luka1995/LPProjects-LED-Cube-8x8x8/Images/1.jpg

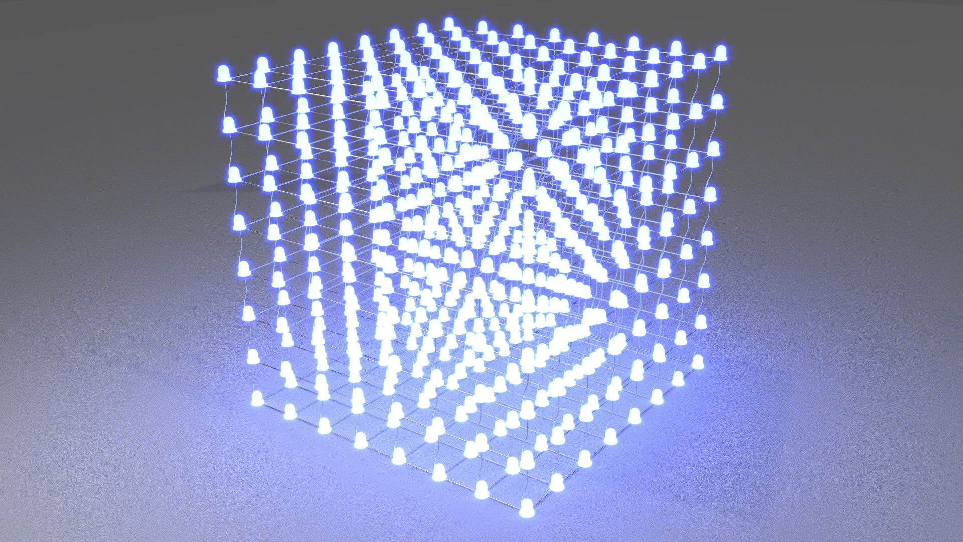
Images/1.jpg
