luka1995/LPProjects-LED-Cube-8x8x8/Images/2.jpg

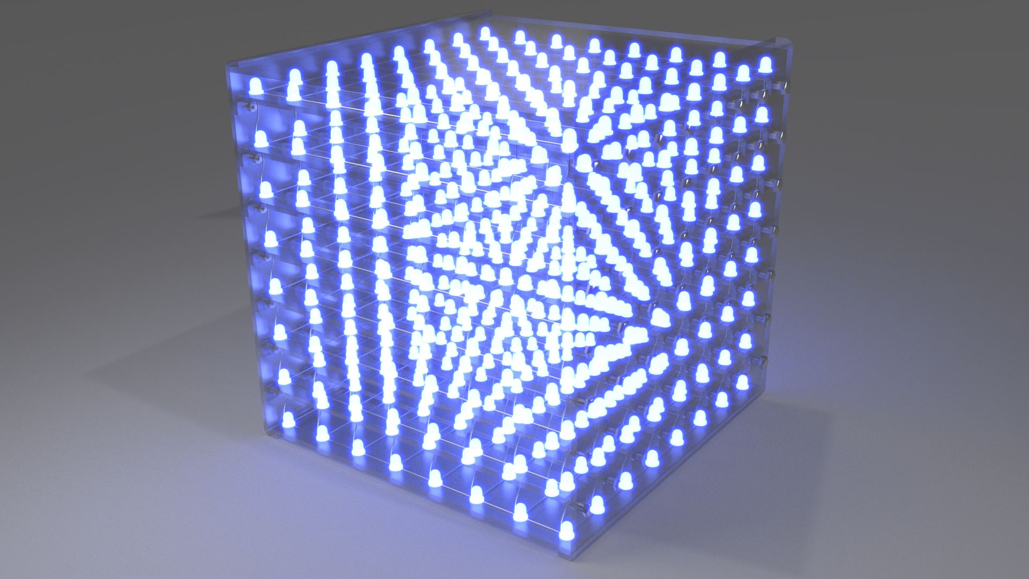
Images/2.jpg
