luka1995/LPProjects-LED-Cube-8x8x8/Images/3.jpg

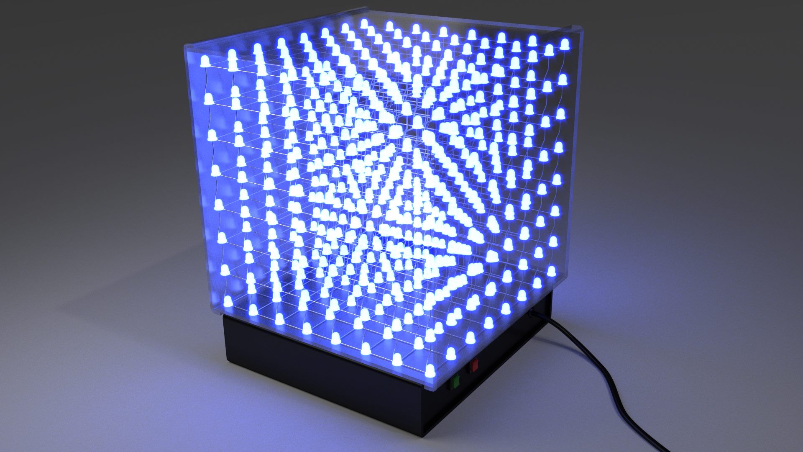
Images/3.jpg
