luka1995/LPProjects-LED-Cube-8x8x8/Images/IMG_14112014_155813.png

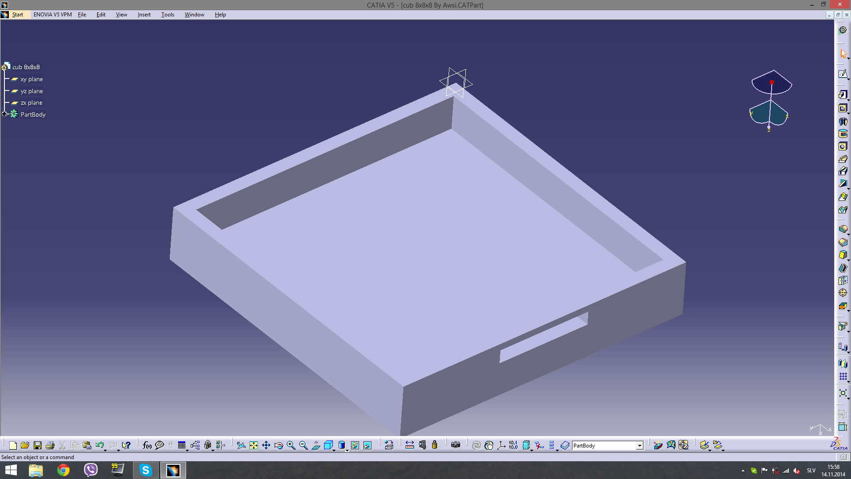
Images/IMG_14112014_155813.png
