luka1995/LPProjects-LED-Cube-8x8x8/LP_LED_CUBE_8x8x8_PCB/ver_1.0.0/Project Outputs for LP_LED_CUBE_8x8x8/PDF/Bill of Materials.PDF

Bill of Materials | Bill of Materials For Project [LP_LED_CUBE_8x8x8.PrjPcb] (No PCB Document Selected)
Source Data From: | LP_LED_CUBE_8x8x8.PrjPcb
Project: | | LP_LED_CUBE_8x8x8.PrjPcb
Variant: | | None
Creation Date: 19.8.2014 | 12:01:52
Print Date: | 19-Aug-14 | 12:01:56 PM
#Column Name Comment | #Column Name ErrDesignato r | Description | Quantity

Battery | BT1 | Multicell Battery | 1
100n | C1, C2, C3, C4, C9, C10, C12, C15, C18,
| C20 | Capacitor | 10
22p | C5, C6, C7, C8 | Capacitor | 4
220uF | C11, C14 | Capacitor | 2
0.47uF | C13, C16 | Capacitor | 2
22n | C17, C21 | Capacitor | 2
1n | C19 | Capacitor | 1
NO | C22, R2 | Capacitor, Resistor | 2
100n | C23 | Capacitor | 1
USB LED | D1 | Typical INFRARED GaAs LED | 1
LED1 | D2 | Typical INFRARED GaAs LED | 1
LED2 | D3 | Typical INFRARED GaAs LED | 1
D Schottky | D4 | Schottky Diode | 1
Schottky | D5 | Schottky Diode | 1
POWER LED | D6 | Typical INFRARED GaAs LED | 1
RS232 | J1 | Receptacle Assembly, 9 Position, Right
| | Angle | 1
Inductor | L1, L2, L3, L5, L6 | Inductor | 5
1.5uH | L4 | Magnetic-Core Inductor | 1
JTAG Connector ULINK | P1 | JTAG Connector | 1
Header 4X2A | P2 | Header, 4-Pin, Dual row | 1
USB B | P3 | USB Connector | 1
Header 8X2 | P4, P6, P7, P8 | Header, 8-Pin, Dual row | 4
Header 8 | P5 | Header, 8-Pin | 1
DC Connector | P9 | DC Power Connector | 1
NPN | Q1, Q2, Q3, Q4, Q5, Q6, Q7, Q8 | NPN Bipolar Transistor | 8
10k | R1, R5, R6, R7, R8, R9, R10, R87, R96 | Resistor | 9
2k2 | R3, R4, R97, R98, R99, R100, R101 | Resistor | 7
470R | R11, R12, R13, R91, R94, R95 | Resistor | 6
50R | R14 | Resistor | 1
4k7 | R15 | Resistor | 1
100R | R16, R17, R18, R19, R20, R21, R22, R24,
| R25, R26, R27, R28, R29, R30, R31, R32,
| R38, R39, R40, R42, R43, R44, R45, R46,
| R47, R48, R49, R50, R51, R52, R53, R54,
| R55, R56, R57, R58, R59, R60, R61, R62,
| R63, R64, R65, R66, R67, R68, R69, R70,
| R71, R72, R73, R74, R75, R76, R77, R78,
| R79, R80, R81, R82, R83, R84, R85, R86
Resistor | 64
1k | R23, R33, R34, R35, R36, R37, R41 | Resistor | 7
226k | R88 | Resistor | 1
49.9k | R89 | Resistor | 1
100k | R90 | Resistor | 1
75R | R92, R93 | Resistor | 2
4k7 | R102 | Resistor | 1
LPC1768FBD10
0 | U1 | 32-bit ARM Cortex-M3 microcontroller; up to
| | 512 kB flash and 64 kB SRAM with
| | Ethernet, USB 2.0 Host/Device/OTG, CAN | 1
MAX2232 | U2 | Dual 232 +3V3 | 1
AT45DB321D | U3 | SPI Flash 32MB | 1
PCA9555 | U4, U5, U6, U7 | I2C I/O Ports | 4
TPS56528 | U8 | Step-Down Converter 5A 4.5V-18V | 1
RJ45 Ethernet | U9 | Ethernet Connector | 1
DP83848C | U10 | Ethernet PHY | 1
Jumper | W1, W2 | Jumper Wire | 2
32.768KHz | Y1 | Crystal Oscillator | 1
12MHz | Y2 | Crystal Oscillator | 1
XTAL 50MHz | Y3 | | 1
Approved Notes | 171
