luka1995/LPProjects-LED-Cube-8x8x8/PCB/Ver 4.1.0/PCB_Controller/PDF/Schematic.PDF

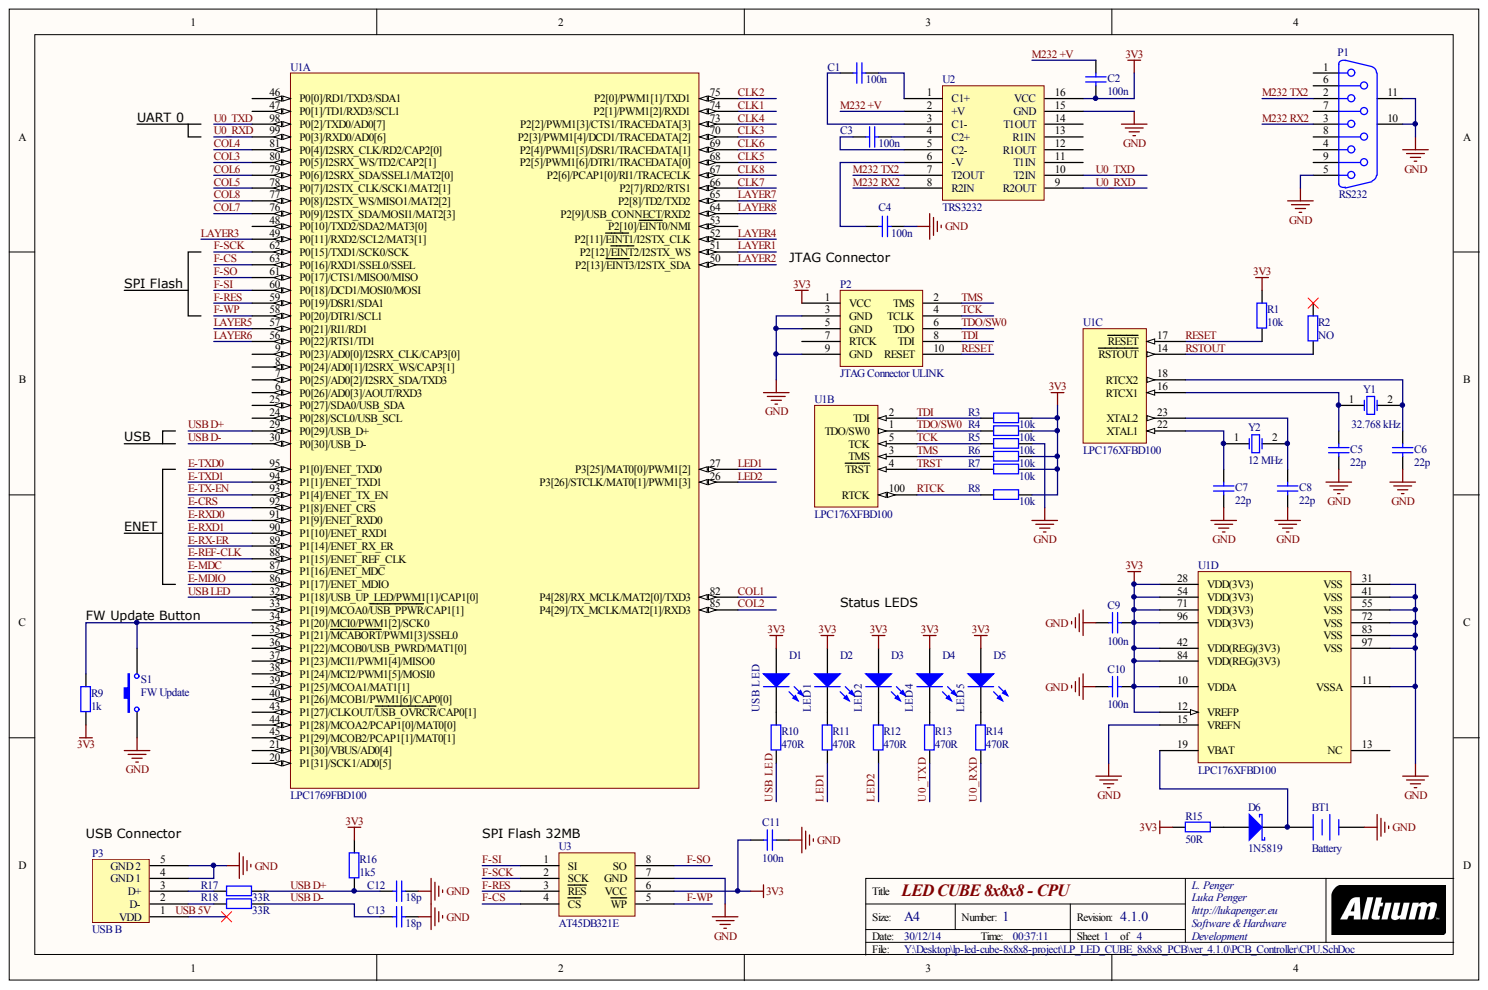
[picture p26: page 1]

LED CUBE 8x8x8 - CPU
Title
Date:
Y:\Desktop\lp-led-cube-8x8x8-project\LP_LED_CUBE_8x8x8_PCB\ver_4.1.0\PCB_Controller\CPU.SchDoc
File:

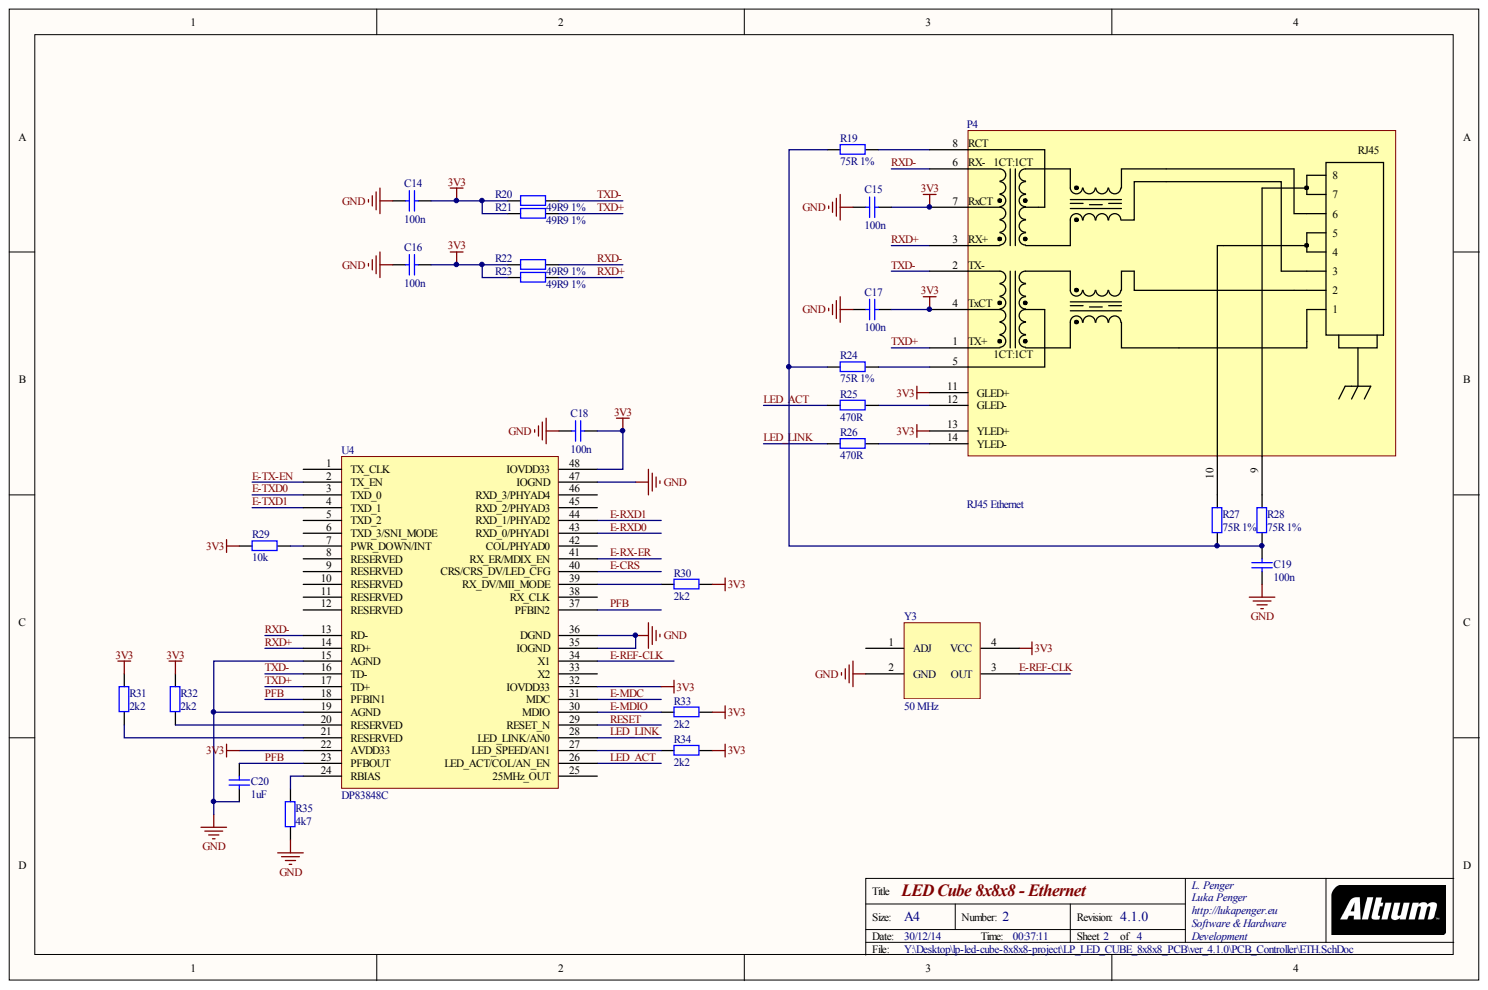
[picture p27: page 2]

GND | 75R1% RXD-6 100n 100n R24 | 1CT:1CT RxCT | 8 7 6 5 4 3 2 1

RESERVED 20 | E-MDIO RESET

RESERVED 21 AVDD33 22 PFBOUT 23 | LED_LINK LED_ACT

Title LED Cube 8x8x8 - Ethernet | L. Penger Luka Penger http://lukapenger.eu Software & Hardware Development

Size: A4 | Number: 2 | Revision: 4.1.0

1 2 | Date: 30/12/14 Time: 00:37:11 Sheet 2 of 4 File: Y:\Desktop\lp-led-cube-8x8x8-project\LP_LED_CUBE_8x8x8_PCB\ver_4.1.0\PCB_Controller\ETH.SchDoc 3 4

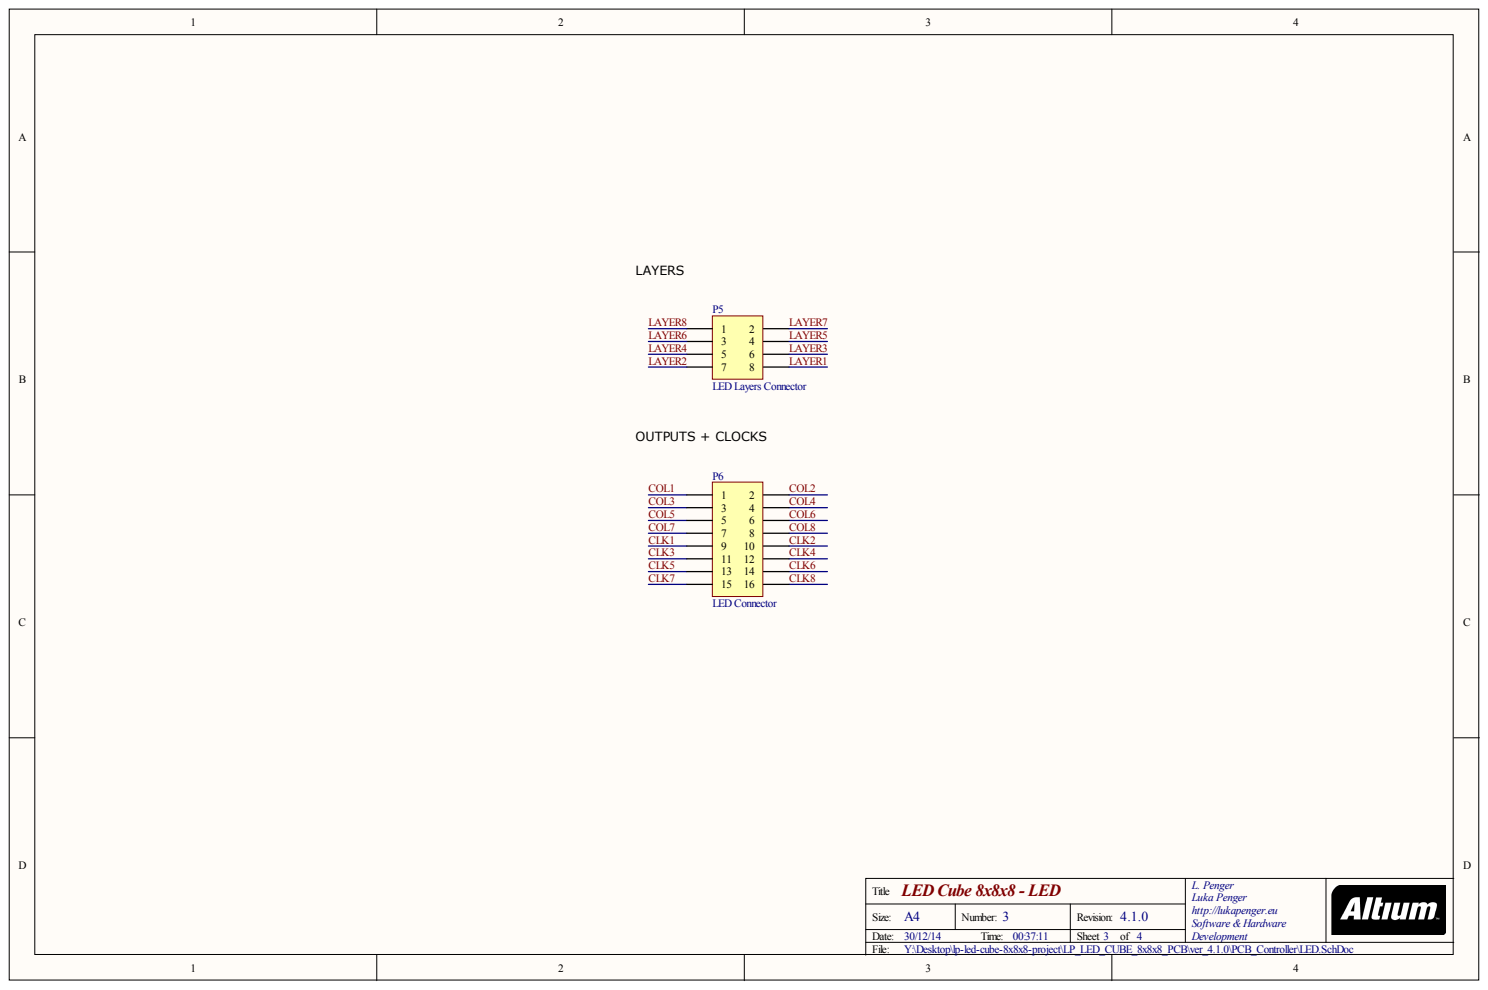
[picture p28: page 3]

Title LED Cube 8x8x8 - LED | L. Penger Luka Penger http://lukapenger.eu Software & Hardware Development

Size: A4 | Number: 3 | Revision: 4.1.0

1 2 | Date: 30/12/14 Time: 00:37:11 Sheet 3 of 4 File: Y:\Desktop\lp-led-cube-8x8x8-project\LP_LED_CUBE_8x8x8_PCB\ver_4.1.0\PCB_Controller\LED.SchDoc 3 4

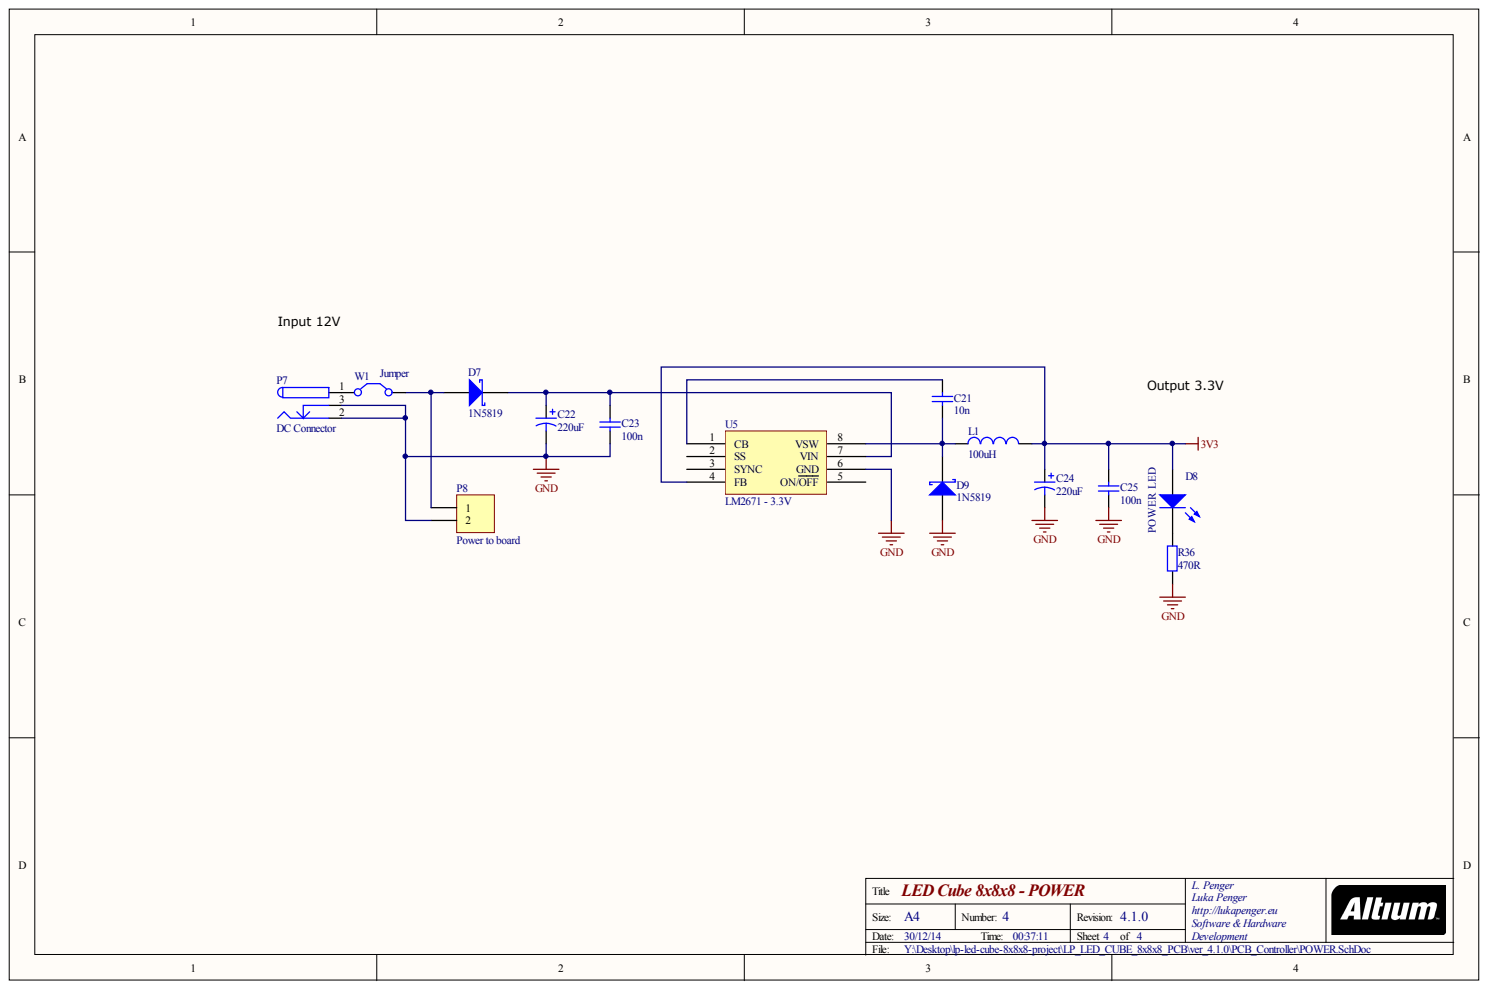
[picture p29: page 4]

: A4 | Numb er : 4 | Re vis io n: 4.1.0
Date : 3 0 / 1 2 / 1 4 Time : 0 0 : 3 7 : 1 1 F ile : Y :\D e s ktop \lp -le d -cub e -8 x8 x8 -p roj e c t\LP | S he e t 4 o f 4 _LED_C UBE_ 8 x8 x8 _P C | B\ver_4 . 1 . 0 \P C B_C o ntro ller\P O | WER. S c hDo c

LED Cub e 8x8x8 -PO WER | L L . u Penge k a P enge r r h t tp : //lu k ap enge r. e u Soft w a re & Ha rdw a re De v e lop m e n t

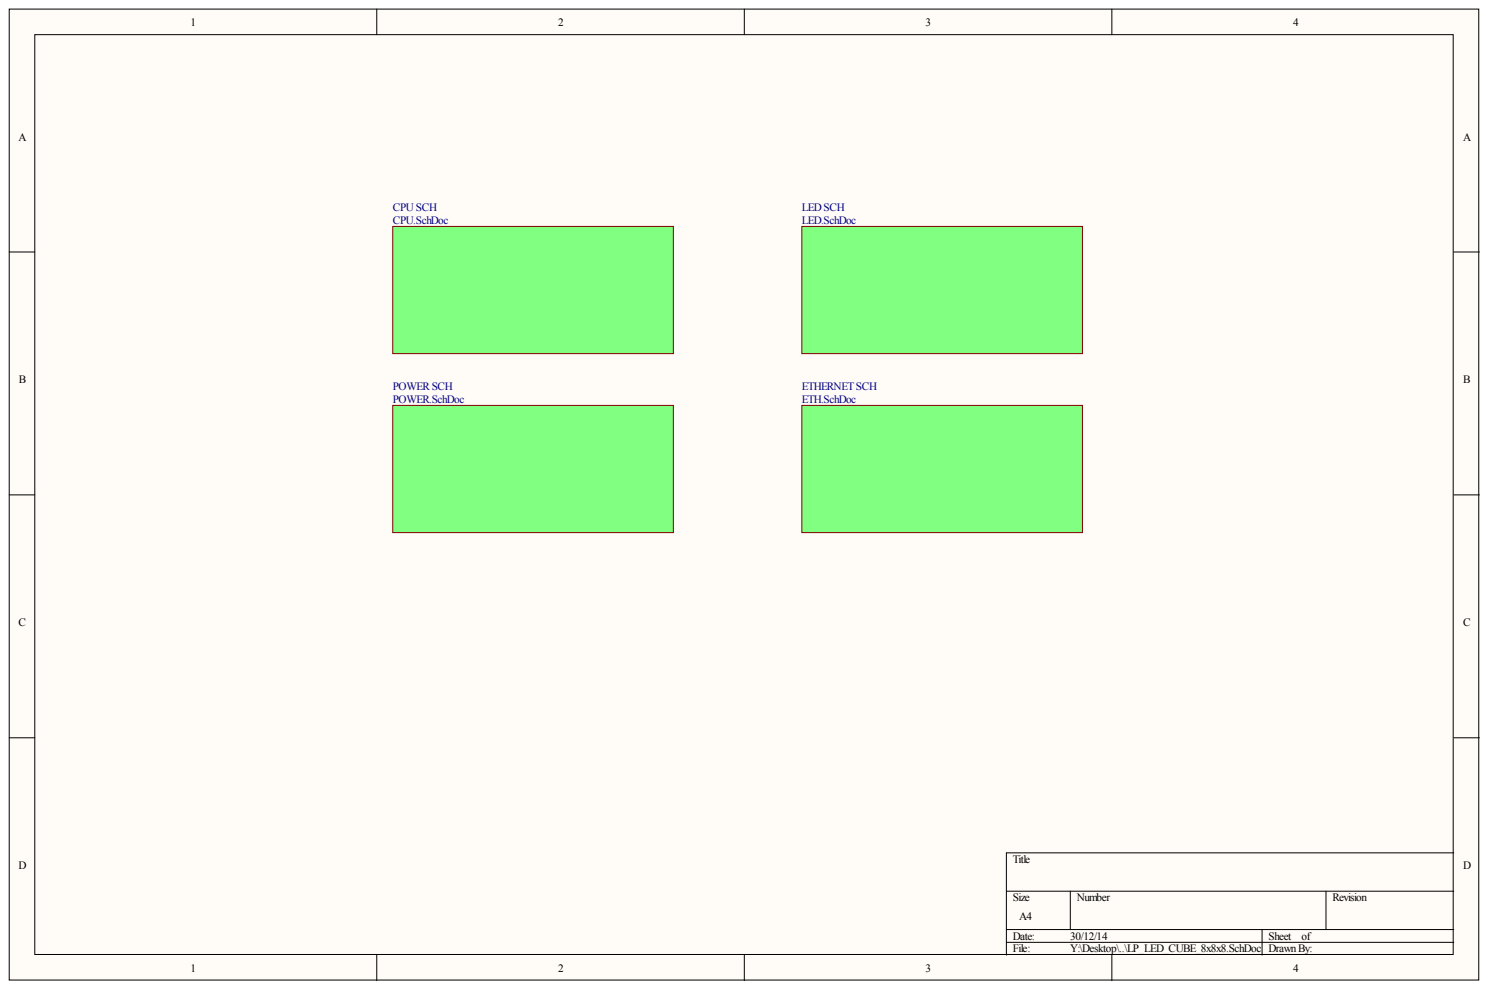
[picture p30: page 5]

Size A4 | Number | Revision

1 2 3 | Date: 30/12/14 File: Y:\Desktop\..\LP_LED_CUBE_8x8x8.SchDoc | Sheet of DrawnBy: 4
