luka1995/LPProjects-LED-Cube-8x8x8/PCB/Ver 4.1.0/PCB_Board/PDF/BOTTOM Layer.PDF

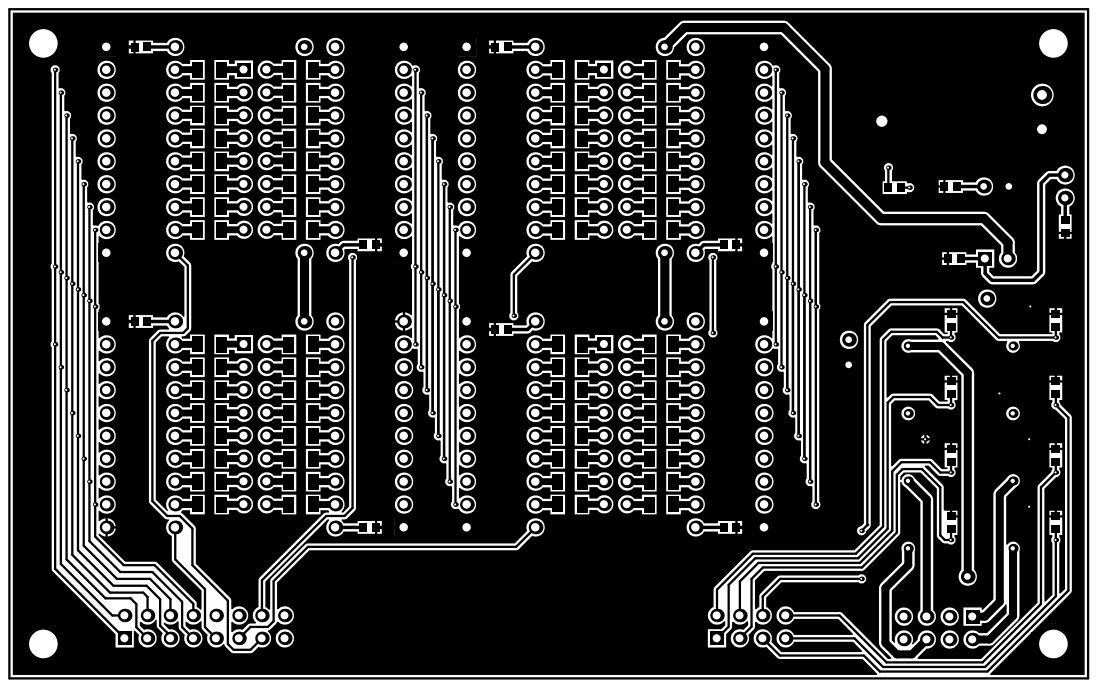
[picture p31: page 1]
