luka1995/LPProjects-LED-Cube-8x8x8/PCB/Ver 4.1.0/PCB_Board/PDF/TOP Overlay.PDF

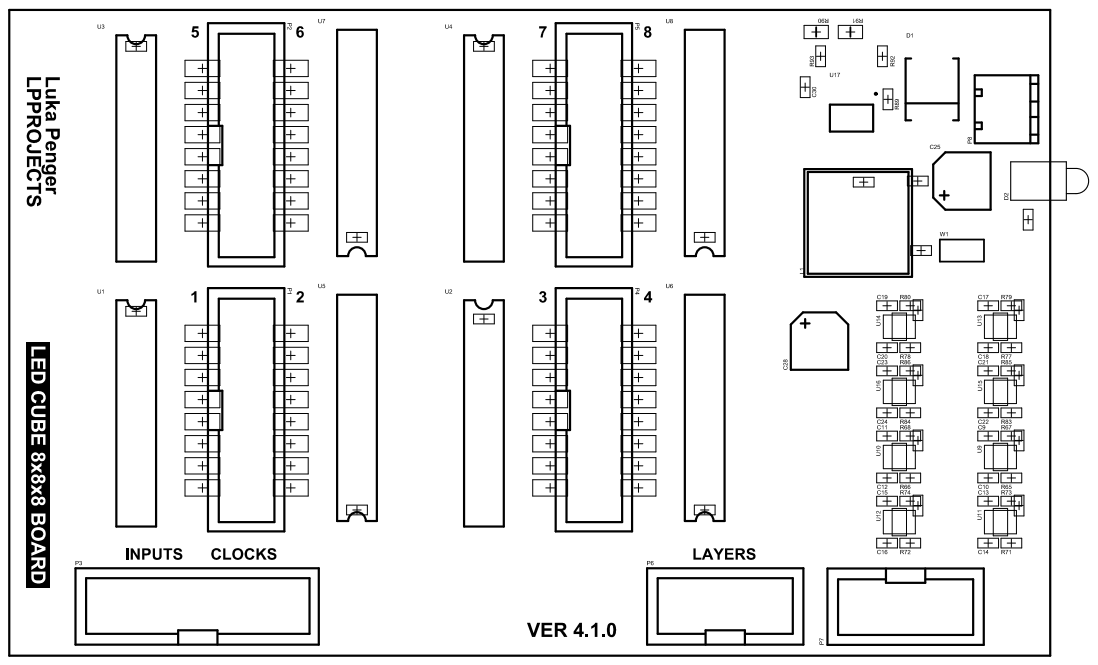
[picture p34: page 1]
