luka1995/LPProjects-LED-Cube-8x8x8/PCB/Ver 4.1.0/PCB_Controller/PDF/TOP Layer.PDF

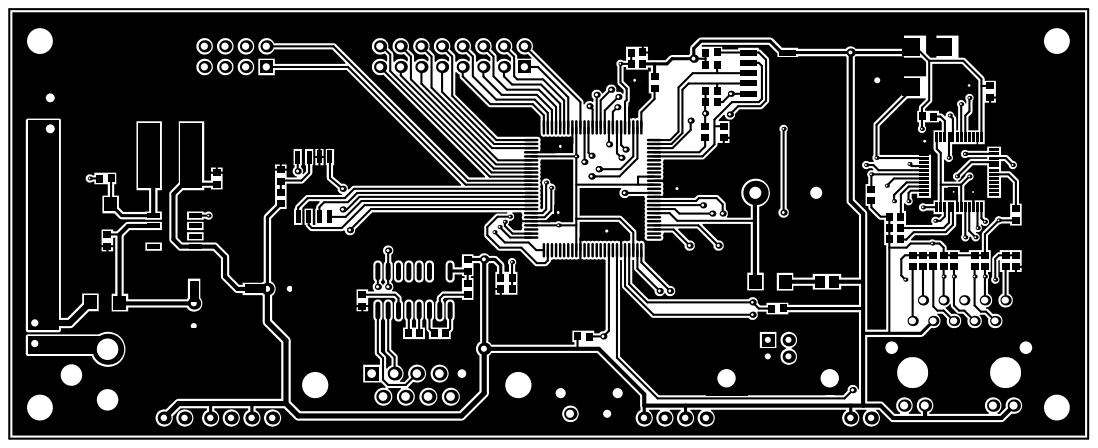
[picture p37: page 1]
