luka1995/LPProjects-LED-Cube-8x8x8/LP_LED_CUBE_8x8x8_PCB/ver_1.0.0/Project Outputs for LP_LED_CUBE_8x8x8/PDF/Schematic.PDF

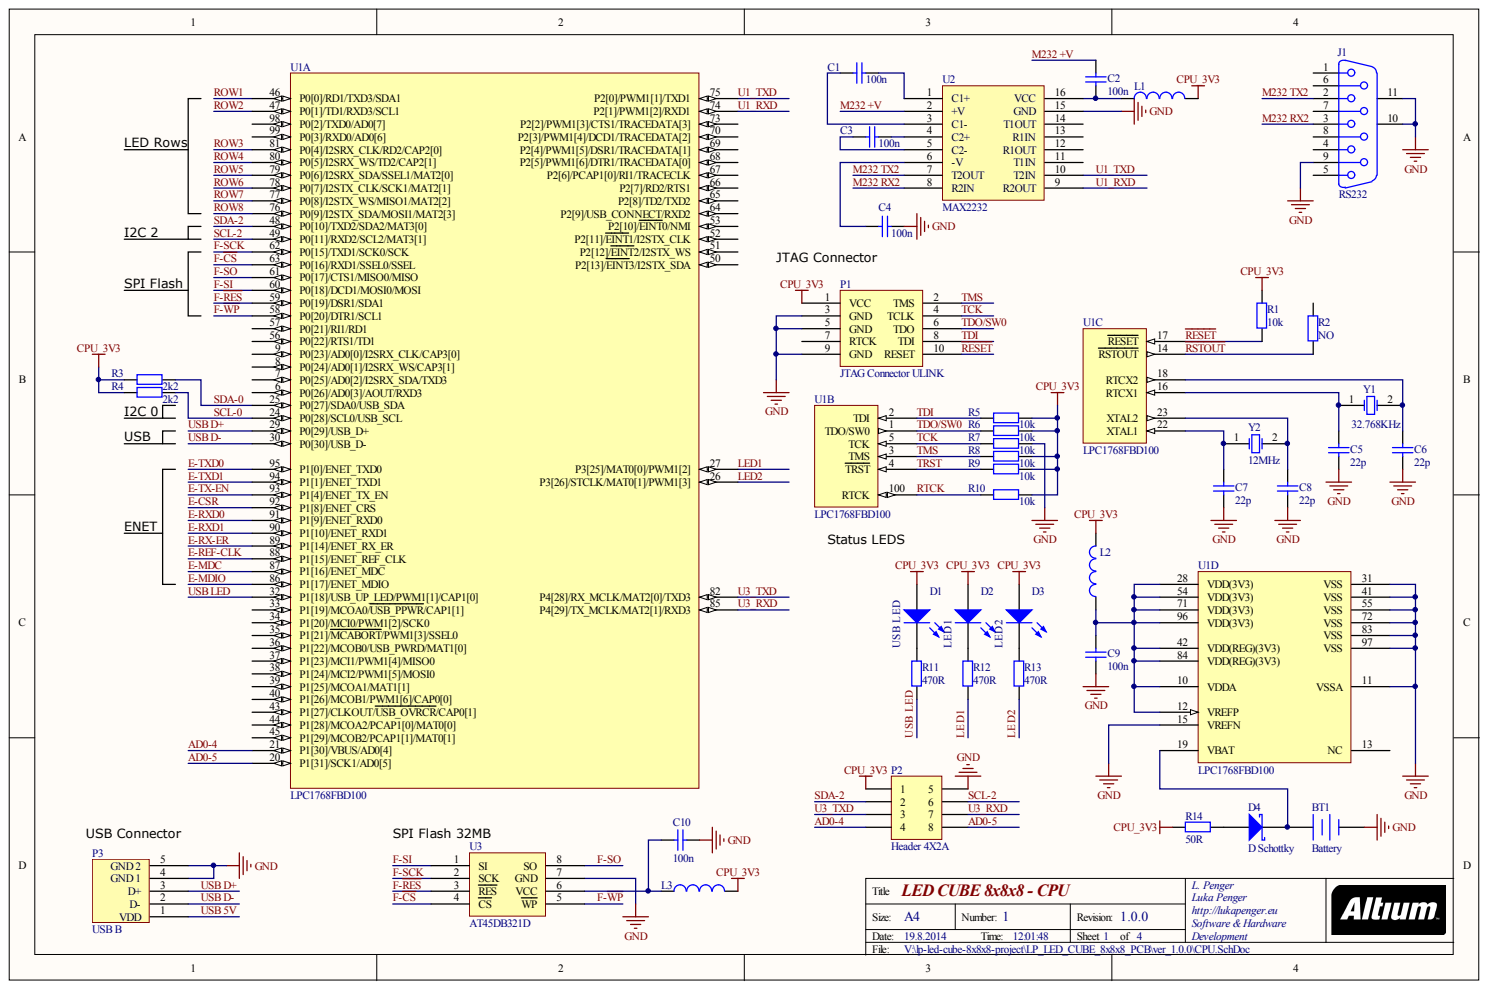
[picture p44: page 1]

LED CUBE 8x8x8 - CPU
Title
V:\lp-led-cube-8x8x8-project\LP_LED_CUBE_8x8x8_PCB\ver_1.0.0\CPU.SchDoc
File:

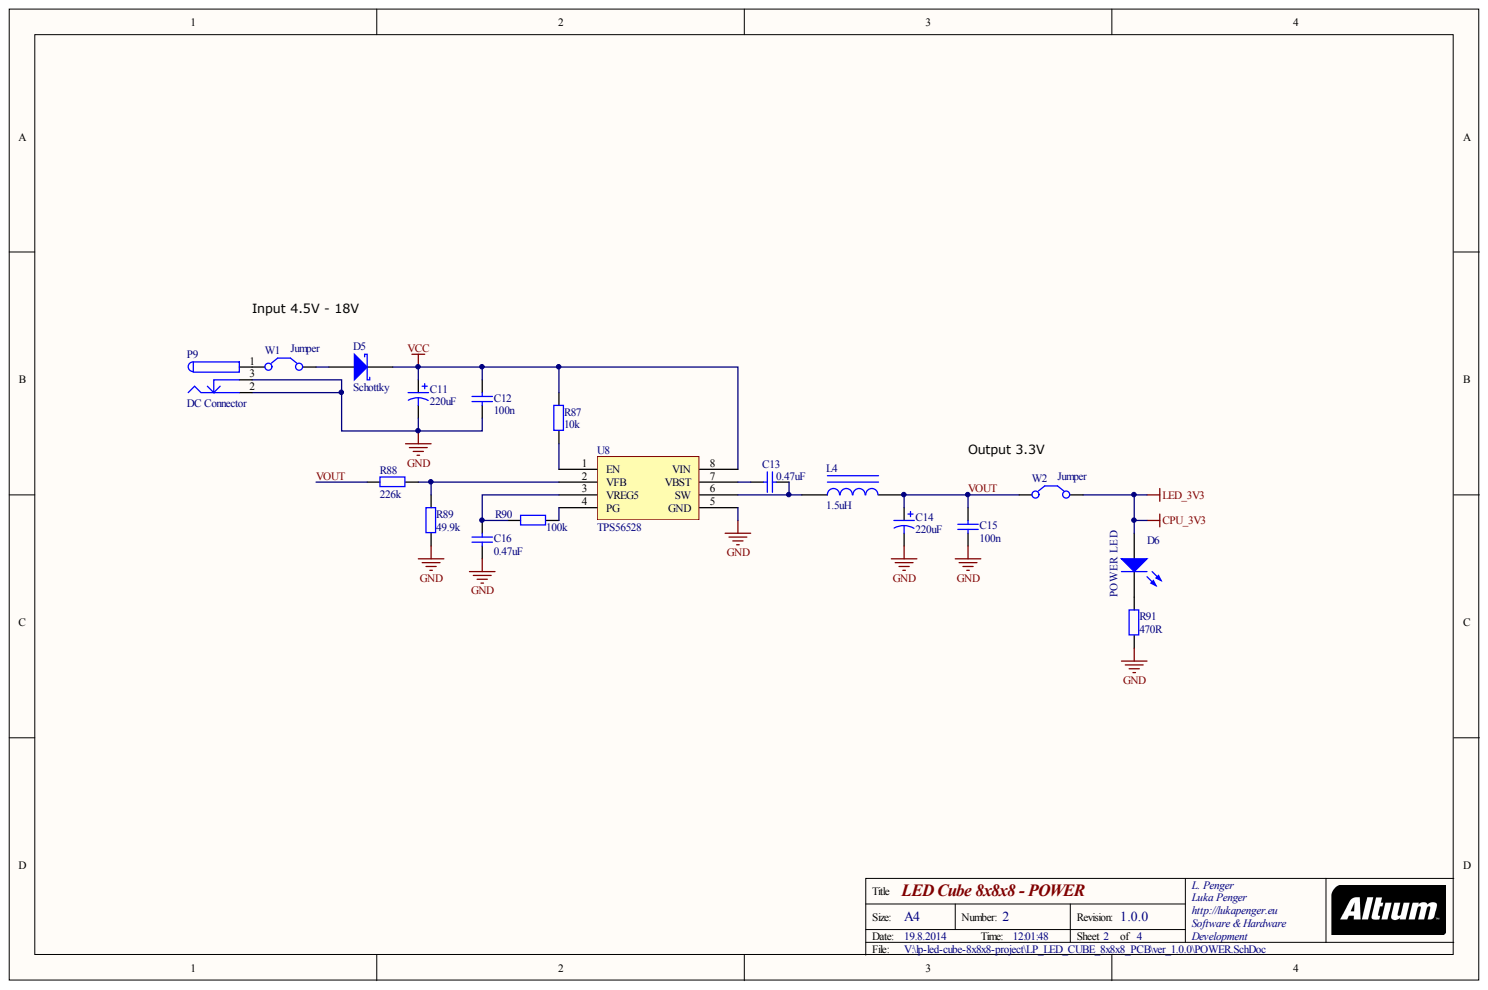
[picture p45: page 2]

: A4 | Numb er : 2 | Re vis io n: 1.0.0
Date : 1 9 . 8 . 2 0 1 4 Time : 1 2 : 0 1 :4 8 F ile : V :\lp -le d -cub e -8 x8 x8 -p roj e c t\LP _LED_C | S he e t 2 o f 4 UBE_ 8 x8 x8 _P C B\ver_ 1 | . 0 . 0 \P O WER. S c hDo c

LED Cub e 8x8x8 -PO WER | L L . u Penge k a P enge r r h t tp : //lu k ap enge r. e u Soft w a re & Ha rdw a re De v e lop m e n t

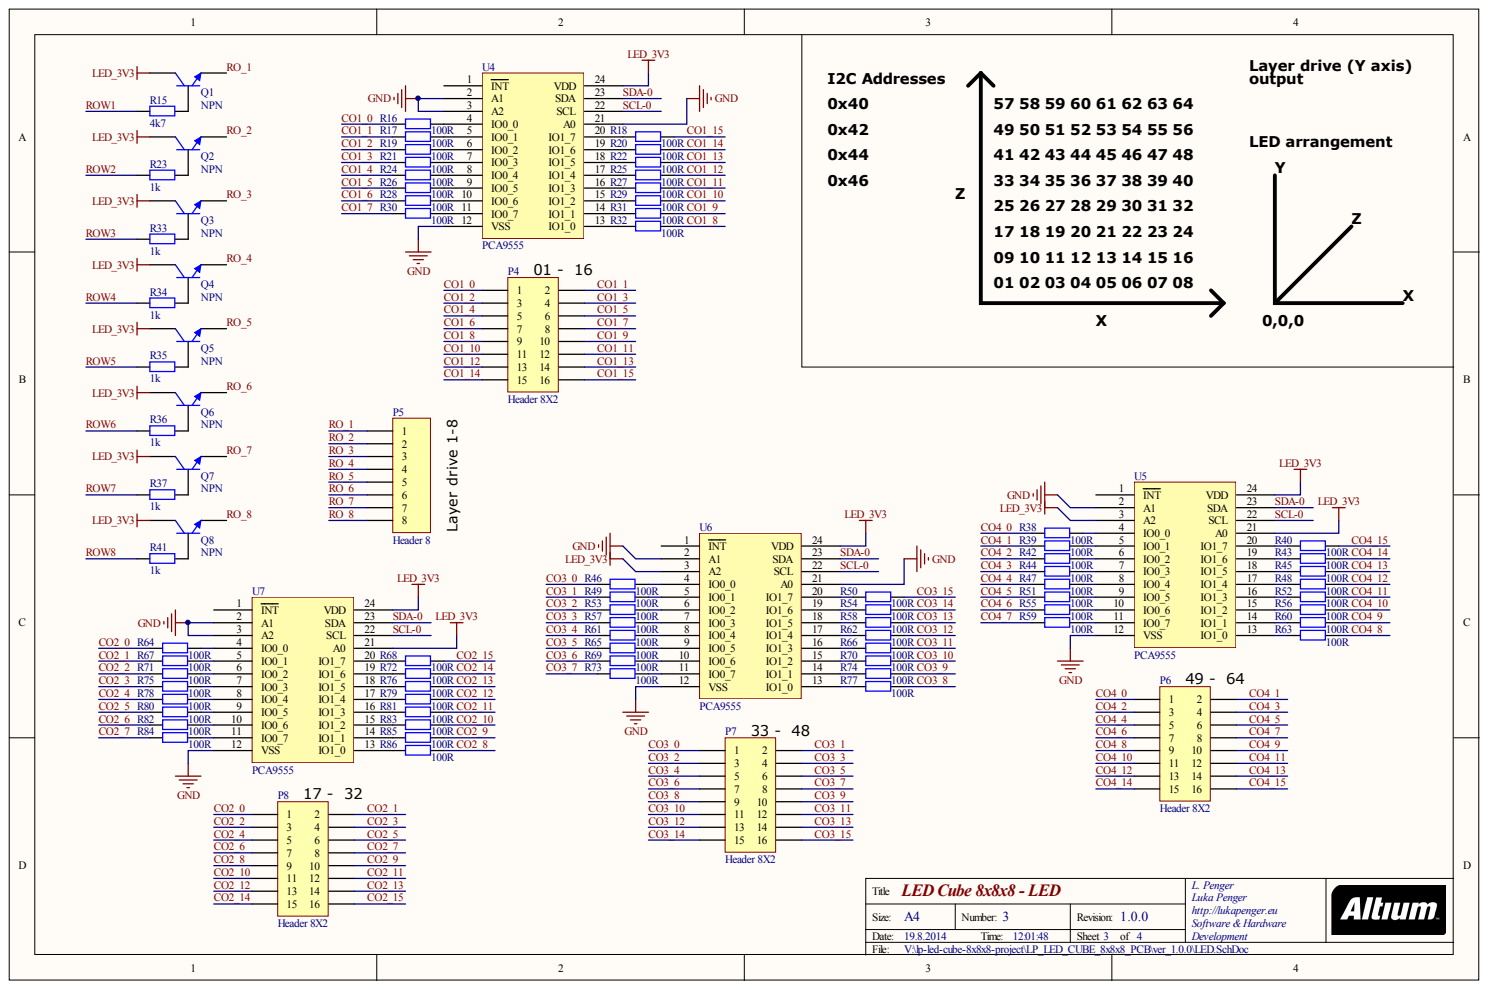
[picture p46: page 3]

LED_3V3

Layer drive (Y axis) output

R79 100R CO2_12 R81 100R CO2_11 PCA9555 R83 100R CO2_10 33 - 48 | 1 2 3 4 5 6 7 8 9 11 12 10 13 14 15 16

LED Cube 8x8x8 - LED
Title
V:\lp-led-cube-8x8x8-project\LP_LED_CUBE_8x8x8_PCB\ver_1.0.0\LED.SchDoc
File:

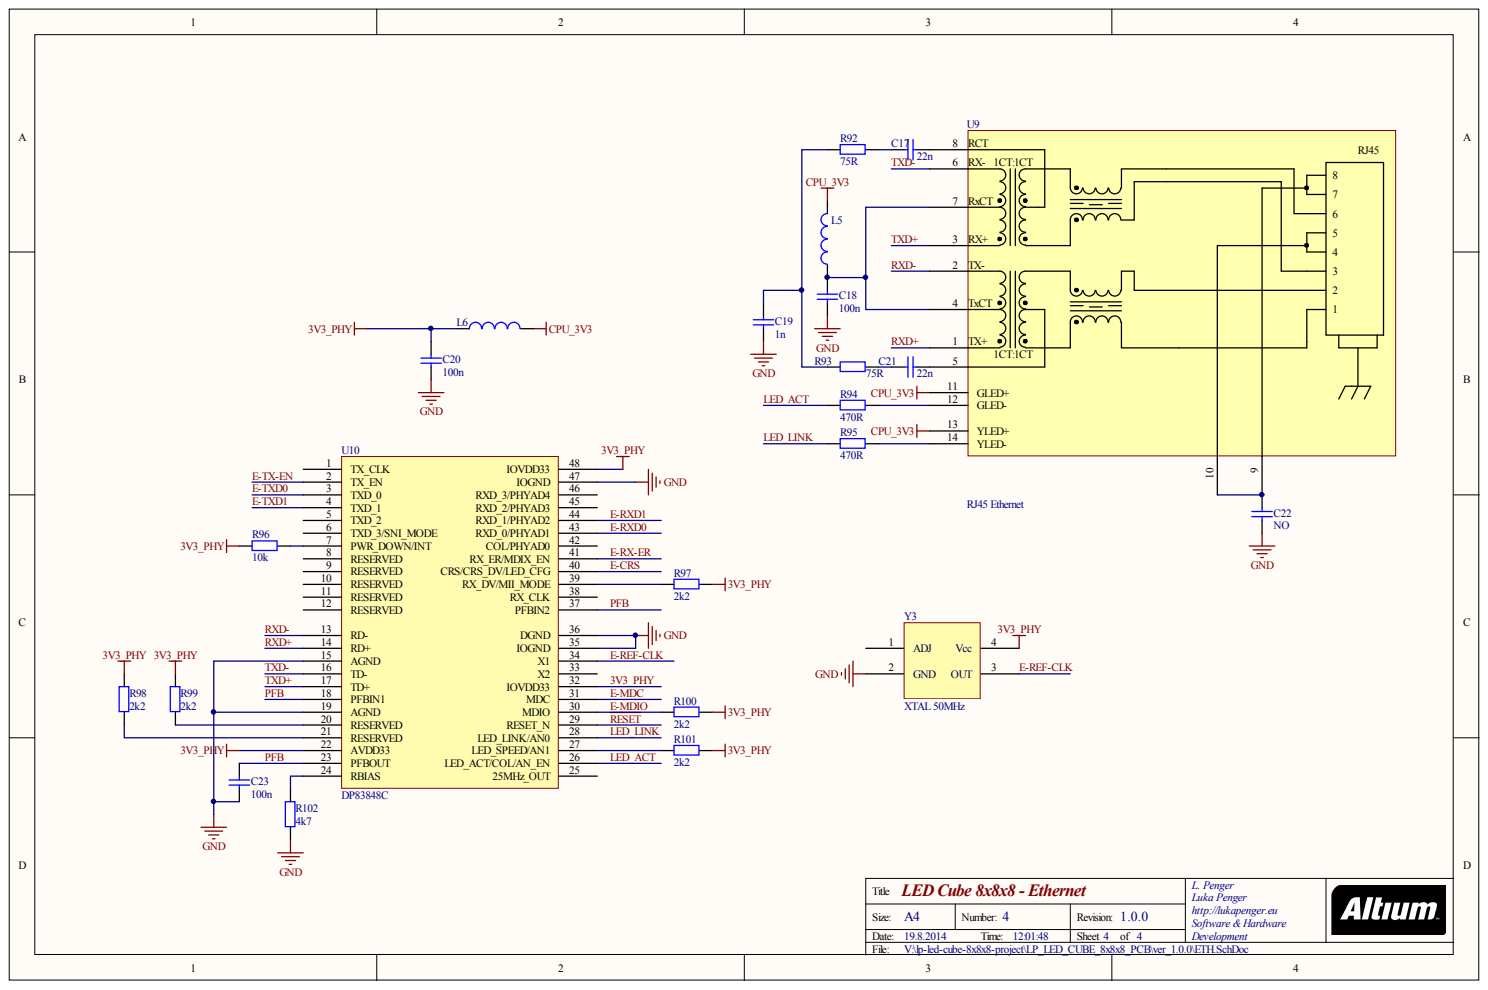
[picture p47: page 4]

TX+ TxCT TX- RX+ RxCT RX- RCT U9RJ45 Etherne
TXD+ TXD-

2 0 | 3 1 E-MDC 3 0 E-MDI O 2 9 RES ET

: A4 | Numb er : 4 | Re vis io n: 1.0.0
Date : 1 9 . 8 . 2 0 1 4 Time : 1 2 : 0 1 :4 8 F ile : V :\lp -le d -cub e -8 x8 x8 -p roj e c t\LP _LED_C | S he e t 4 o f 4 UBE_ 8 x8 x8 _P C B\ver_ 1 | . 0 . 0 \ETH . S c hDo c

LED Cub e 8x8x8 -Eth e rn e t | L L . u Penge k a P enge r r h t tp : //lu k ap enge r. e u Soft w a re & Ha rdw a re De v e lop m e n t

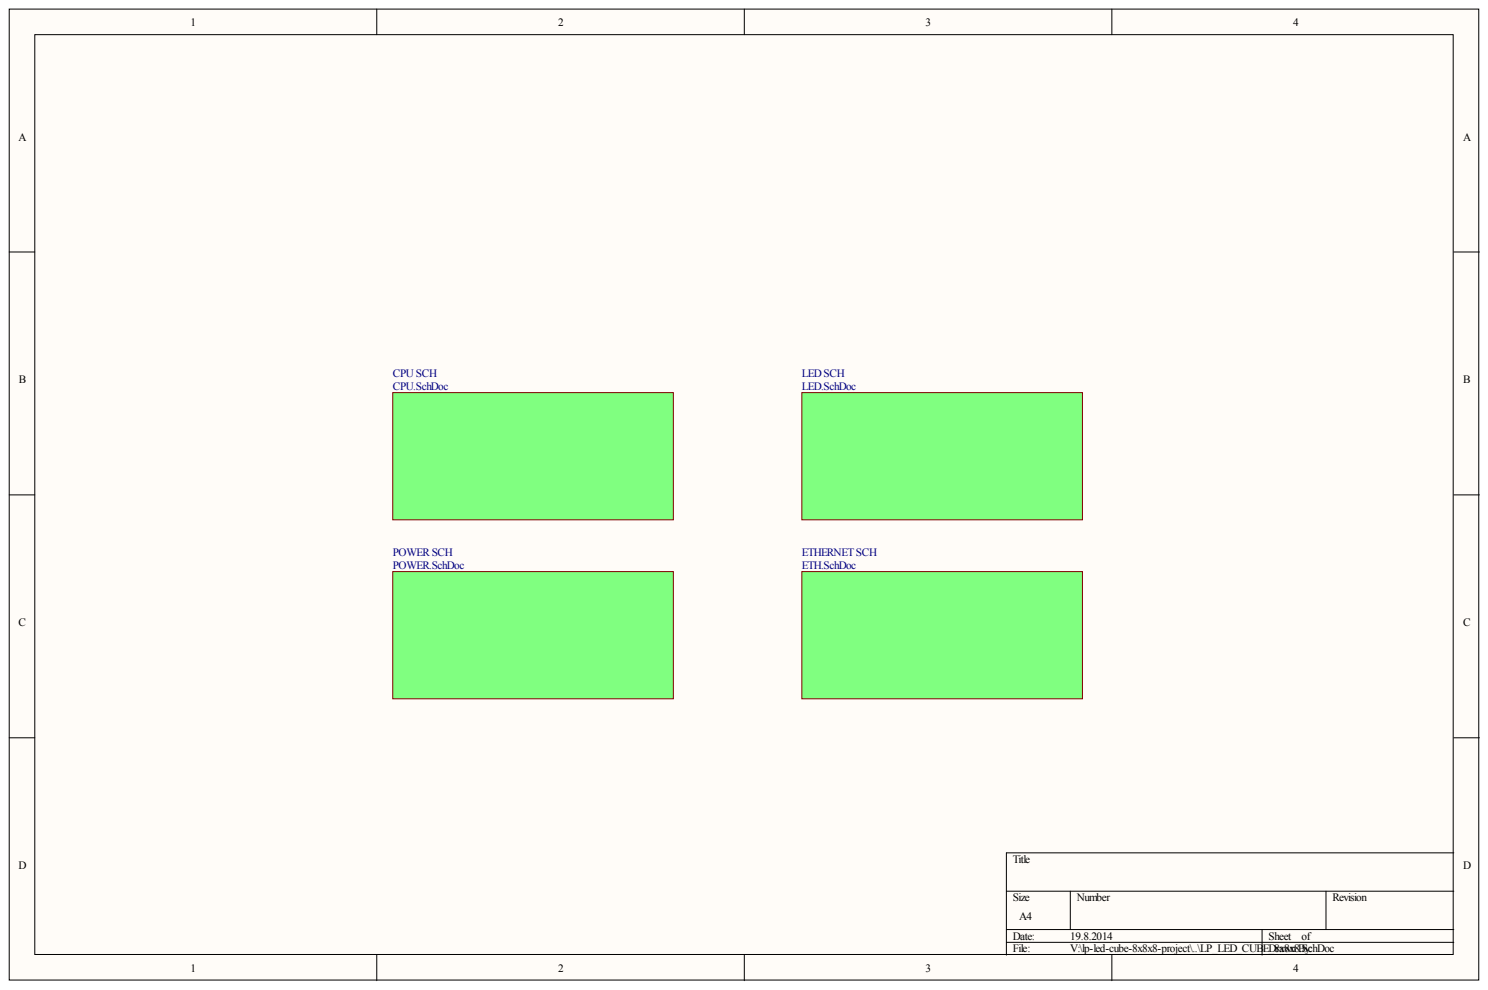
[picture p48: page 5]

Size A4 | Number | Revision

1 2 3 | Date: 19.8.2014 File: V:\lp-led-cube-8x8x8-project\..\LP_LED_CUBED_8raxw8xn8B.Syc:hDoc | Sheet of 4
