luka1995/LPProjects-LED-Cube-8x8x8/LP_LED_CUBE_8x8x8_PCB/ver_2.0.0/Project Outputs for LP_LED_CUBE_8x8x8/PDF/Schematic.PDF

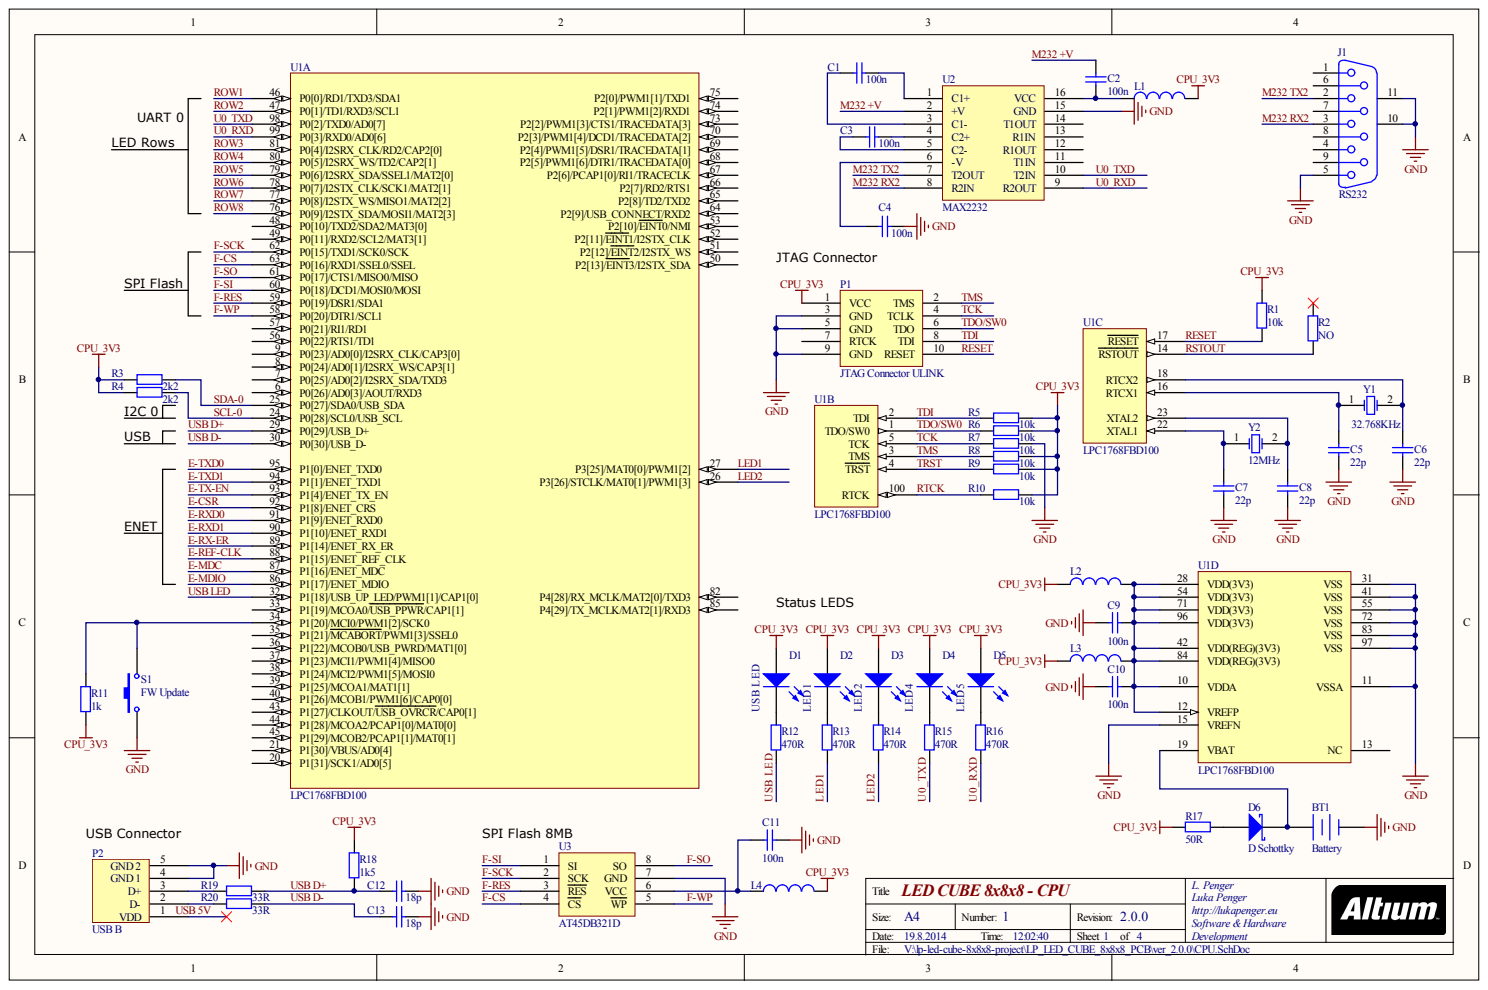
[picture p53: page 1]

LED CUBE 8x8x8 - CPU
Title
V:\lp-led-cube-8x8x8-project\LP_LED_CUBE_8x8x8_PCB\ver_2.0.0\CPU.SchDoc
File:

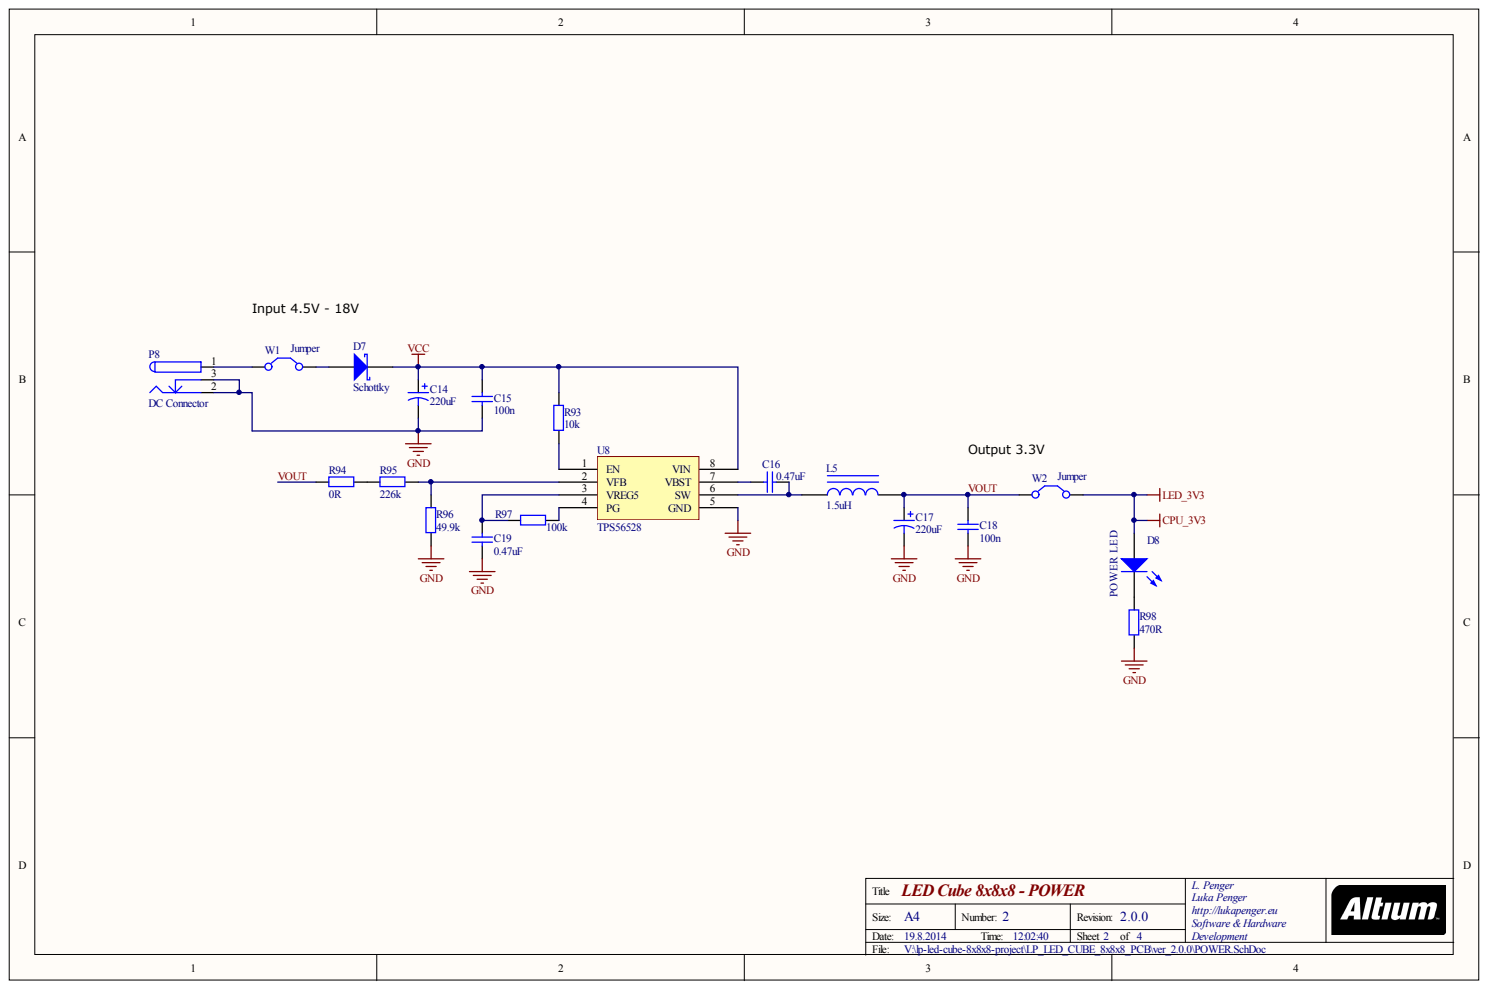
[picture p54: page 2]

: A4 | Numb er : 2 | Re vis io n: 2.0.0
Date : 1 9 . 8 . 2 0 1 4 Time : 1 2 : 0 2 :4 0 F ile : V :\lp -le d -cub e -8 x8 x8 -p roj e c t\LP _LED_C | S he e t 2 o f 4 UBE_ 8 x8 x8 _P C B\ver_2 | . 0 . 0 \P O WER. S c hDo c

LED Cub e 8x8x8 -PO WER | L L . u Penge k a P enge r r h t tp : //lu k ap enge r. e u Soft w a re & Ha rdw a re De v e lop m e n t

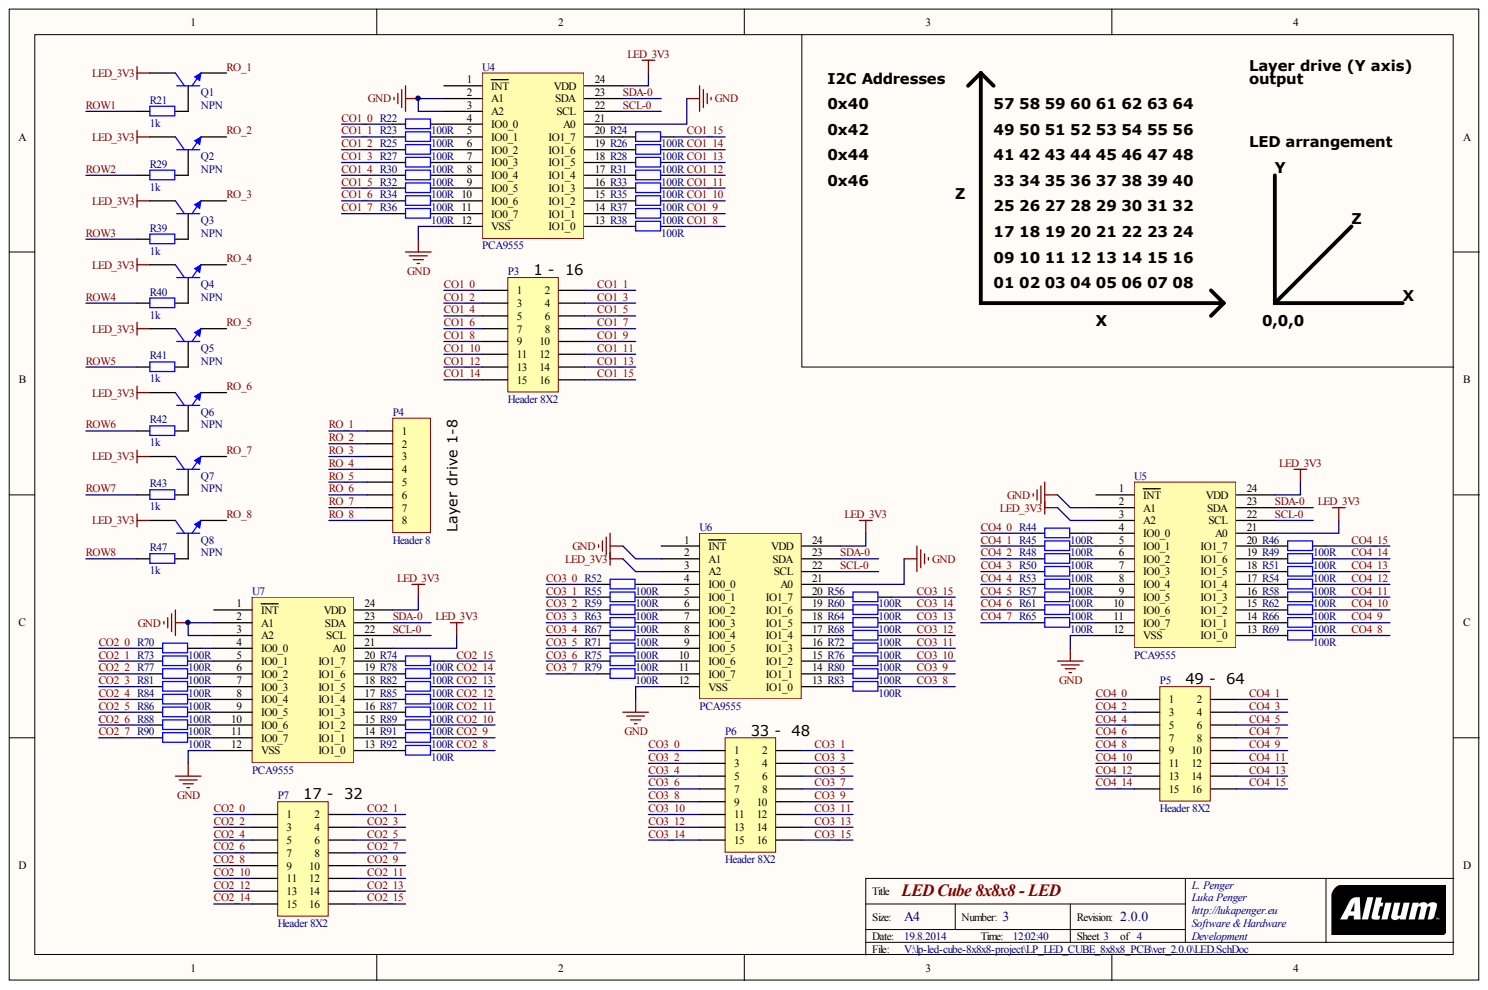
[picture p55: page 3]

Date : 1 9 . 8 . 2 0 1 4 Time : 1 2 : 0 2 :4 0 F ile : V :\lp -le d -cub e -8 x8 x8 -p roj e c t\LP _LED_C | S he e t 3 o f 4 UBE_ 8 x8 x8 _P C B\ver_2 | . 0 . 0 \LED . S c hDo c

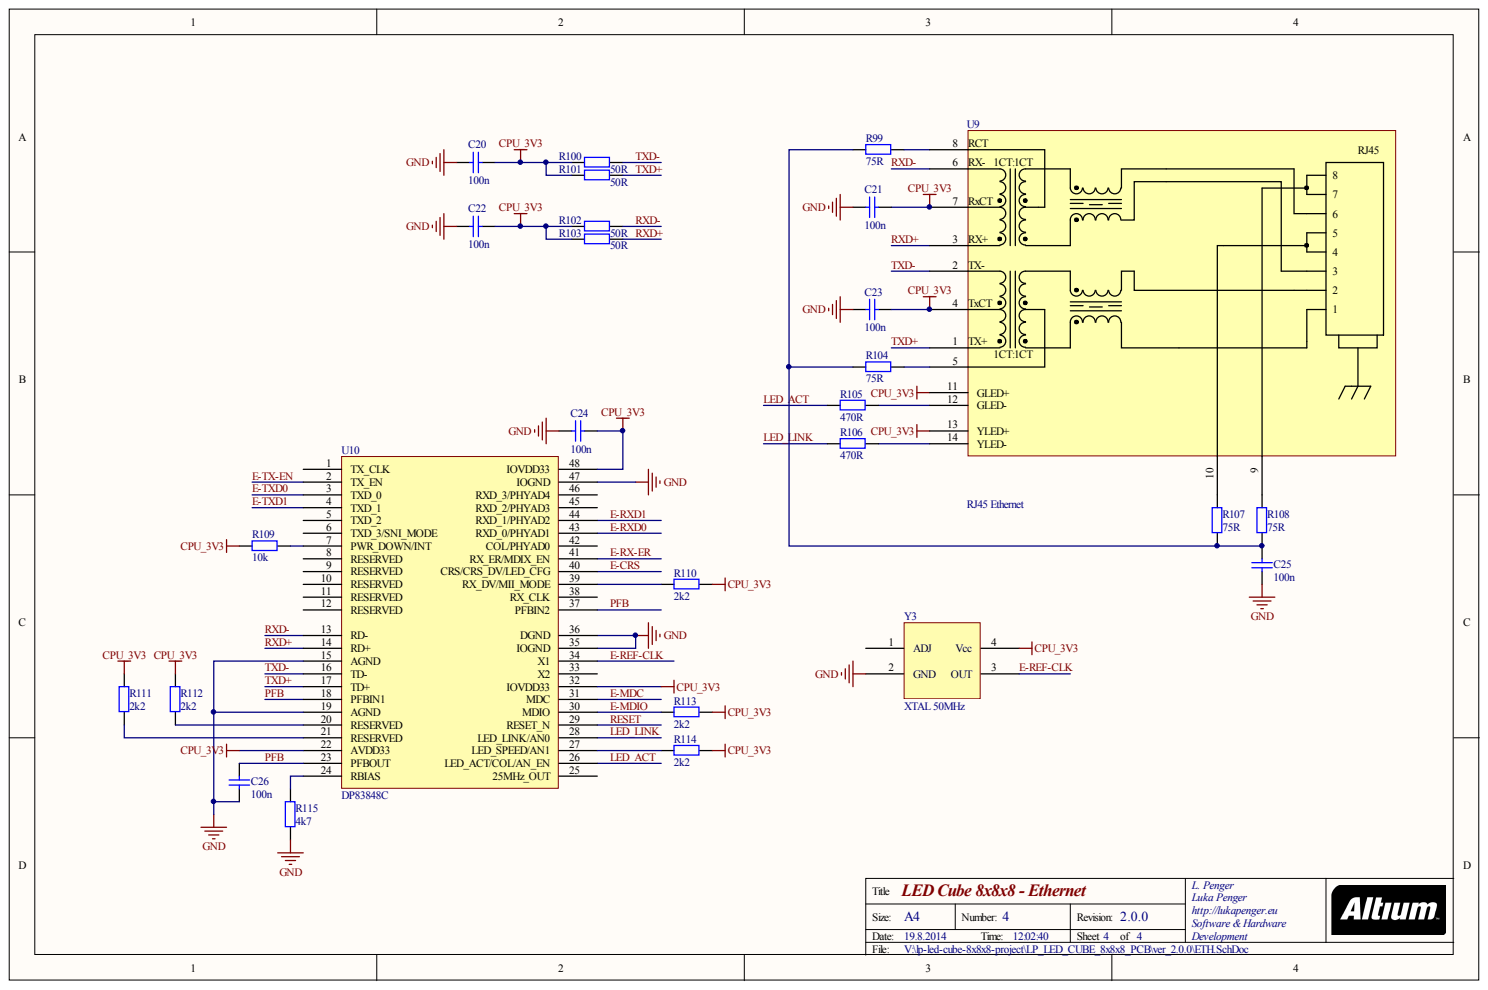
[picture p56: page 4]

RESERVED 20 | E-MDIO RESET

RESERVED 21 AVDD33 22 PFBOUT 23 | LED_LINK LED_ACT

Title LED Cube 8x8x8 - Ethernet | L. Penger Luka Penger http://lukapenger.eu Software & Hardware Development

Size: A4 | Number: 4 | Revision: 2.0.0

1 2 | Date: 19.8.2014 Time: 12:02:40 Sheet 4 of 4 File: V:\lp-led-cube-8x8x8-project\LP_LED_CUBE_8x8x8_PCB\ver_2.0.0\ETH.SchDoc 3 4


Size A4 | Number | Revision

1 2 3 | Date: 19.8.2014 File: V:\lp-led-cube-8x8x8-project\..\LP_LED_CUBED_8raxw8xn8B.Syc:hDoc | Sheet of 4
