luka1995/LPProjects-LED-Cube-8x8x8/LP_LED_CUBE_8x8x8_PCB/ver_3.0.0/Project Outputs for LP_LED_CUBE_8x8x8/PDF/Schematic.PDF

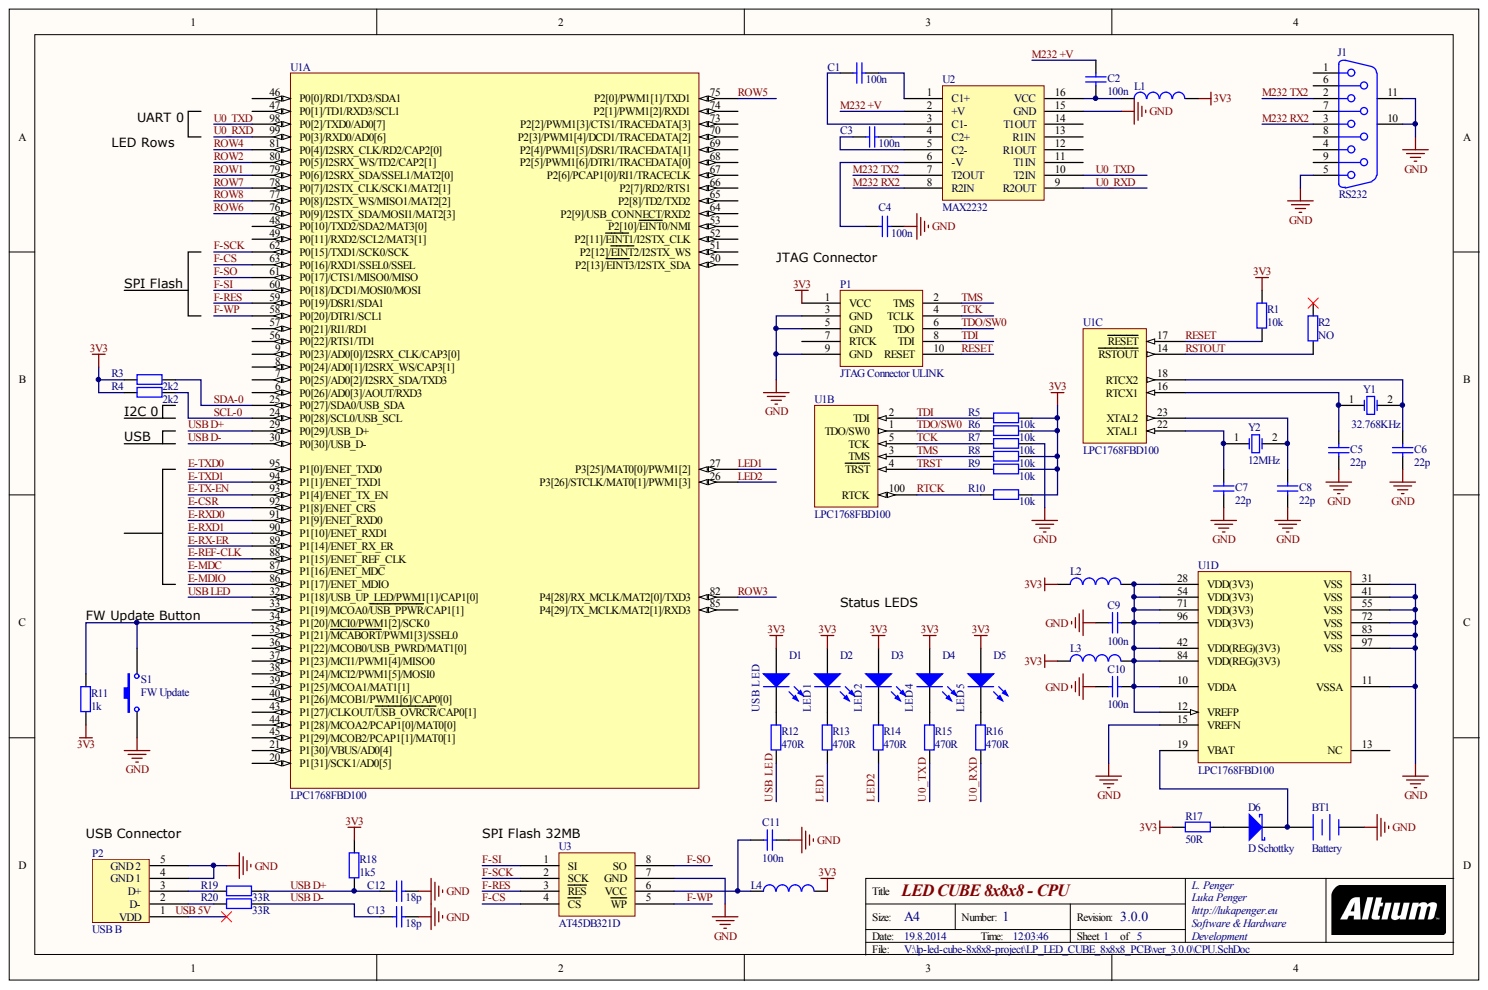
[picture p63: page 1]

LED CUBE 8x8x8 - CPU
Title
V:\lp-led-cube-8x8x8-project\LP_LED_CUBE_8x8x8_PCB\ver_3.0.0\CPU.SchDoc
File:

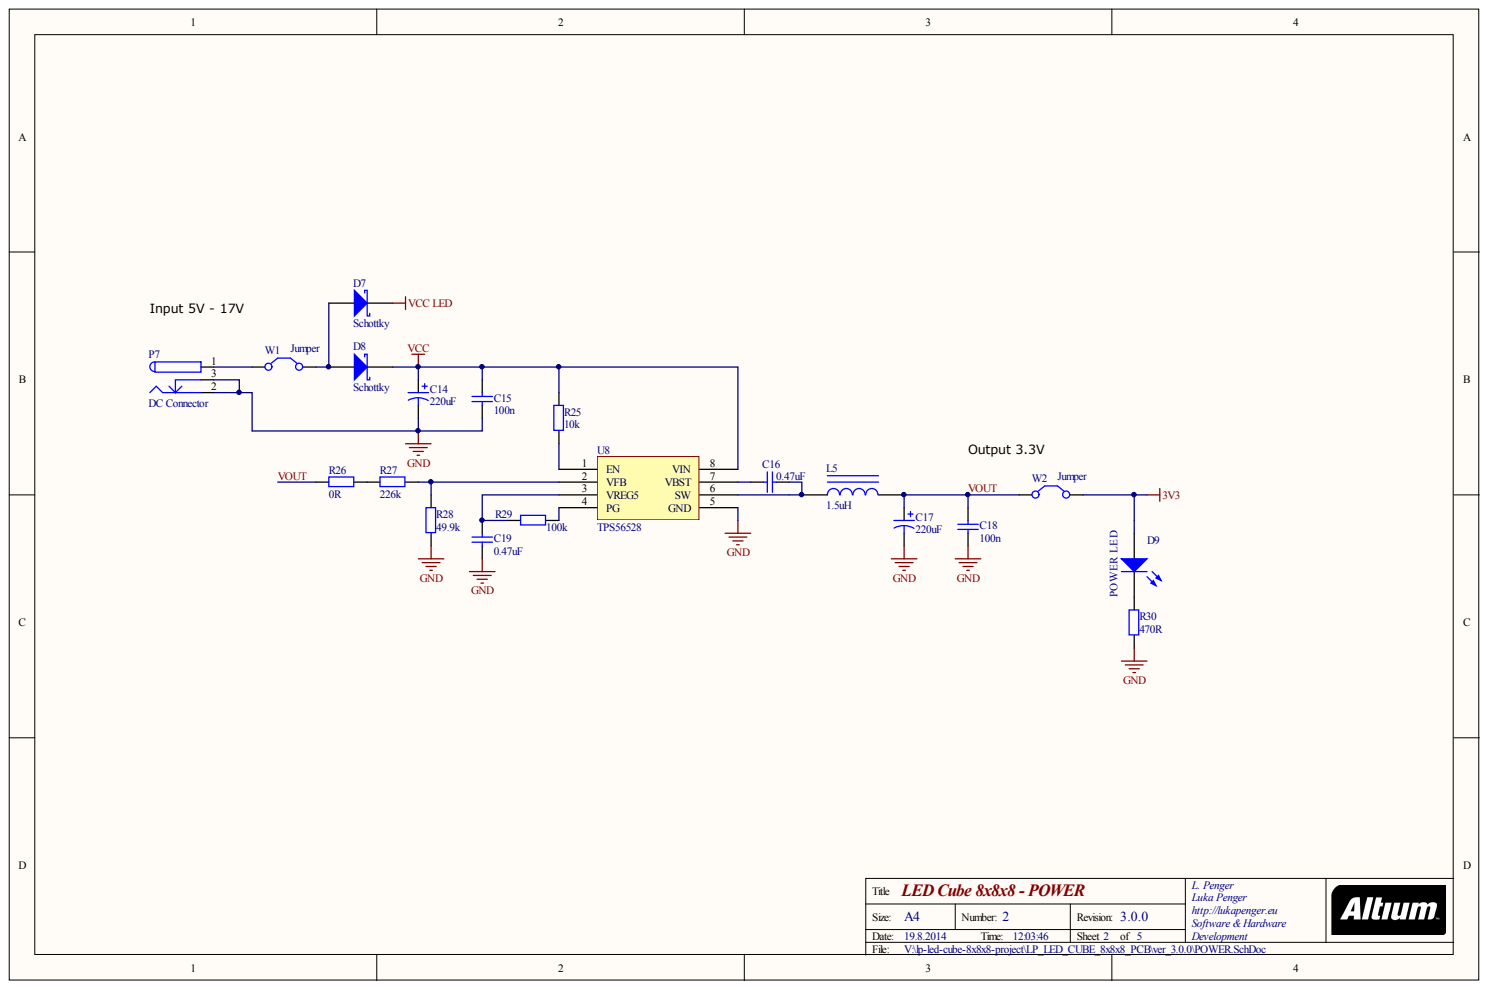
[picture p64: page 2]

: A4 | Numb er : 2 | Re vis io n: 3.0.0
Date : 1 9 . 8 . 2 0 1 4 Time : 1 2 : 0 3 :4 6 F ile : V :\lp -le d -cub e -8 x8 x8 -p roj e c t\LP _LED_C | S he e t 2 o f 5 UBE_ 8 x8 x8 _P C B\ver_3 | . 0 . 0 \P O WER. S c hDo c

LED Cub e 8x8x8 -PO WER | L L . u Penge k a P enge r r h t tp : //lu k ap enge r. e u Soft w a re & Ha rdw a re De v e lop m e n t

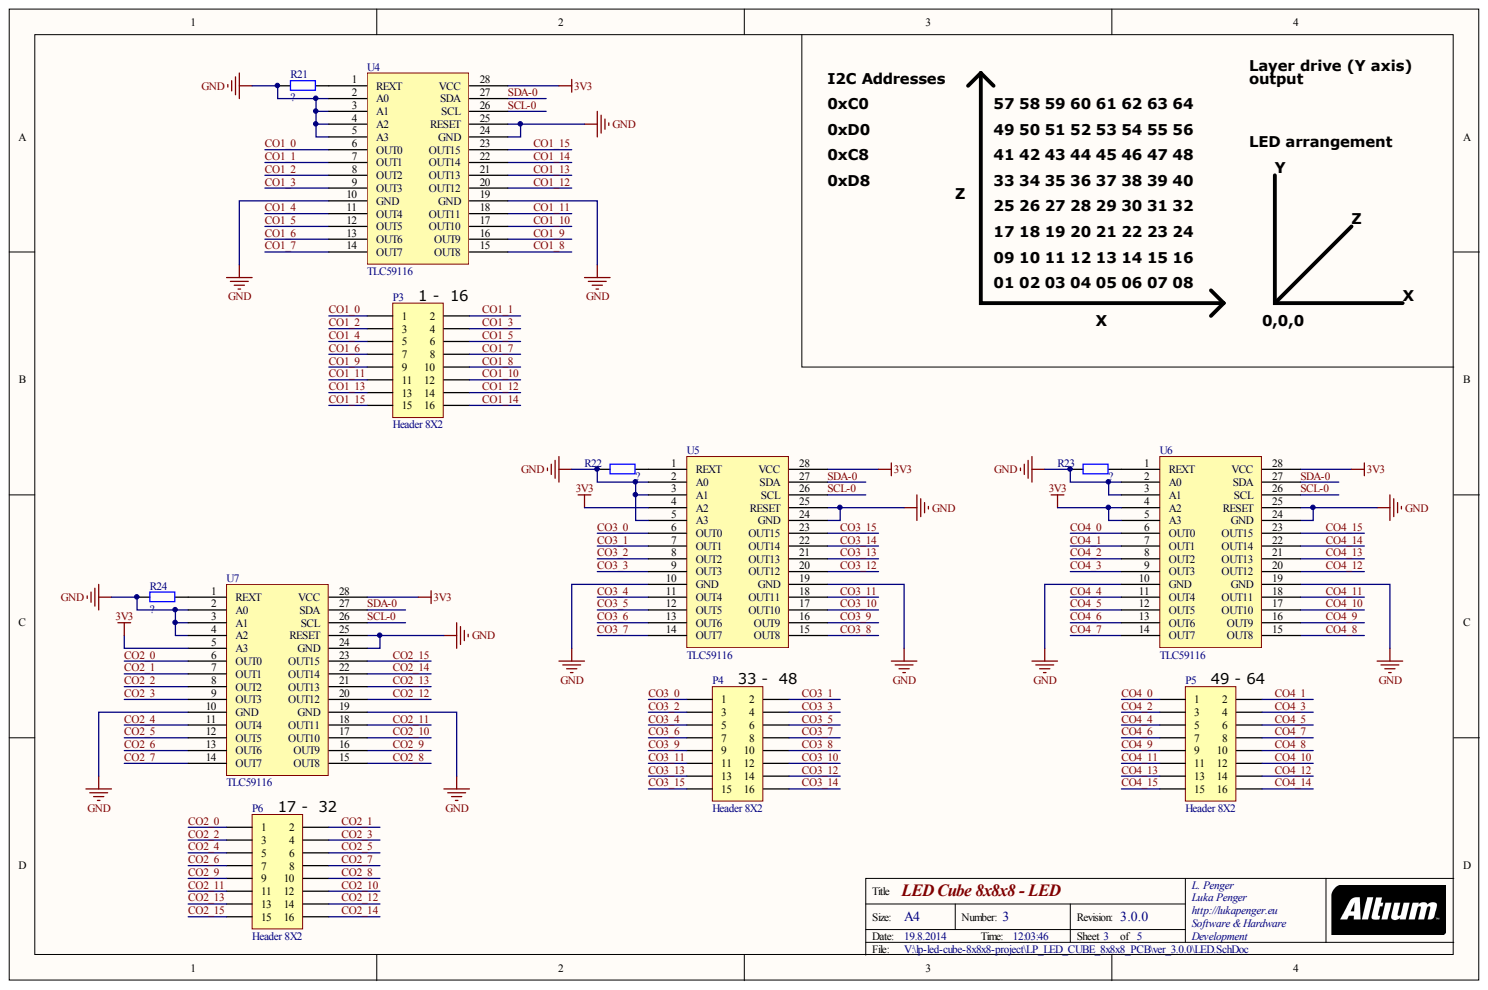
[picture p65: page 3]

Layer drive (Y axis) output

LED Cube 8x8x8 - LED
Title
V:\lp-led-cube-8x8x8-project\LP_LED_CUBE_8x8x8_PCB\ver_3.0.0\LED.SchDoc
File:

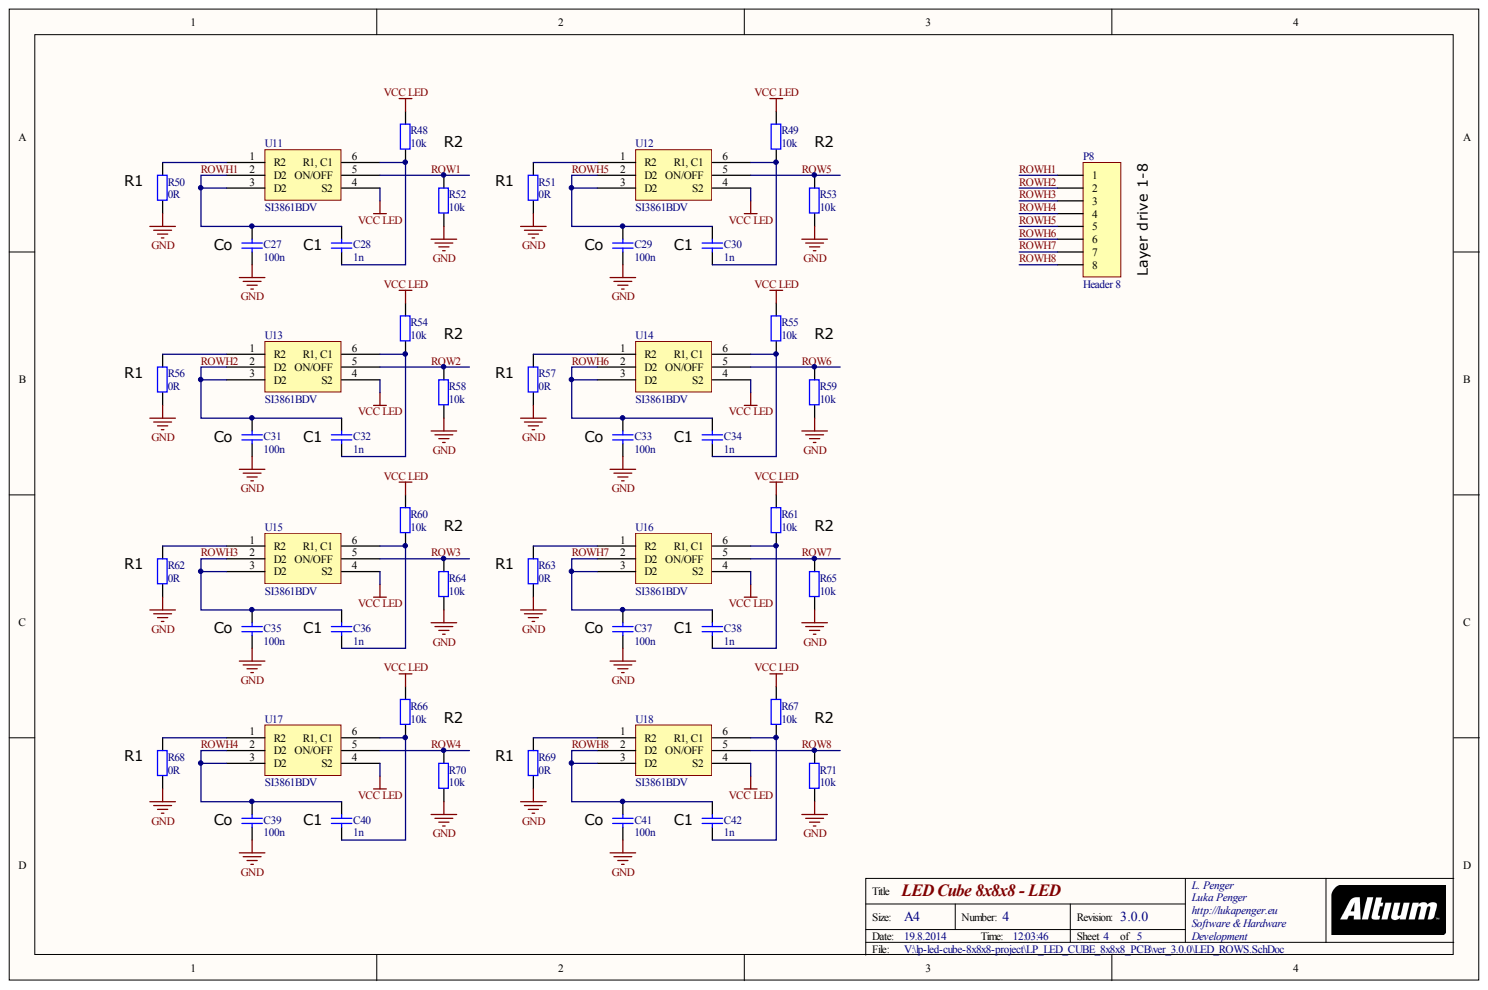
[picture p66: page 4]

: A4 | Numb er : 4 | Re vis io n: 3.0.0
Date : 1 9 . 8 . 2 0 1 4 Time : 1 2 : 0 3 :4 6 F ile : V :\lp -le d -cub e -8 x8 x8 -p roj e c t\LP _LED_C | S he e t 4 o f 5 UBE_ 8 x8 x8 _P C B\ver_3 | . 0 . 0 \LED_RO W S . S c hDo c

LED Cub e 8x8x8 -LED | L L . u Penge k a P enge r r h t tp : //lu k ap enge r. e u Soft w a re & Ha rdw a re De v e lop m e n t

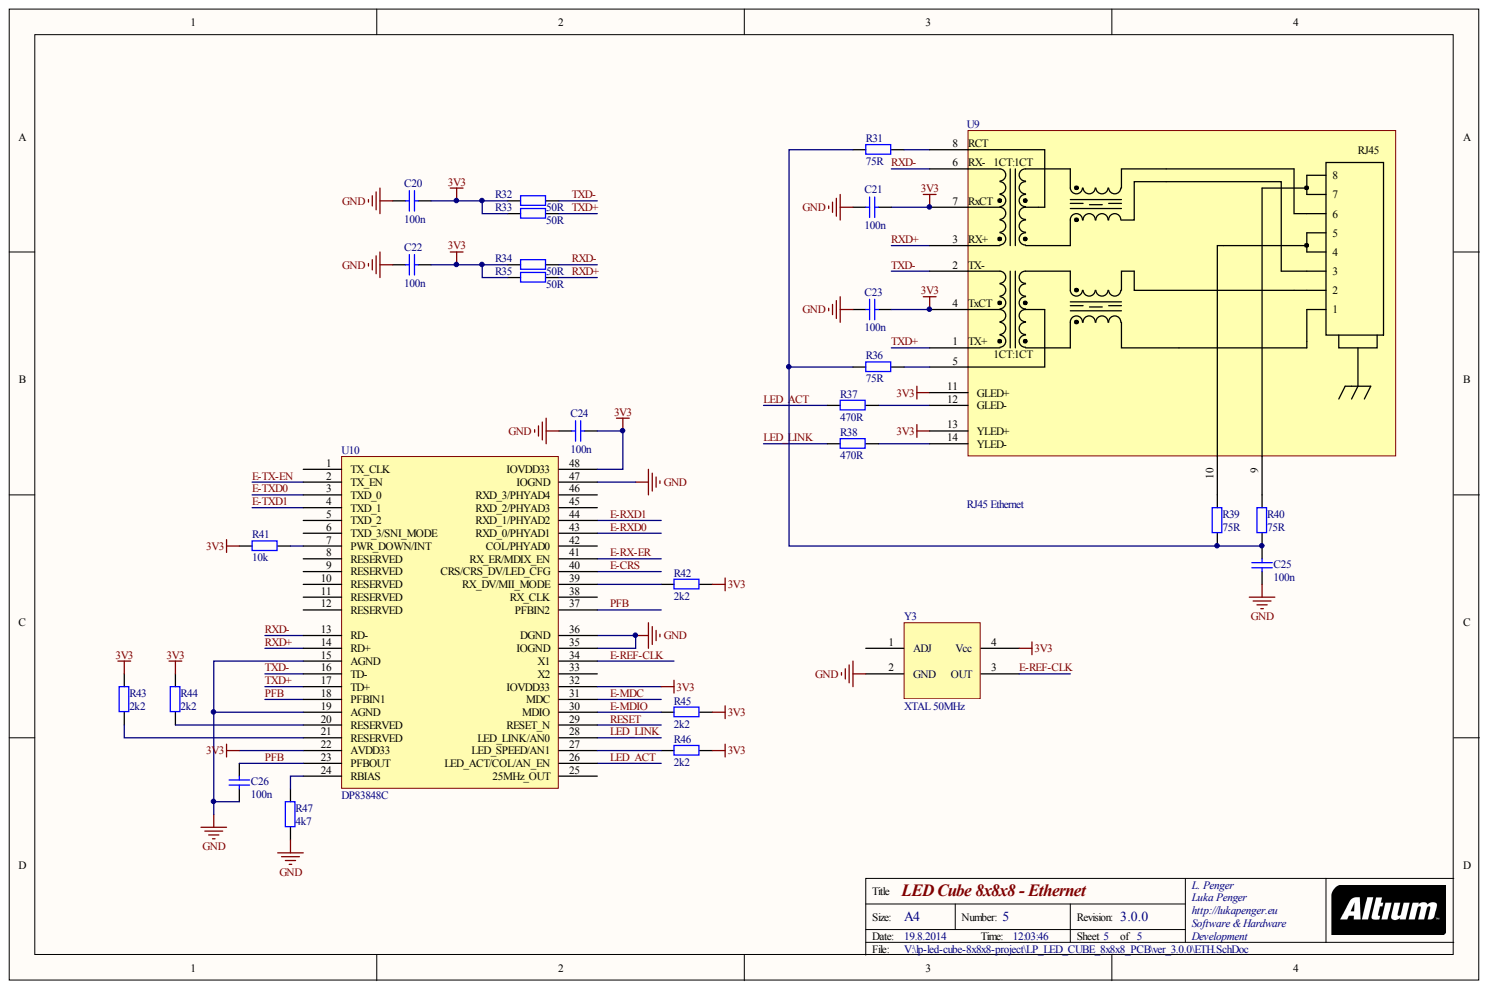
[picture p67: page 5]

75R RXD-6 3V3 C21 7 100n C23 100n R36 | 1CT:1CT RxCT | 8 7 6 5 4 3 2 1

RESERVED 20 | E-MDIO RESET

RESERVED 21 AVDD33 22 PFBOUT 23 | LED_LINK LED_ACT

Title LED Cube 8x8x8 - Ethernet | L. Penger Luka Penger http://lukapenger.eu Software & Hardware Development

Size: A4 | Number: 5 | Revision: 3.0.0

1 2 | Date: 19.8.2014 Time: 12:03:46 Sheet 5 of 5 File: V:\lp-led-cube-8x8x8-project\LP_LED_CUBE_8x8x8_PCB\ver_3.0.0\ETH.SchDoc 3 4

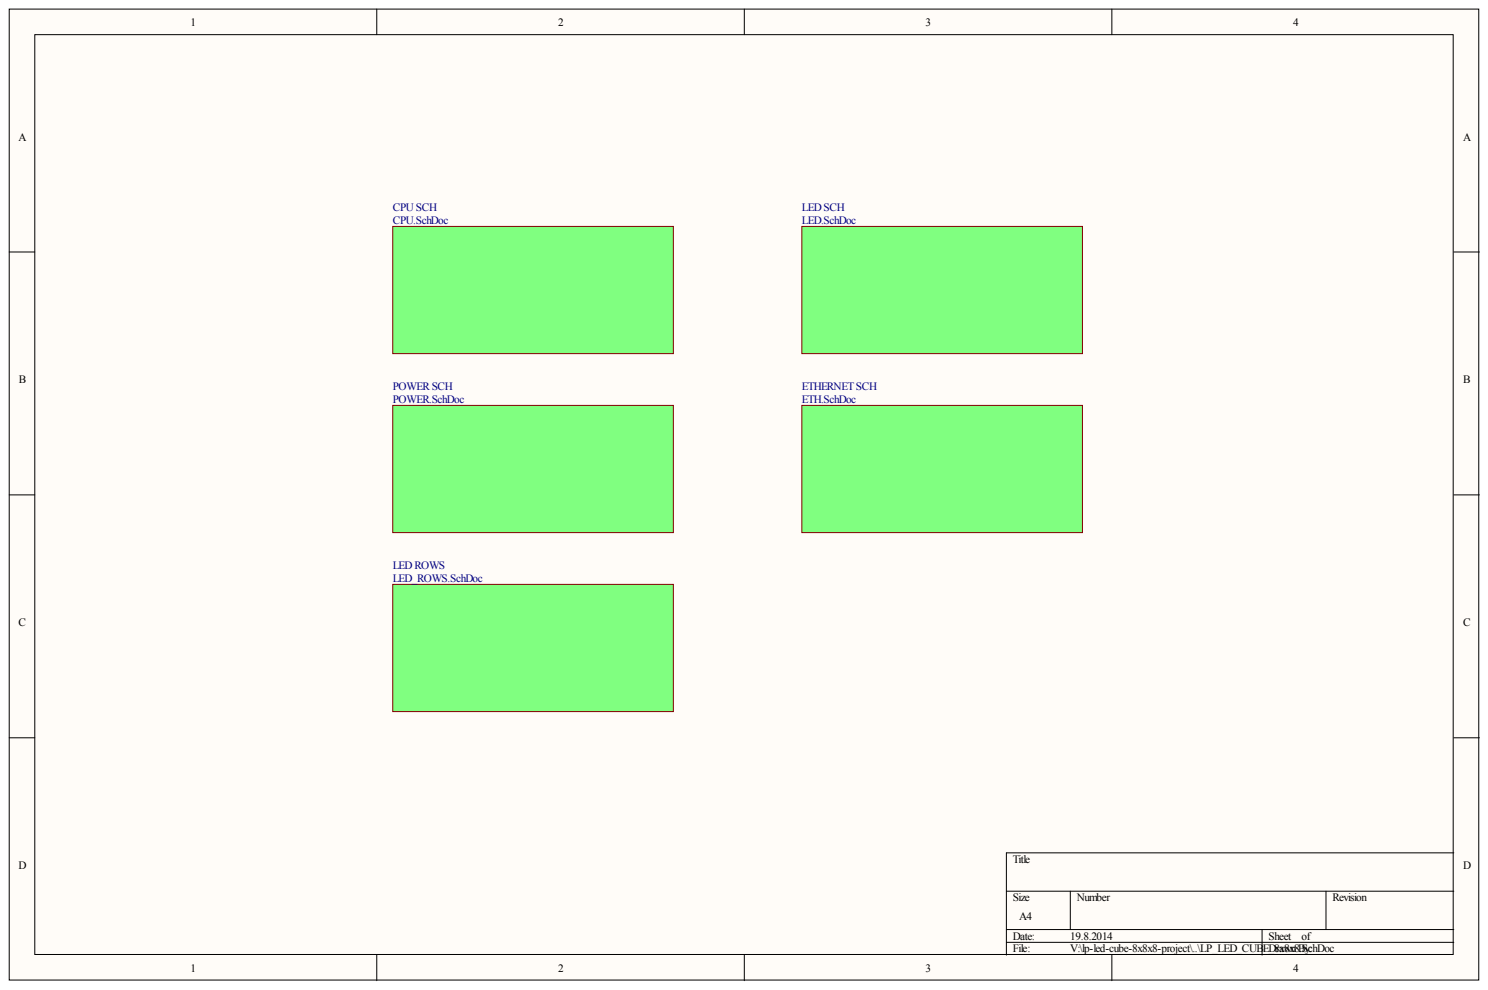
[picture p68: page 6]

Size A4 | Number | Revision

1 2 3 | Date: 19.8.2014 File: V:\lp-led-cube-8x8x8-project\..\LP_LED_CUBED_8raxw8xn8B.Syc:hDoc | Sheet of 4
