luka1995/LPProjects-LED-Cube-8x8x8/LP_LED_CUBE_8x8x8_PCB/ver_3.0.1/Project Outputs for LP_LED_CUBE_8x8x8/PDF/Schematic Mono.PDF

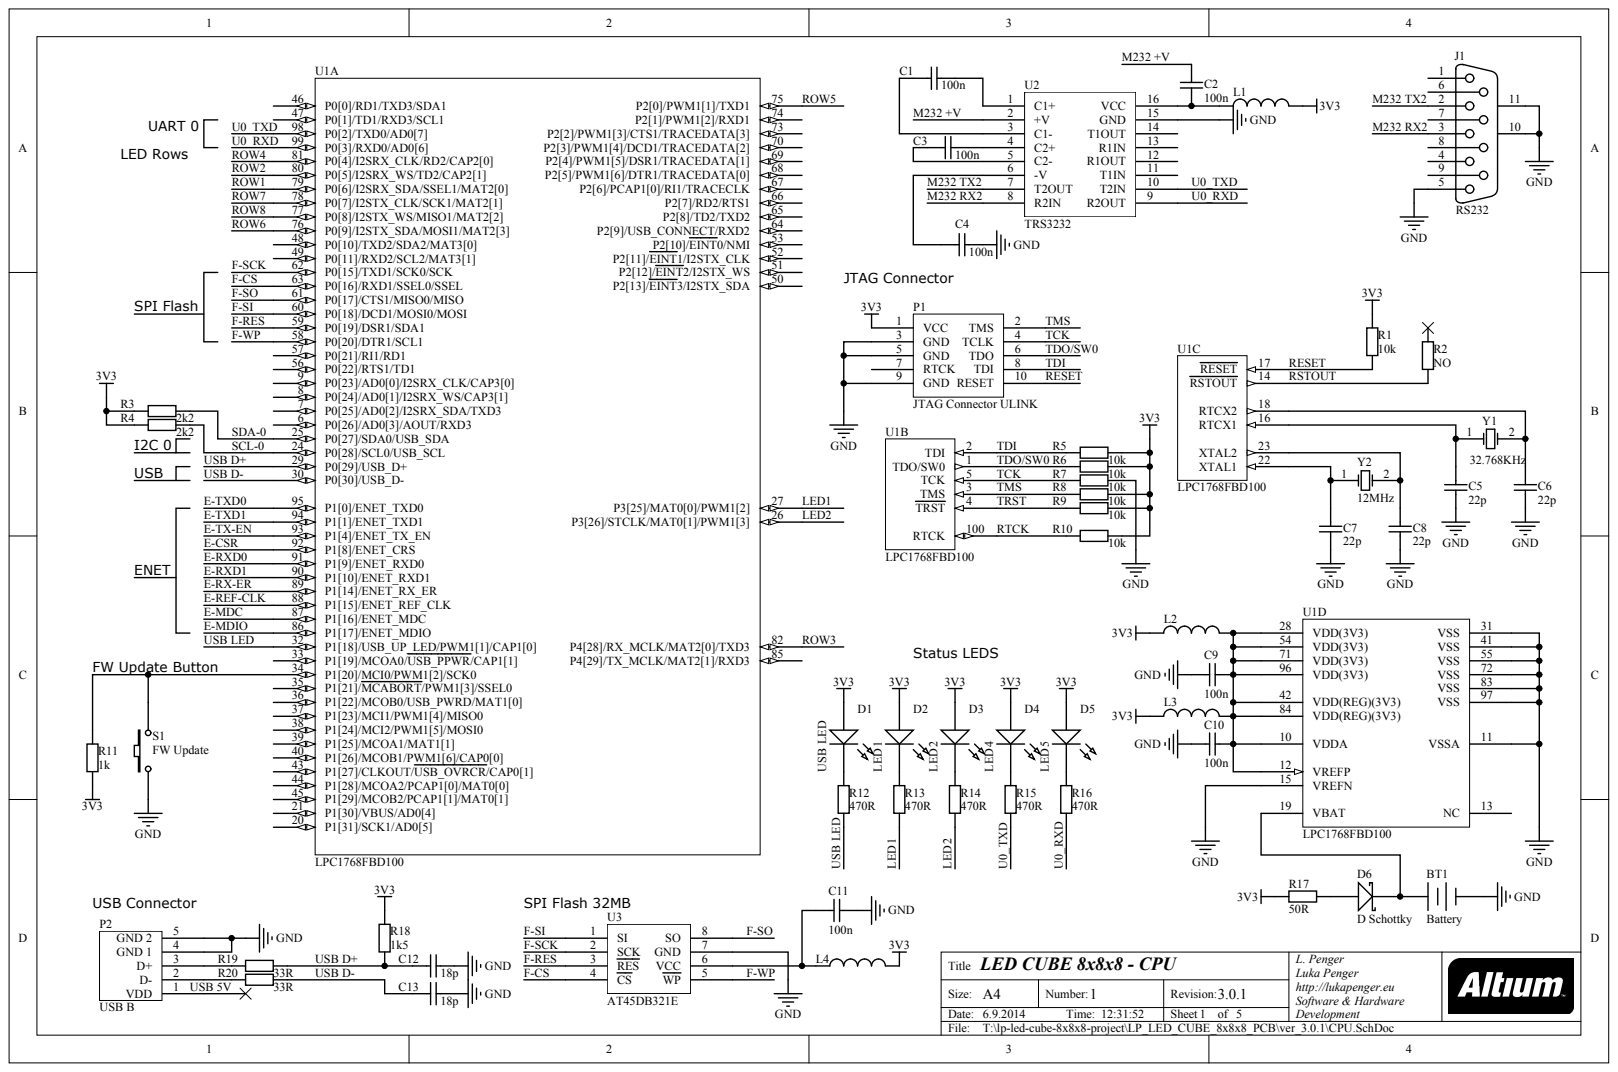
[picture p69: page 1]

T:\lp-led-cube-8x8x8-project\LP_LED_CUBE_8x8x8_PCB\ver_3.0.1\CPU.SchDoc

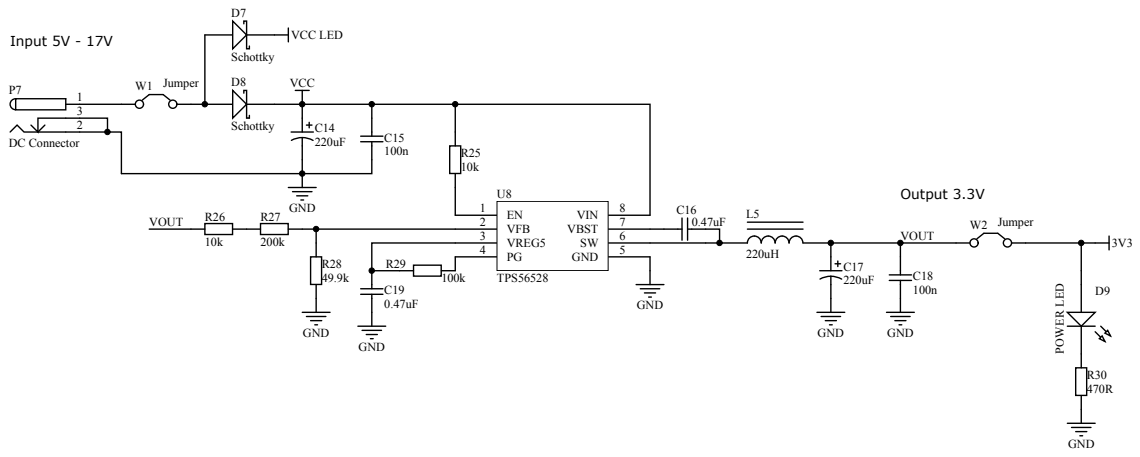
[picture p70: page 2]

Title | L. Penger Luka Penger http://lukapenger.eu Software & Hardware

A 4 Size: | Number: | Revision:

Date : Tim e : | | Sheet of

T:\lp-led-cube-8x8x8-project\LP_LED_CUBE_8x8x8_PCB\ver_3.0.1\POWER.SchDo

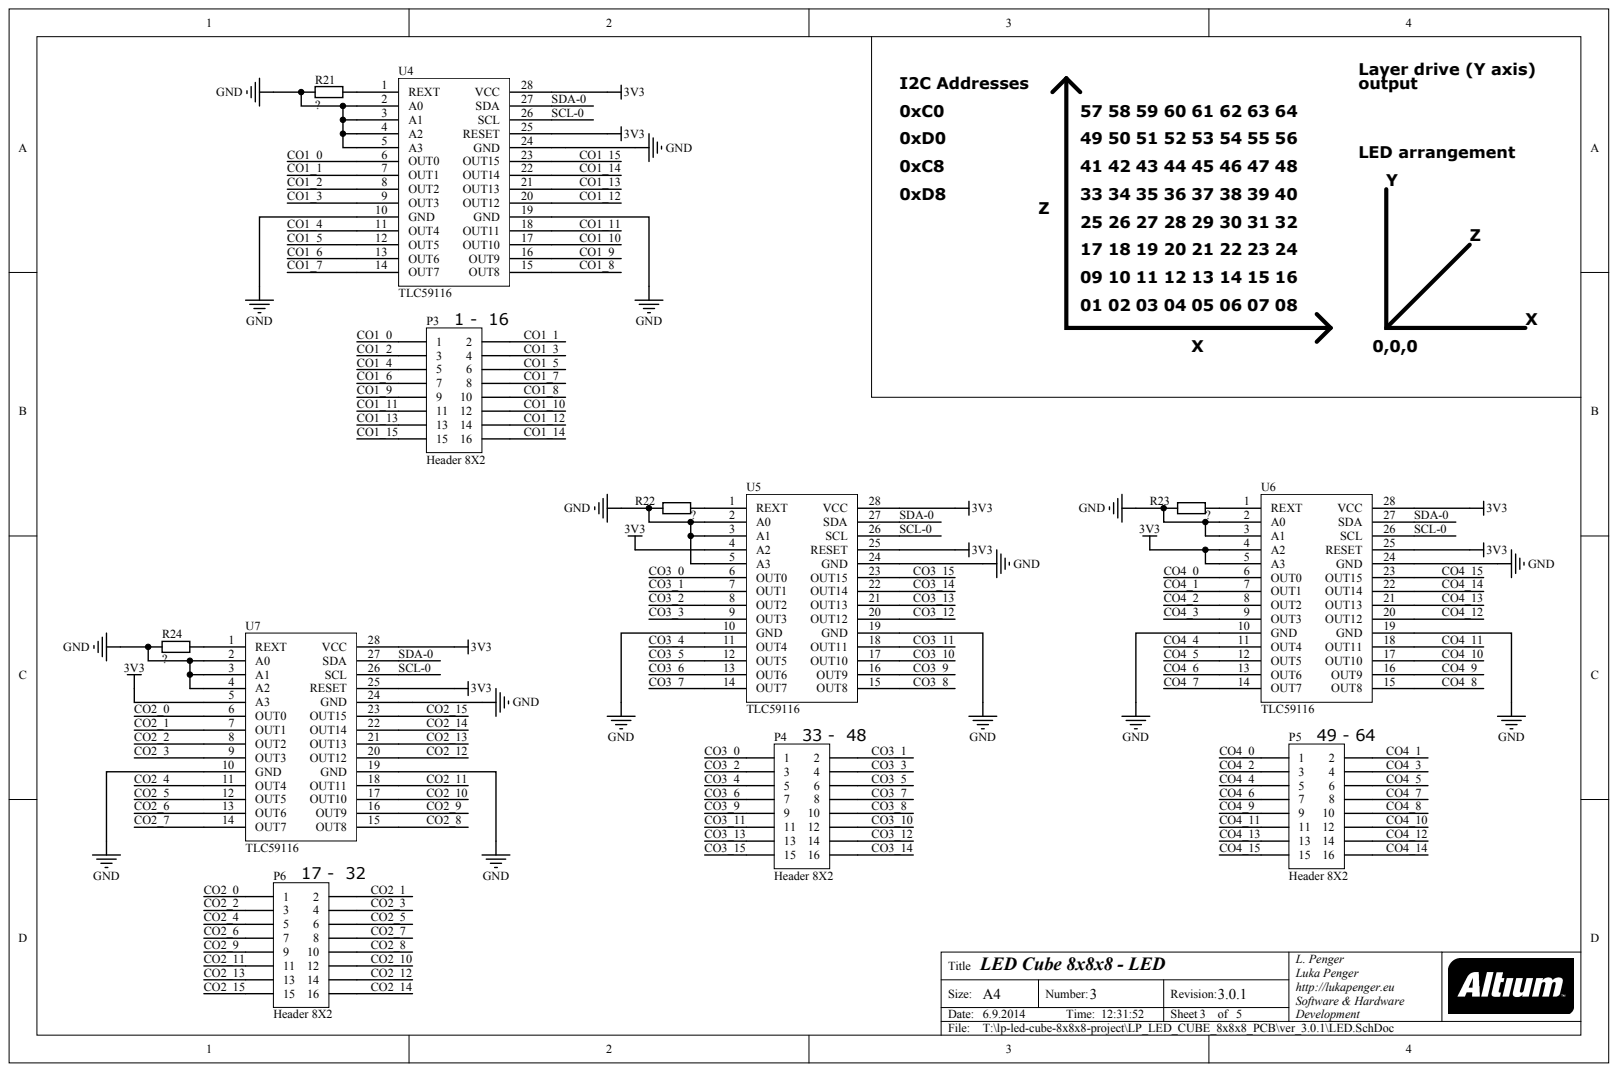
[picture p71: page 3]

A0 2
A1 3 | SCL-0
A2 4

OUT0 6 OUT1 7 OUT2 8 OUT3 9 GND 10 | CO1_15

A3 5
OUT0 6 | CO2_15

T:\lp-led-cube-8x8x8-project\LP_LED_CUBE_8x8x8_PCB\ver_3.0.1\LED.SchDoc

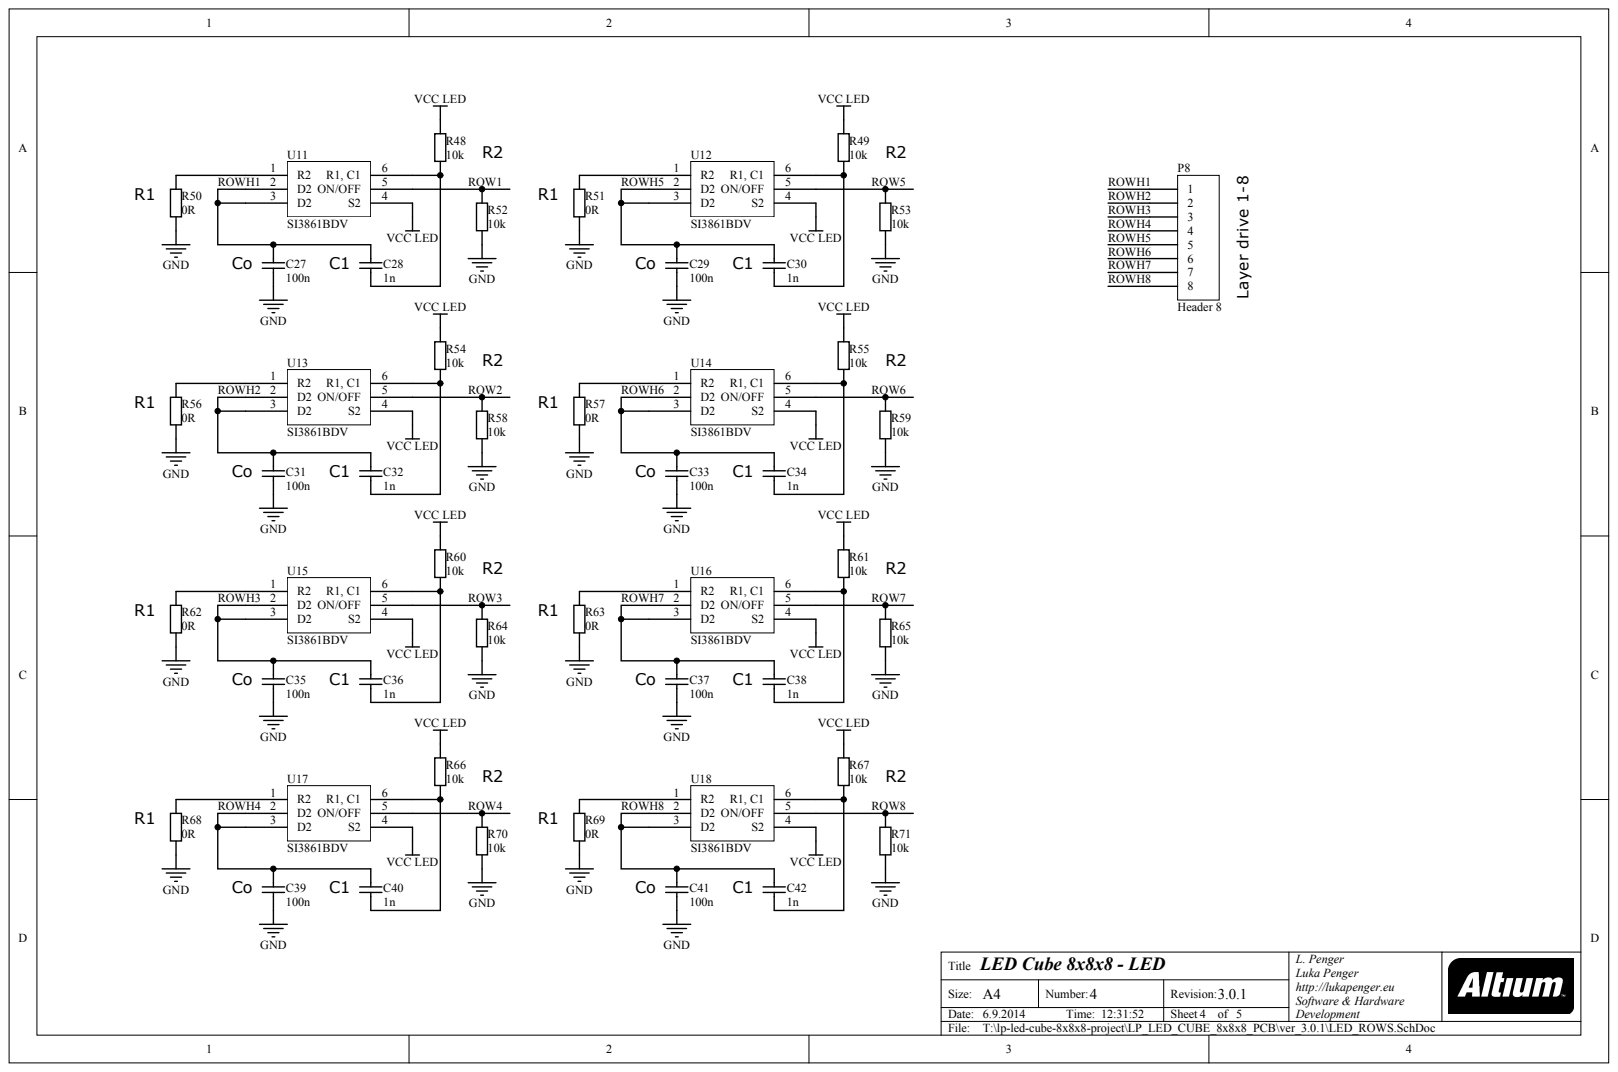
[picture p72: page 4]

Title | L. Penger Luka Penger http://lukapenger.eu Software & Hardware

A 4 Size: | Number: | Revision:

T:\lp-led-cube-8x8x8-project\LP_LED_CUBE_8x8x8_PCB\ver_3.0.1\LED_ROWS.SchDo

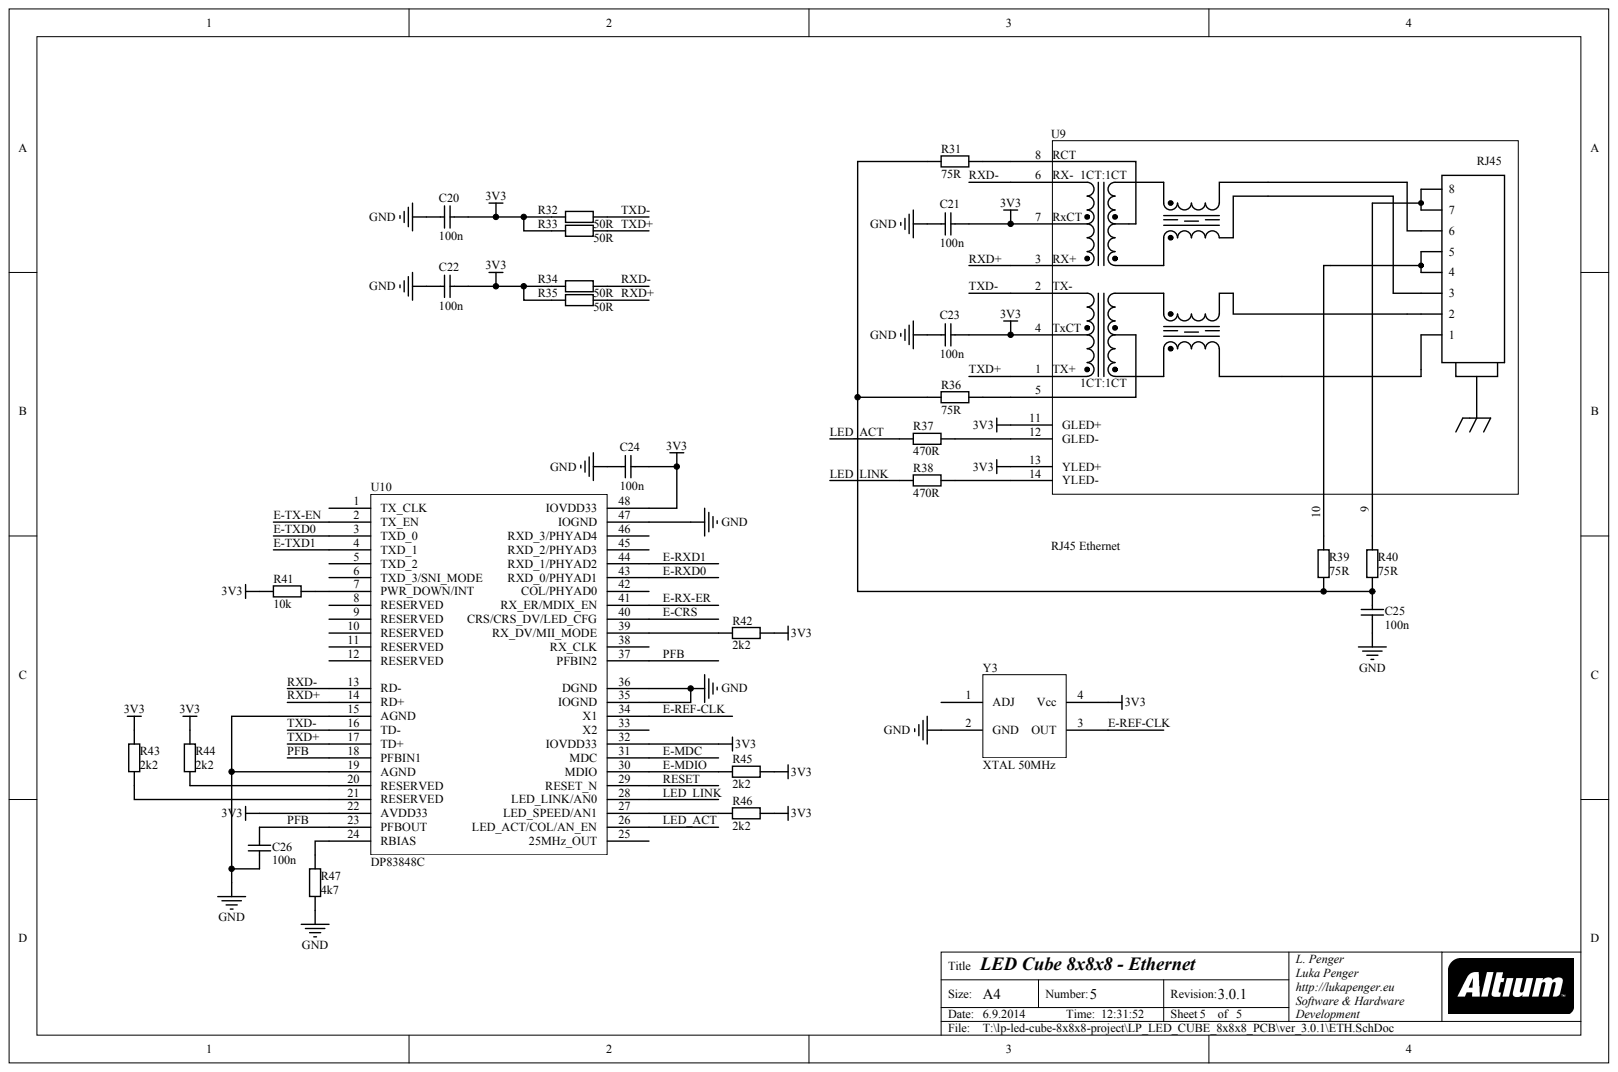
[picture p73: page 5]

E-REF-CLK

TXD-TXD+ PFB | TD- 16 TD+ 17 PFBIN1 18 AGND 19

RESERVED 20

AVDD33 22

Title | L. Penger Luka Penger http://lukapenger.eu Software & Hardware

A 4 Size: | Number: | Revision:

T:\lp-led-cube-8x8x8-project\LP_LED_CUBE_8x8x8_PCB\ver_3.0.1\ETH.SchDoc

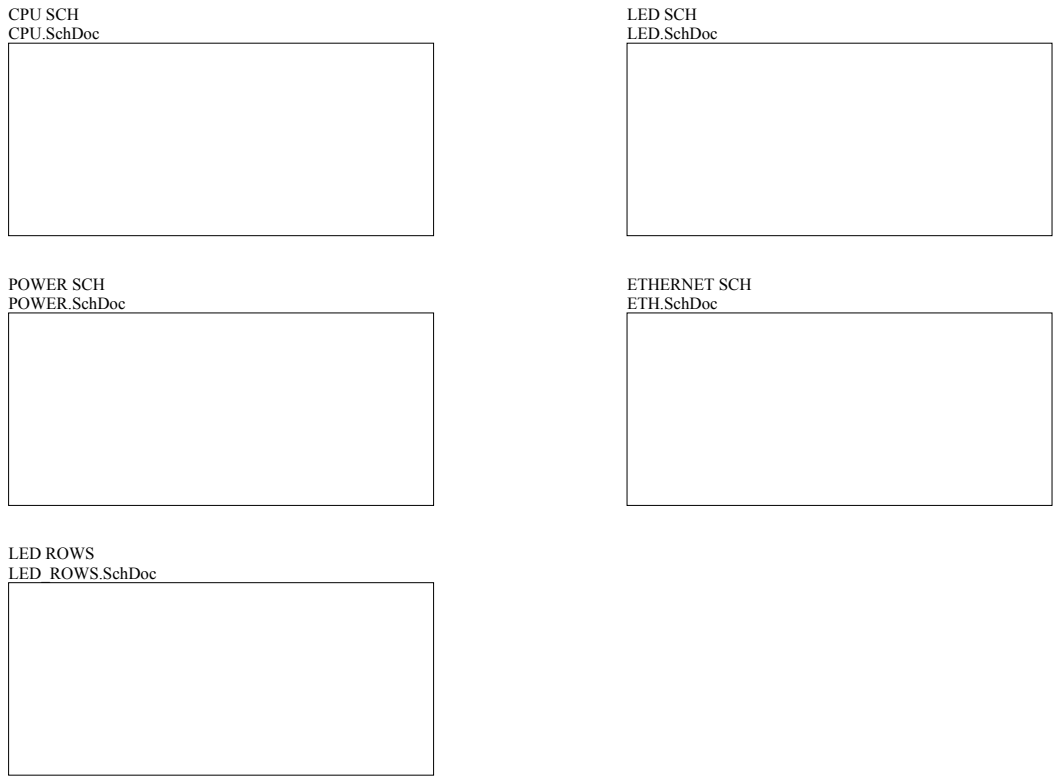
[picture p74: page 6]
