luka1995/LPProjects-LED-Cube-8x8x8/LP_LED_CUBE_8x8x8_PCB/ver_4.0.0/PCB_Board/Project Outputs for LP_LED_CUBE_8x8x8/PDF/Schematic.PDF

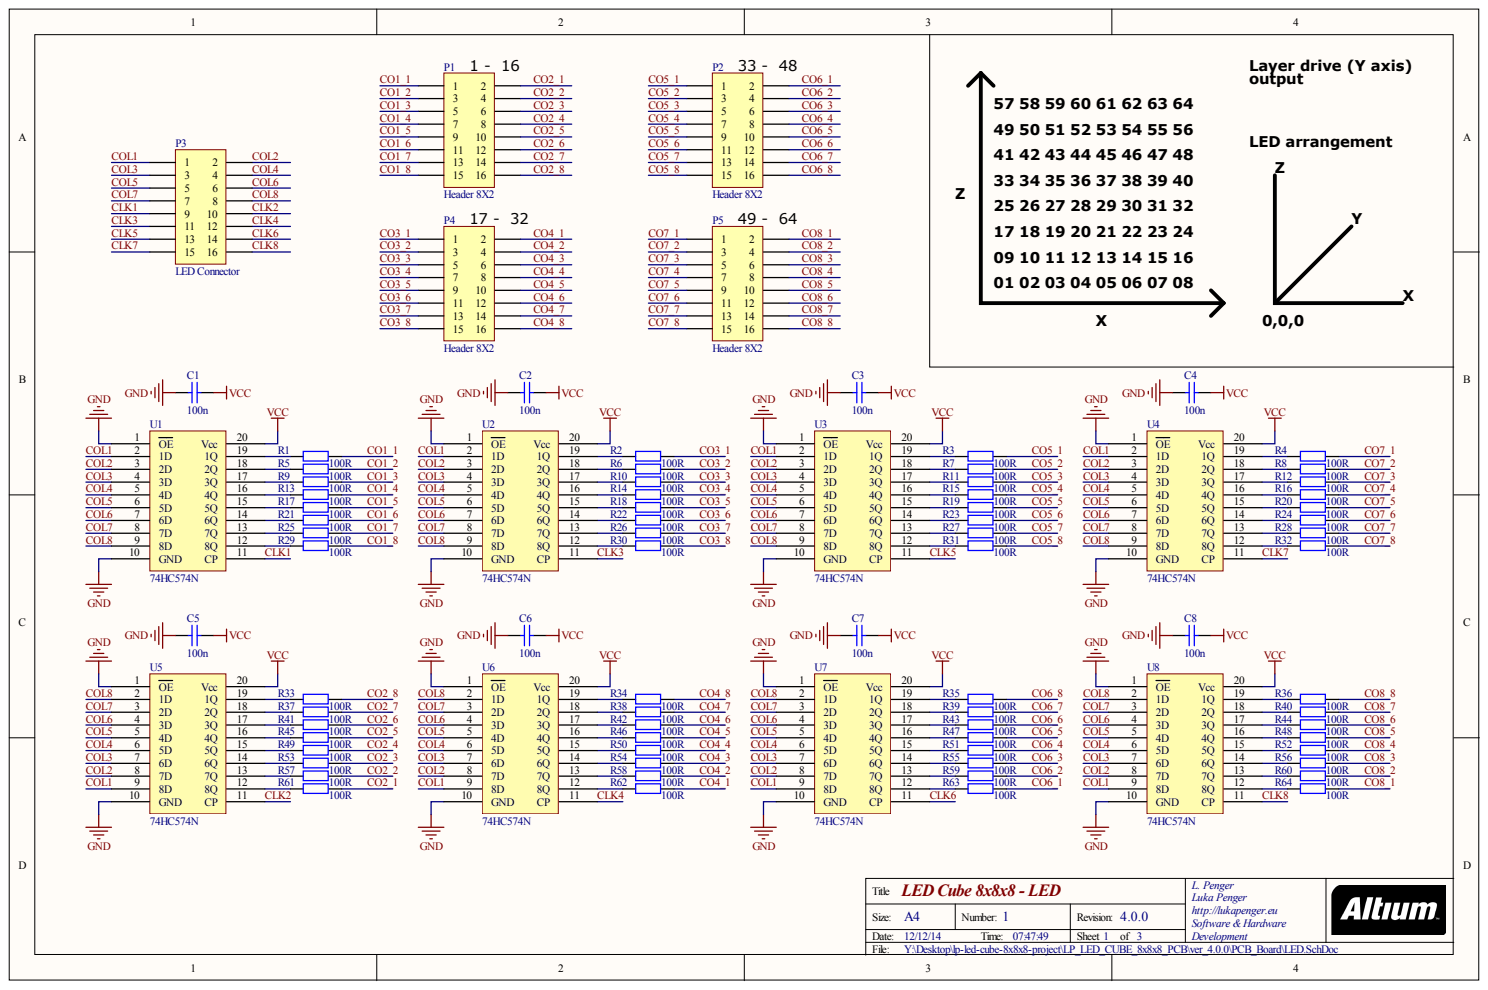
[picture p85: page 1]

Title LED Cube 8x8x8 - LED | L. Penger Luka Penger http://lukapenger.eu Software & Hardware Development

Size: A4 | Number: 1 | Revision: 4.0.0

1 2 | Date: 12/12/14 Time: 07:47:49 Sheet 1 of 3 File: Y:\Desktop\lp-led-cube-8x8x8-project\LP_LED_CUBE_8x8x8_PCB\ver_4.0.0\PCB_Board\LED.SchDoc 3 4

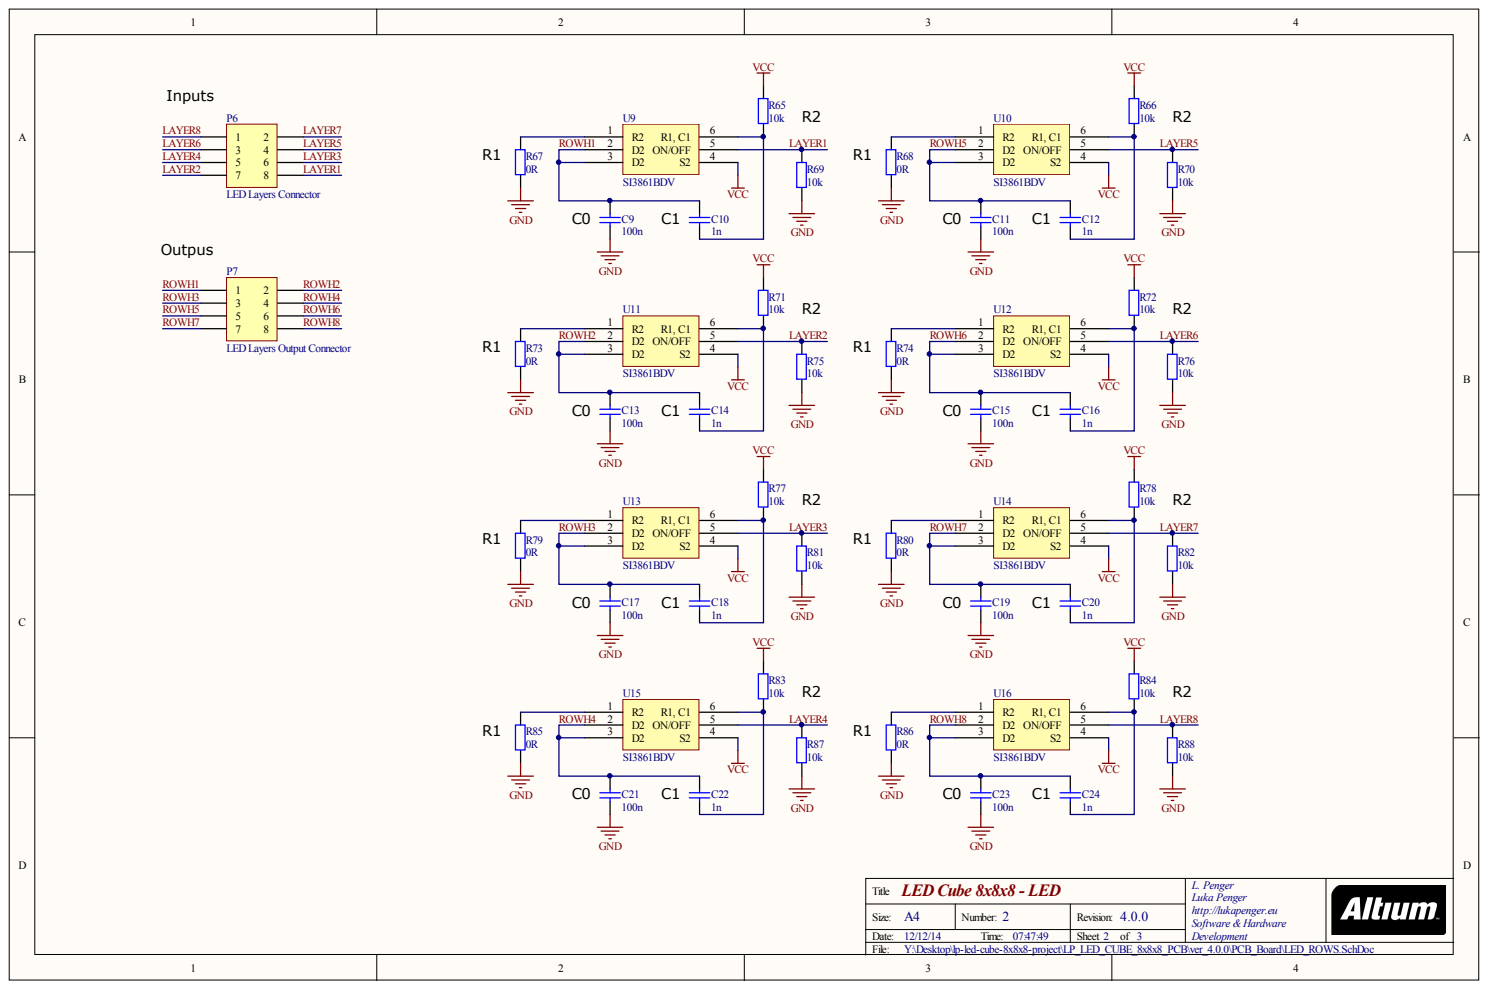
[picture p86: page 2]

: A4 | Numb er : 2 | Re vis io n: 4.0.0
Date : 1 2 / 1 2 / 1 4 Time : 0 7 :4 7 :4 9 F ile : Y :\D e s ktop \lp -le d -cub e -8 x8 x8 -p roj e c t\LP | S he e t 2 o f 3 _LED_C UBE_ 8 x8 x8 _P C | B\ver_4 . 0 . 0 \P C B_B o ard\LED_RO | W S . S c hDo c

LED Cub e 8x8x8 -LED | L L . u Penge k a P enge r r h t tp : //lu k ap enge r. e u Soft w a re & Ha rdw a re De v e lop m e n t

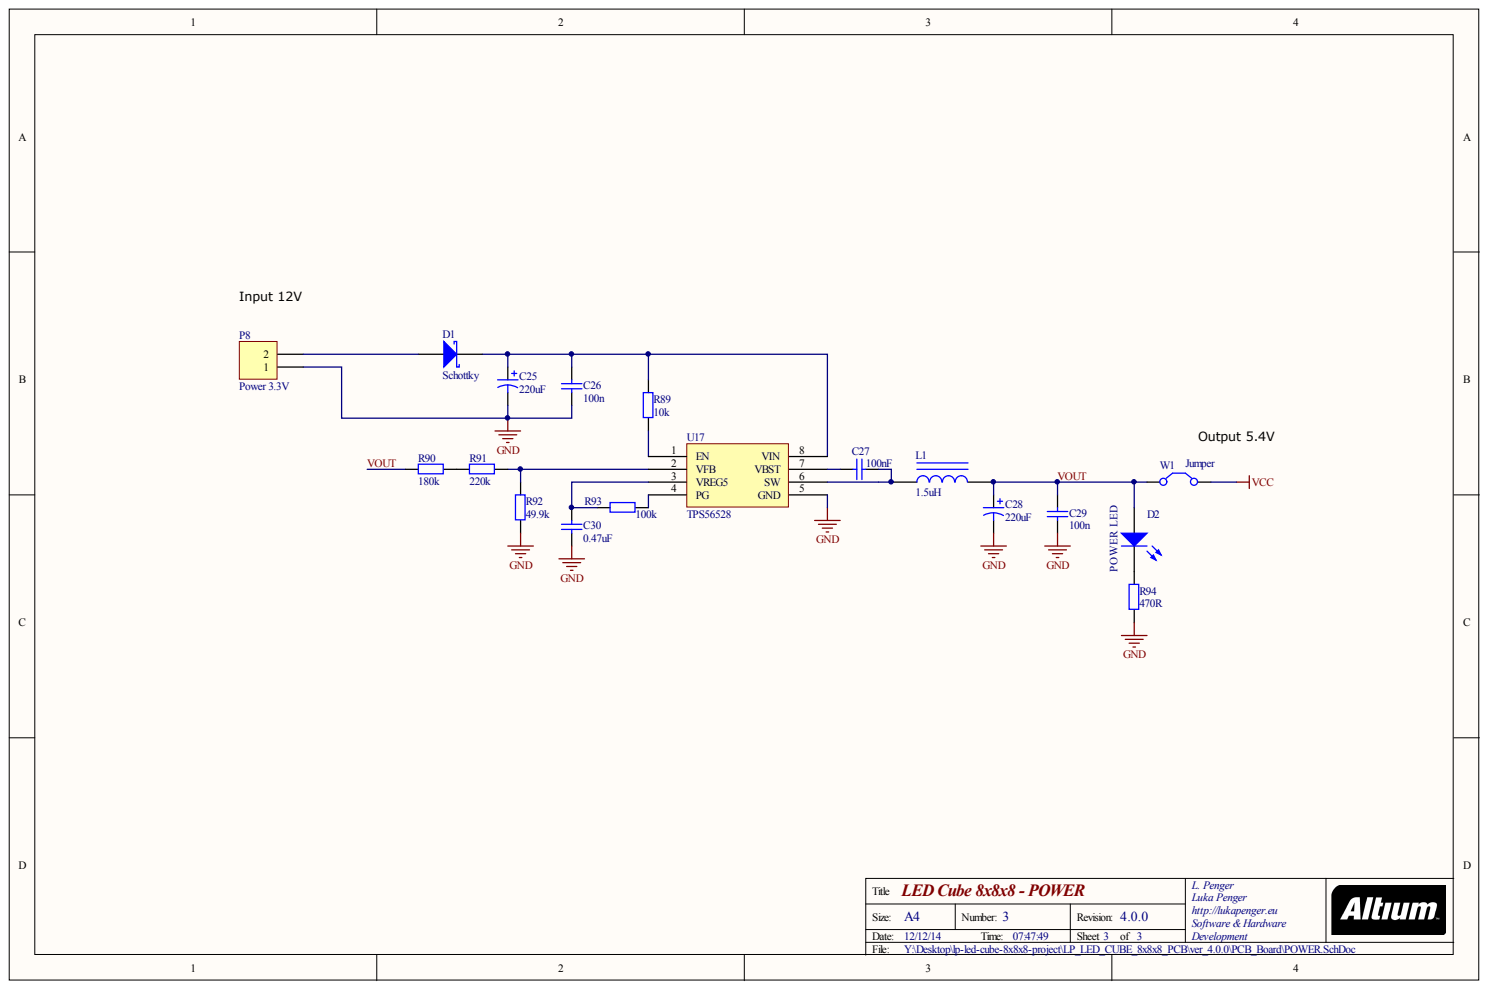
[picture p87: page 3]

: A4 | Numb er : 3 | Re vis io n: 4.0.0
Date : 1 2 / 1 2 / 1 4 Time : 0 7 :4 7 :4 9 F ile : Y :\D e s ktop \lp -le d -cub e -8 x8 x8 -p roj e c t\LP | S he e t 3 o f 3 _LED_C UBE_ 8 x8 x8 _P C | B\ver_4 . 0 . 0 \P C B_B o ard\P O WER. | S c hDo c

LED Cub e 8x8x8 -PO WER | L L . u Penge k a P enge r r h t tp : //lu k ap enge r. e u Soft w a re & Ha rdw a re De v e lop m e n t

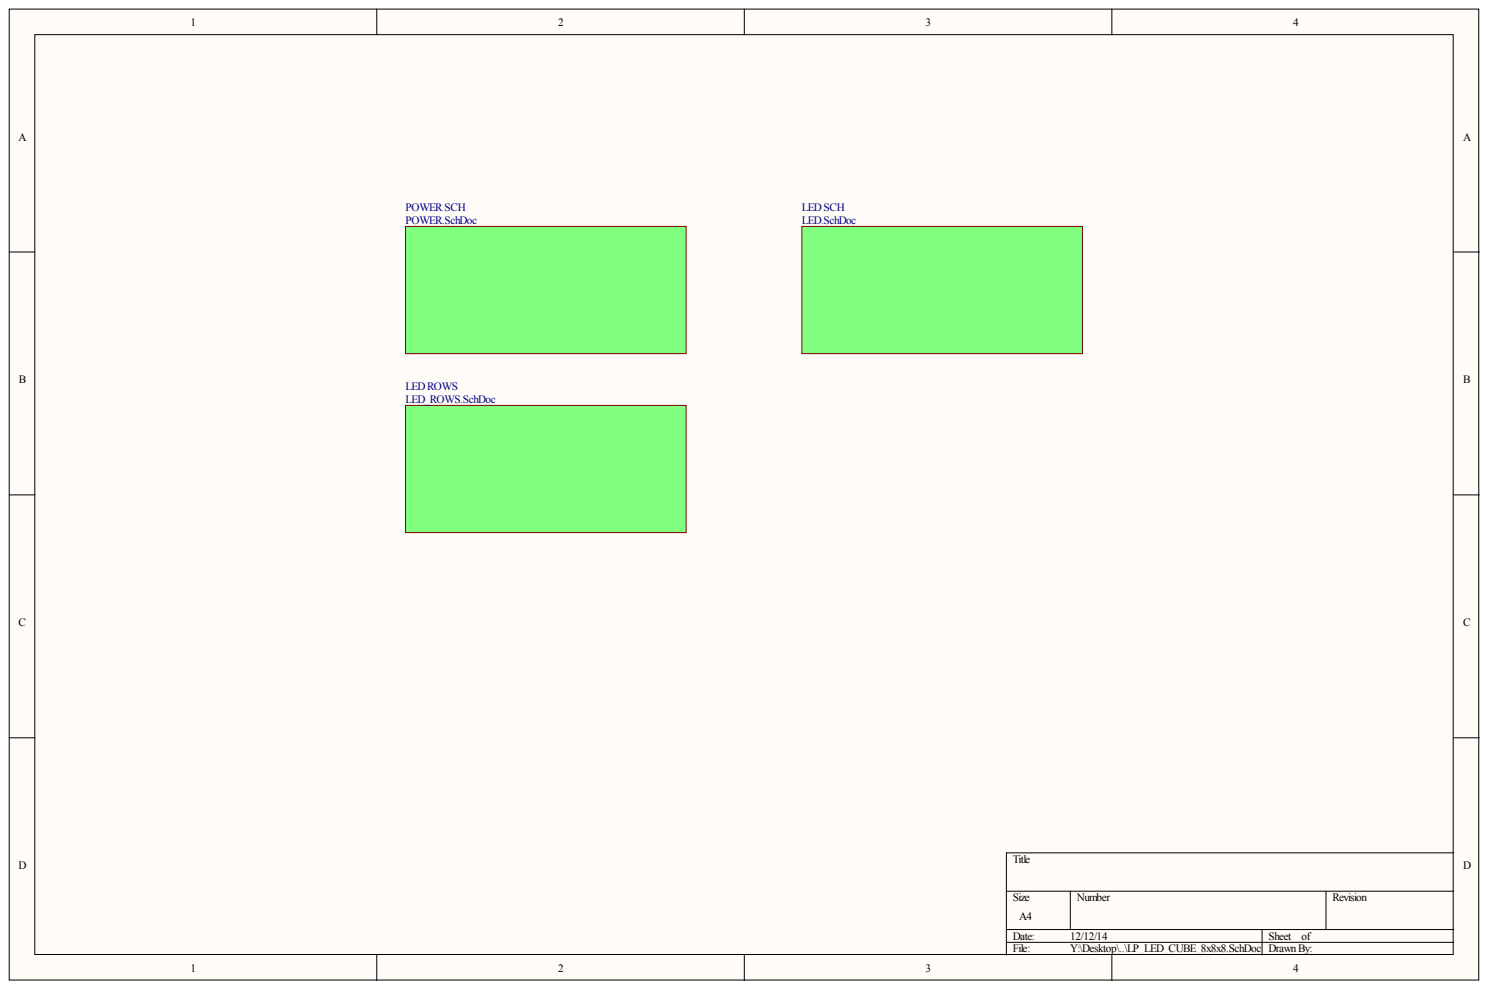
[picture p88: page 4]

Size A4 | Number | Revision

1 2 3 | Date: 12/12/14 File: Y:\Desktop\..\LP_LED_CUBE_8x8x8.SchDoc | Sheet of DrawnBy: 4
