luka1995/LPProjects-LED-Cube-8x8x8/LP_LED_CUBE_8x8x8_PCB/ver_4.0.0/PCB_Controller/Project Outputs for LP_LED_CUBE_8x8x8/PDF/Schematic Mono.PDF

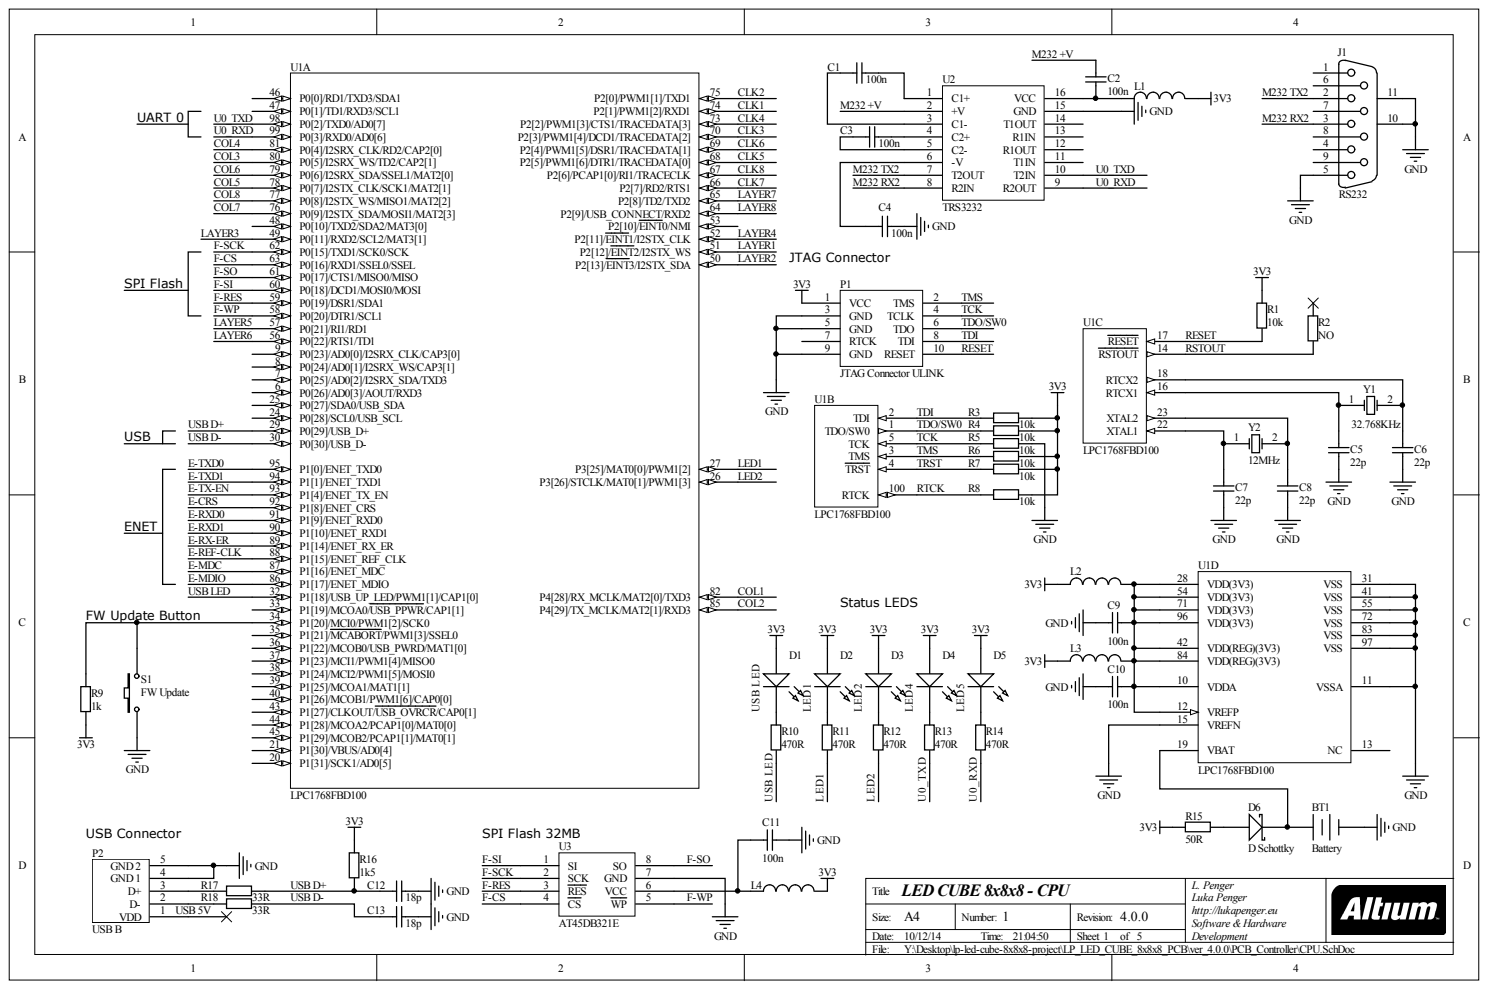
[picture p89: page 1]

LED CUBE 8x8x8 - CPU
Title
Date:
Y:\Desktop\lp-led-cube-8x8x8-project\LP_LED_CUBE_8x8x8_PCB\ver_4.0.0\PCB_Controller\CPU.SchDoc
File:

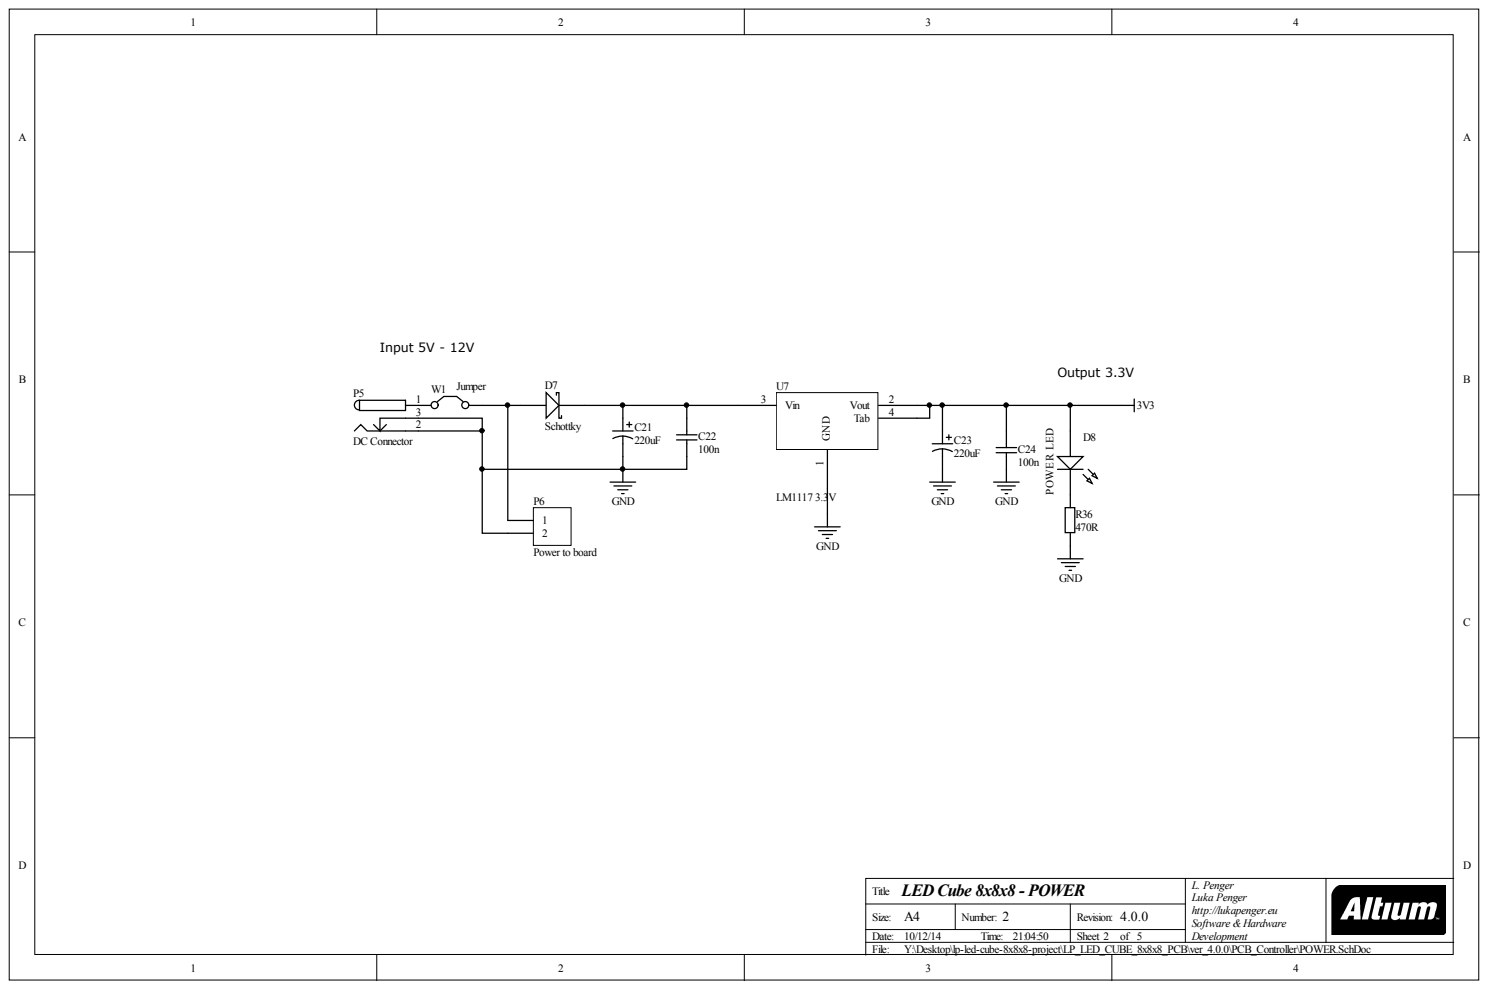
[picture p90: page 2]

: A4 | Numb er : 2 | Re vis io n: 4.0.0
Date : 1 0 / 1 2 / 1 4 Time : 2 1 : 0 4 : 5 0 F ile : Y :\D e s ktop \lp -le d -cub e -8 x8 x8 -p roj e c t\LP | S he e t 2 o f 5 _LED_C UBE_ 8 x8 x8 _P C | B\ver_4 . 0 . 0 \P C B_C o ntro ller\P O | WER. S c hDo c

LED Cub e 8x8x8 -PO WER | L L . u Penge k a P enge r r h t tp : //lu k ap enge r. e u Soft w a re & Ha rdw a re De v e lop m e n t

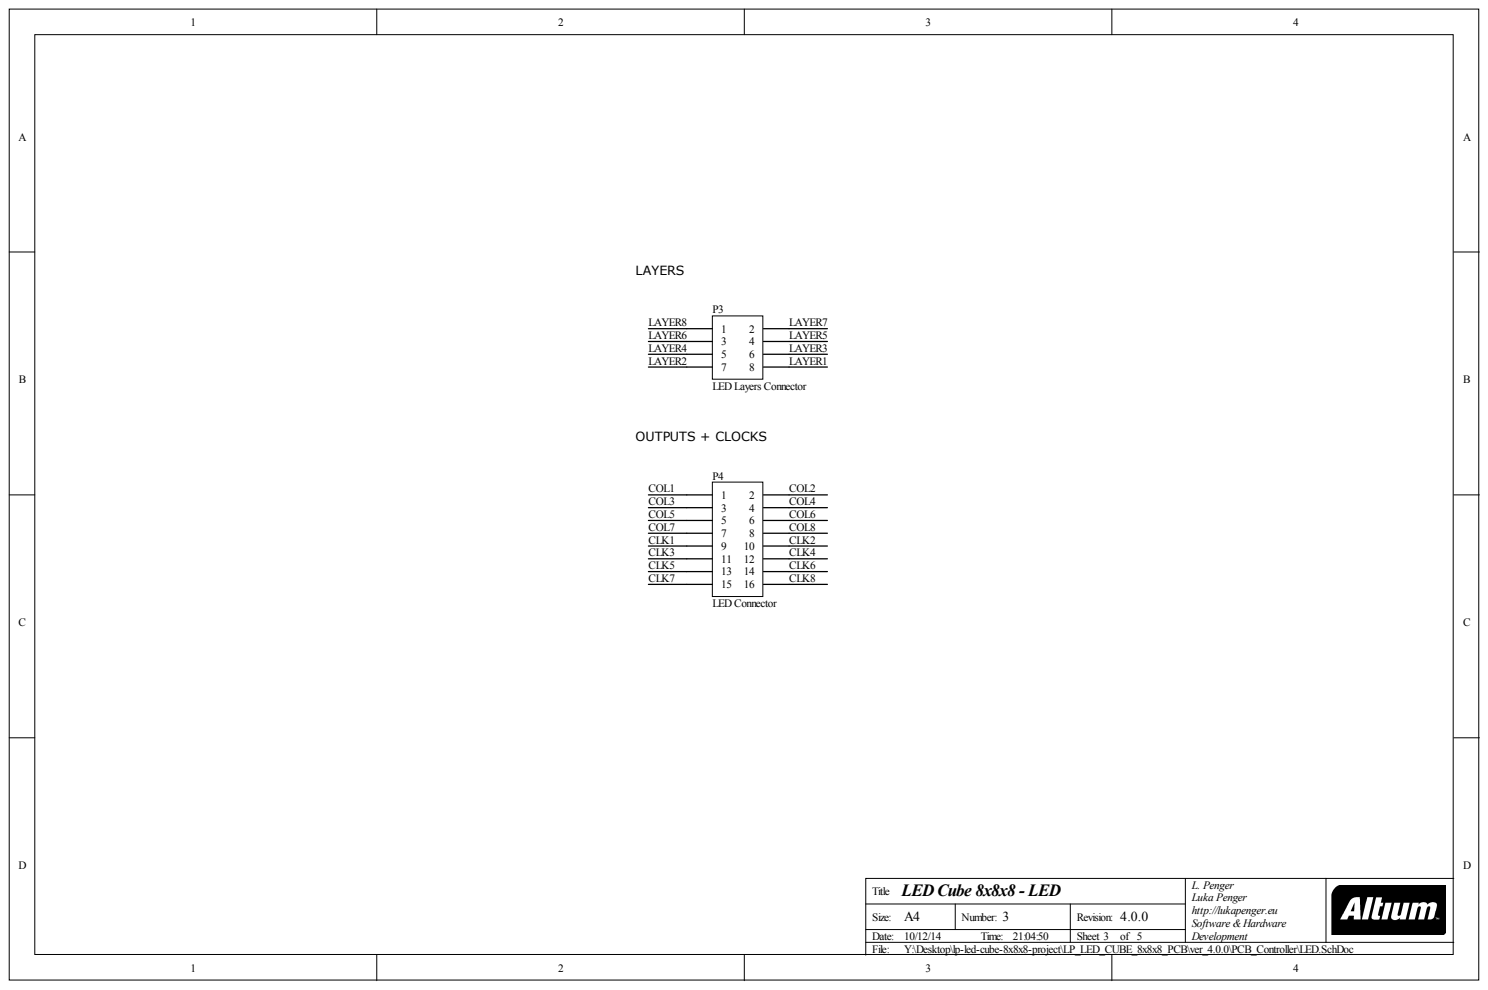
[picture p91: page 3]

Title LED Cube 8x8x8 - LED | L. Penger Luka Penger http://lukapenger.eu Software & Hardware Development

Size: A4 | Number: 3 | Revision: 4.0.0

1 2 | Date: 10/12/14 Time: 21:04:50 Sheet 3 of 5 File: Y:\Desktop\lp-led-cube-8x8x8-project\LP_LED_CUBE_8x8x8_PCB\ver_4.0.0\PCB_Controller\LED.SchDoc 3 4

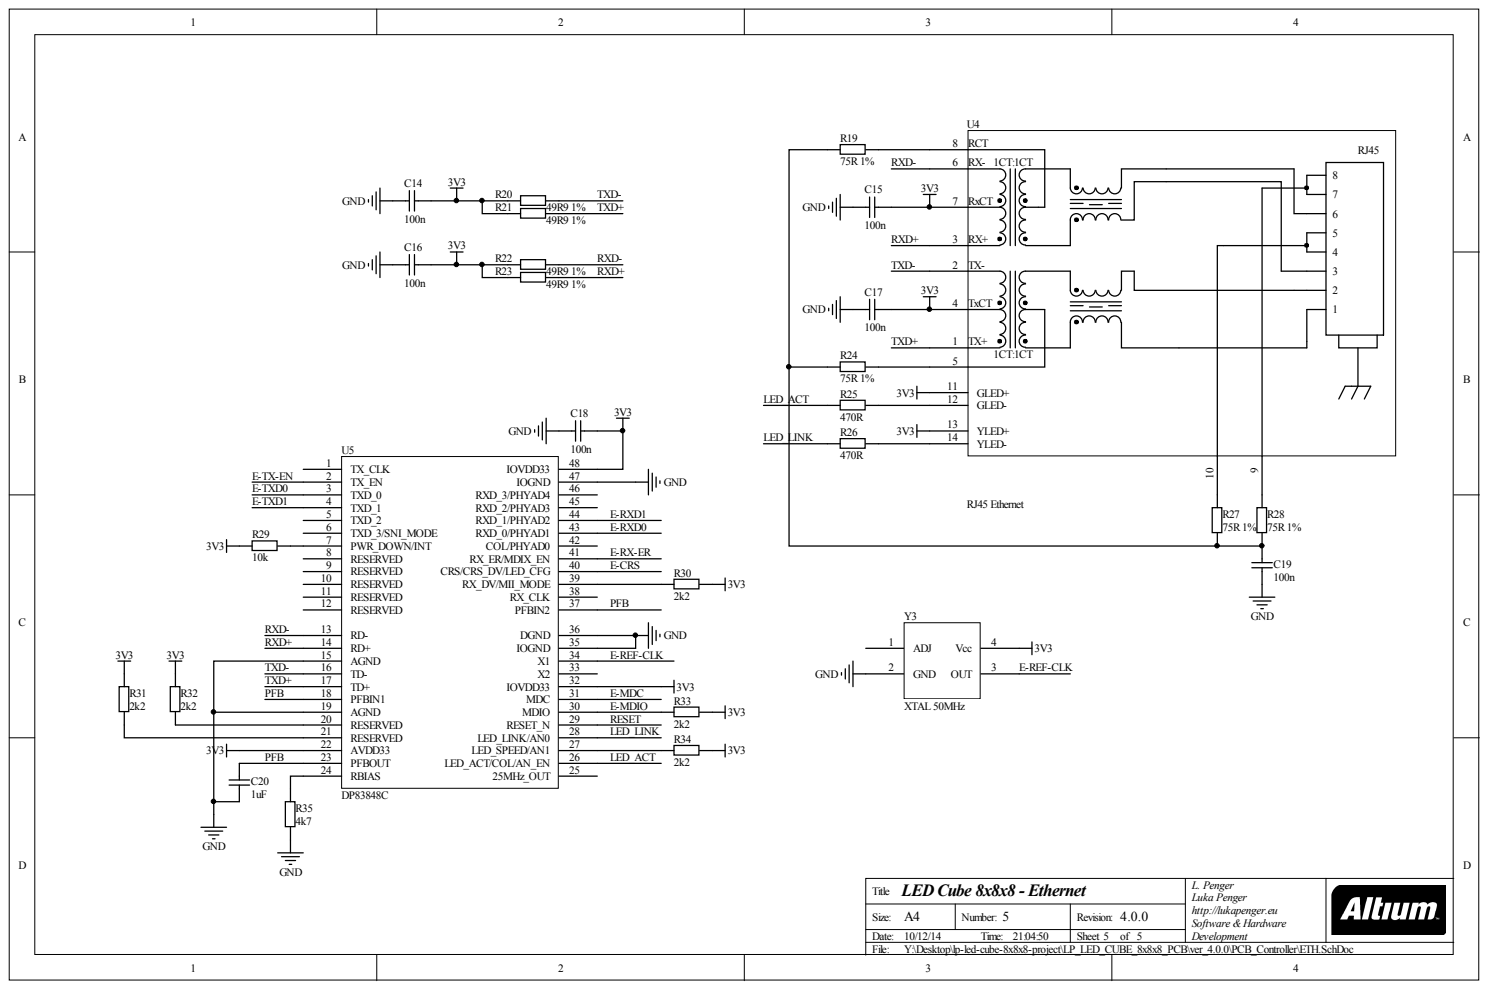
[picture p92: page 4]

GND | 75R1% RXD-6 100n 100n R24 | 1CT:1CT RxCT | 8 7 6 5 4 3 2 1

RESERVED 20 | E-MDIO RESET

RESERVED 21 AVDD33 22 PFBOUT 23 | LED_LINK LED_ACT

Title LED Cube 8x8x8 - Ethernet | L. Penger Luka Penger http://lukapenger.eu Software & Hardware Development

Size: A4 | Number: 5 | Revision: 4.0.0

1 2 | Date: 10/12/14 Time: 21:04:50 Sheet 5 of 5 File: Y:\Desktop\lp-led-cube-8x8x8-project\LP_LED_CUBE_8x8x8_PCB\ver_4.0.0\PCB_Controller\ETH.SchDoc 3 4

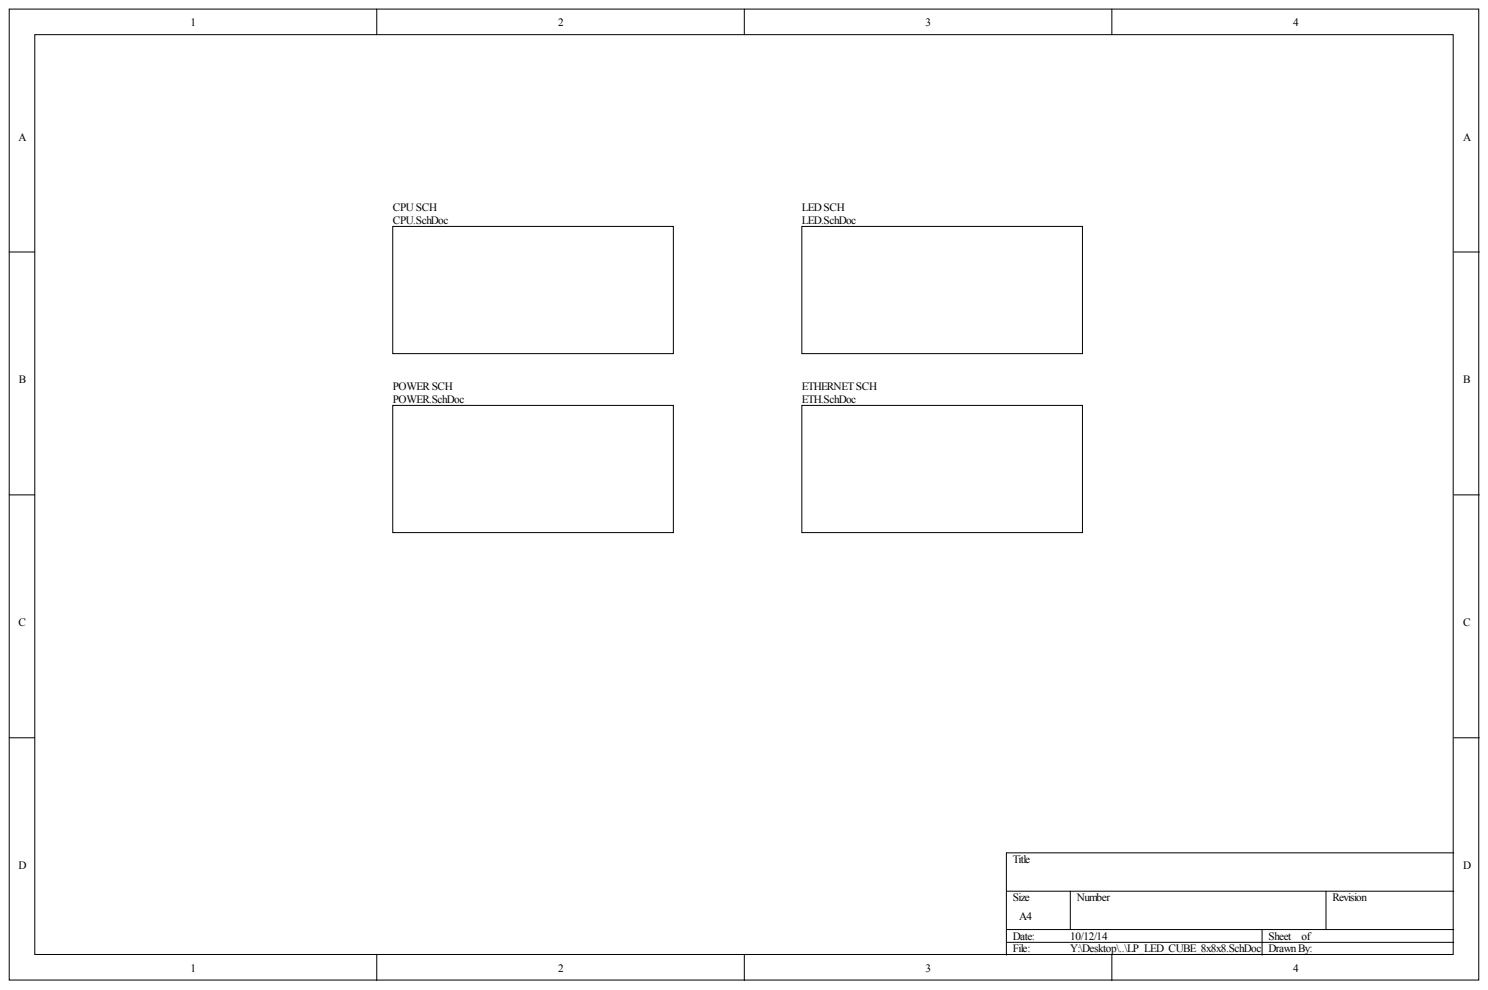
[picture p93: page 5]

Size A4 | Number | Revision

1 2 3 | Date: 10/12/14 File: Y:\Desktop\..\LP_LED_CUBE_8x8x8.SchDoc | Sheet of DrawnBy: 4
