luka1995/LPProjects-LED-Cube-8x8x8/PCB/Ver 1.0.0/PDF/BOTTOM Layer.PDF

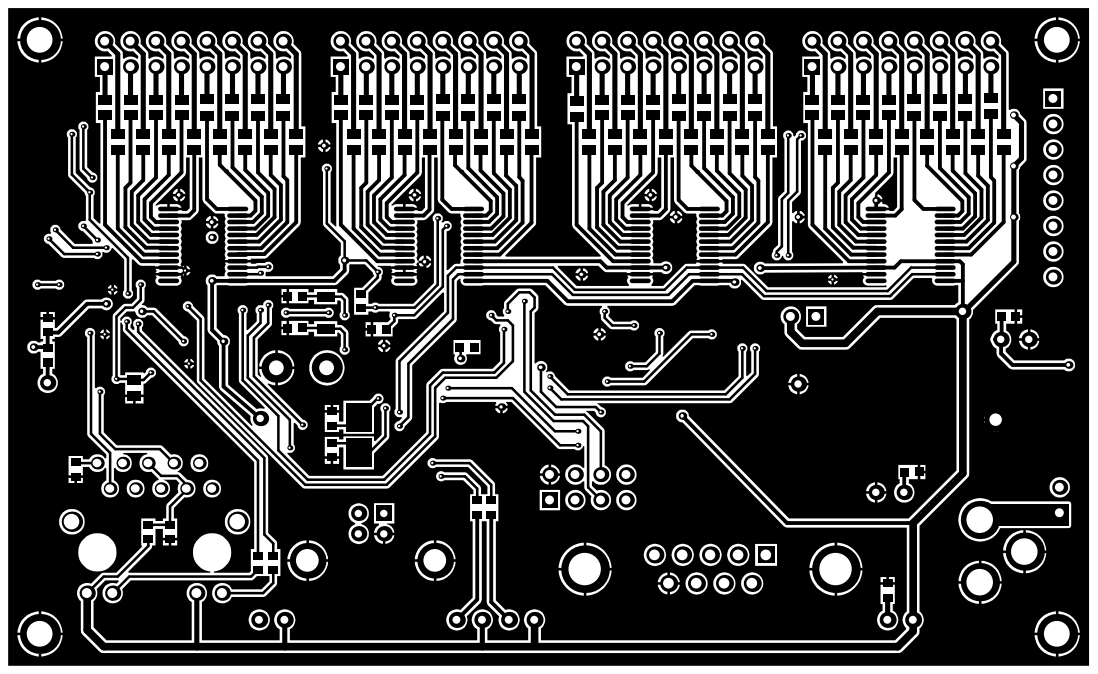
[picture p99: page 1]
