luka1995/LPProjects-LED-Cube-8x8x8/PCB/Ver 1.0.0/PDF/TOP Layer.PDF

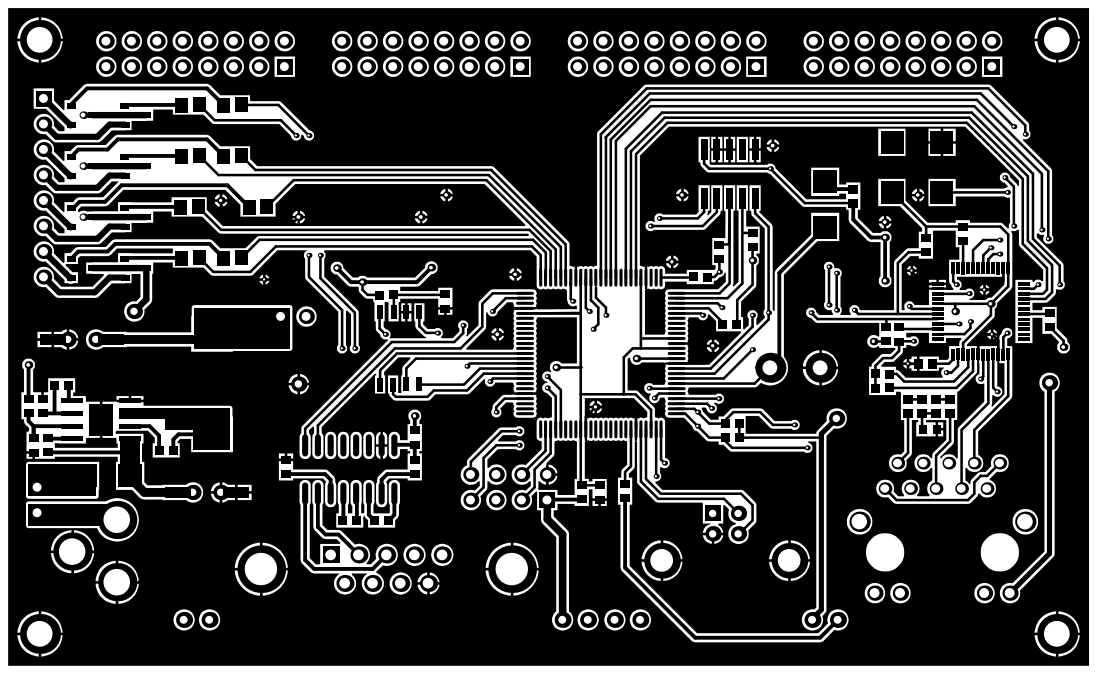
[picture p101: page 1]
