luka1995/LPProjects-LED-Cube-8x8x8/PCB/Ver 1.0.0/PDF/TOP Overlay.PDF

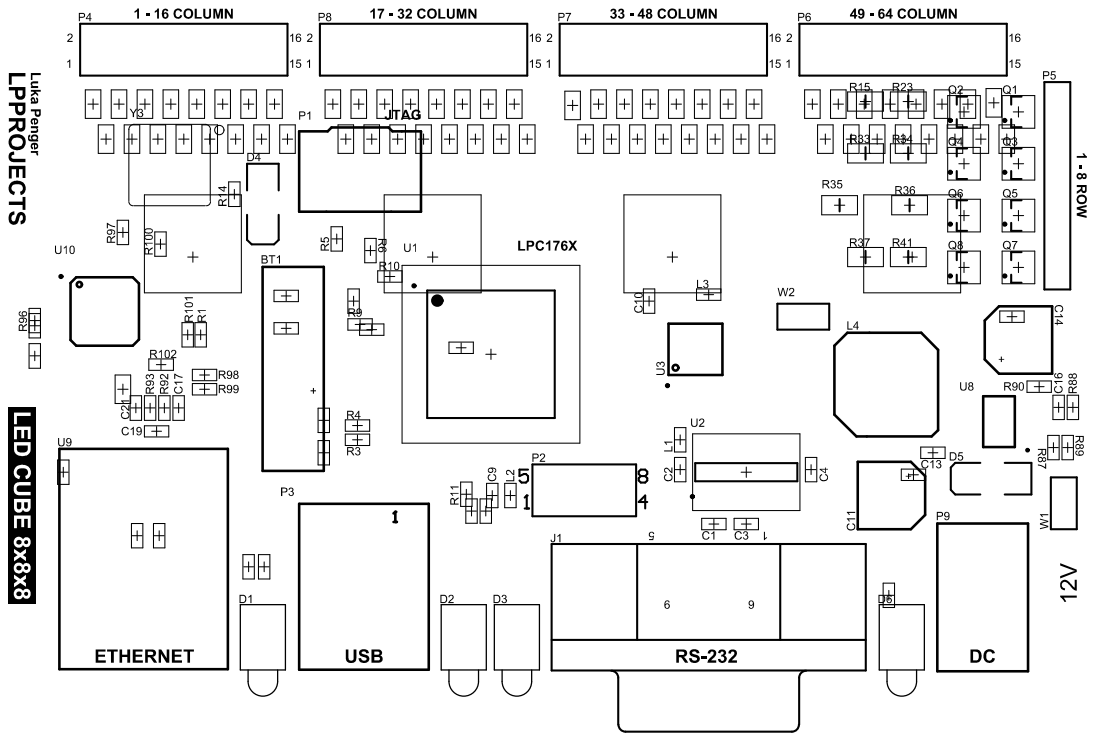
[picture p102: page 1]
