luka1995/LPProjects-LED-Cube-8x8x8/PCB/Ver 2.0.0/PDF/BOTTOM Layer.PDF

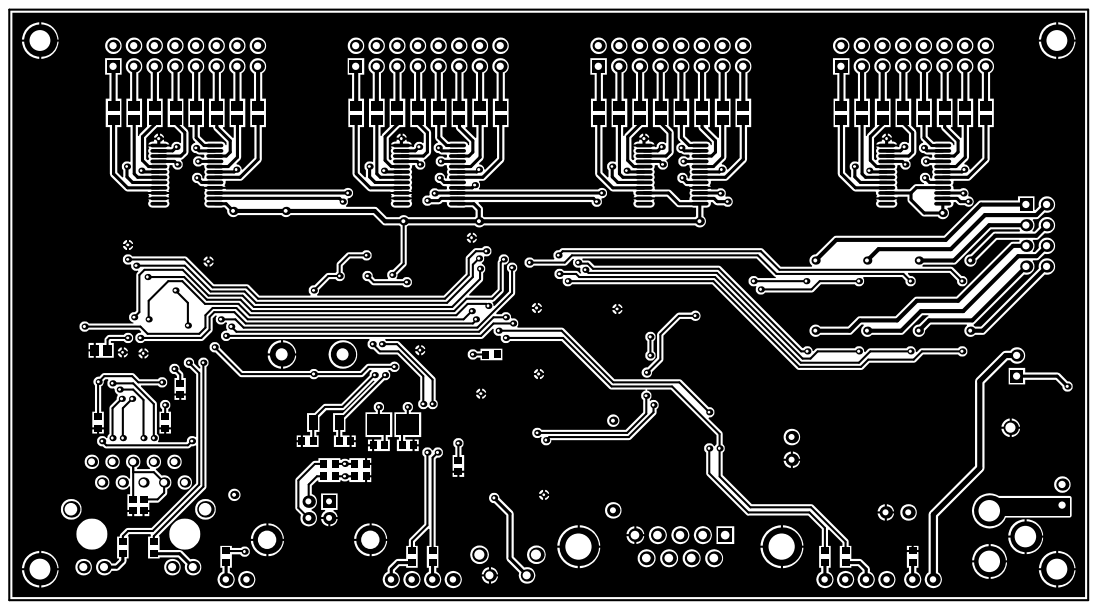
[picture p103: page 1]
