luka1995/LPProjects-LED-Cube-8x8x8/PCB/Ver 2.0.0/PDF/TOP Layer.PDF

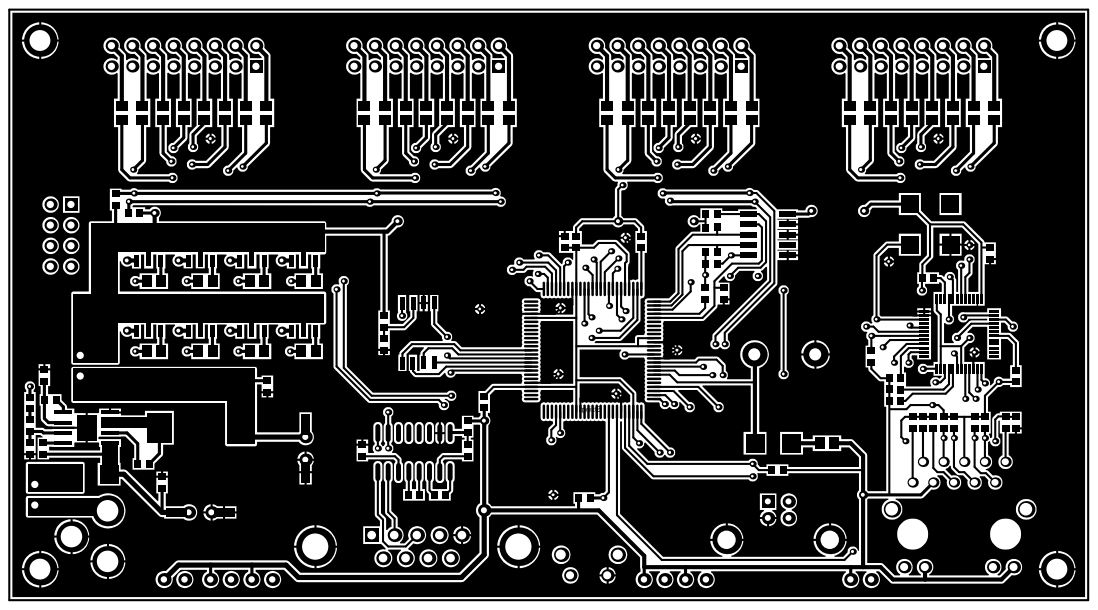
[picture p105: page 1]
