luka1995/LPProjects-LED-Cube-8x8x8/PCB/Ver 3.0.0/PDF/BOTTOM Layer.PDF

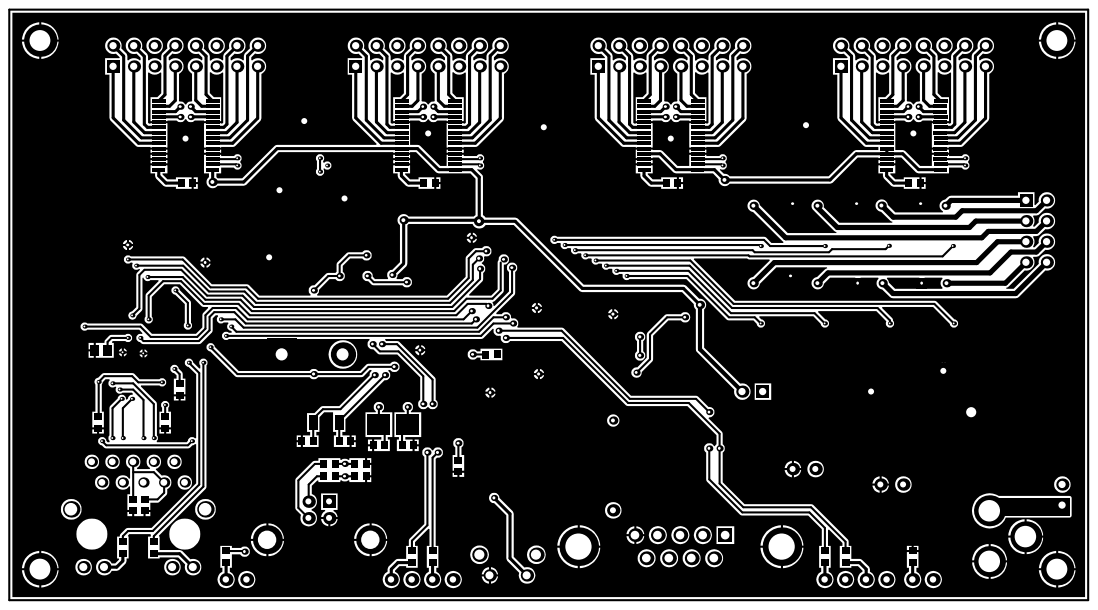
[picture p107: page 1]
