luka1995/LPProjects-LED-Cube-8x8x8/PCB/Ver 3.0.0/PDF/BOTTOM Overlay.PDF

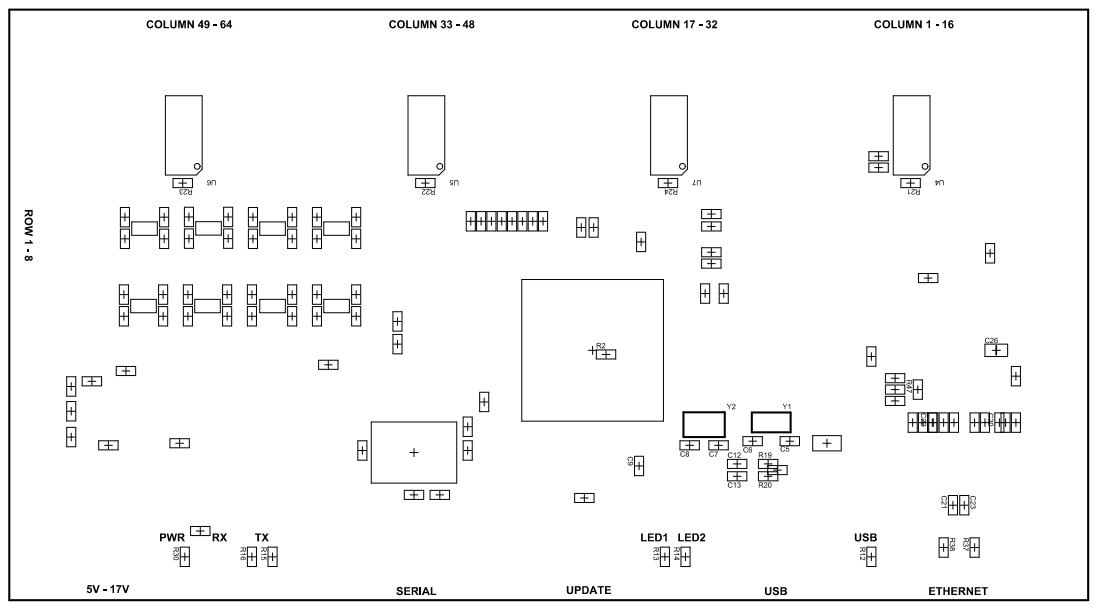
[picture p108: page 1]
