luka1995/LPProjects-LED-Cube-8x8x8/PCB/Ver 3.0.0/PDF/TOP Overlay.PDF

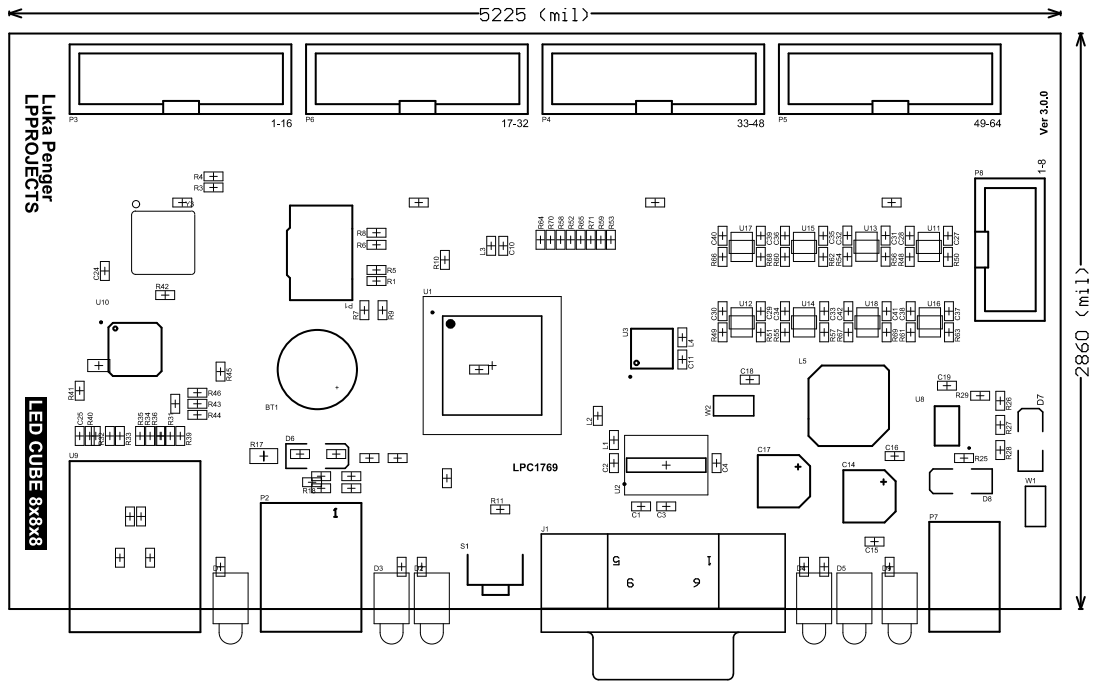
[picture p110: page 1]
