luka1995/LPProjects-LED-Cube-8x8x8/PCB/Ver 3.0.1/PDF/BOTTOM Layer.PDF

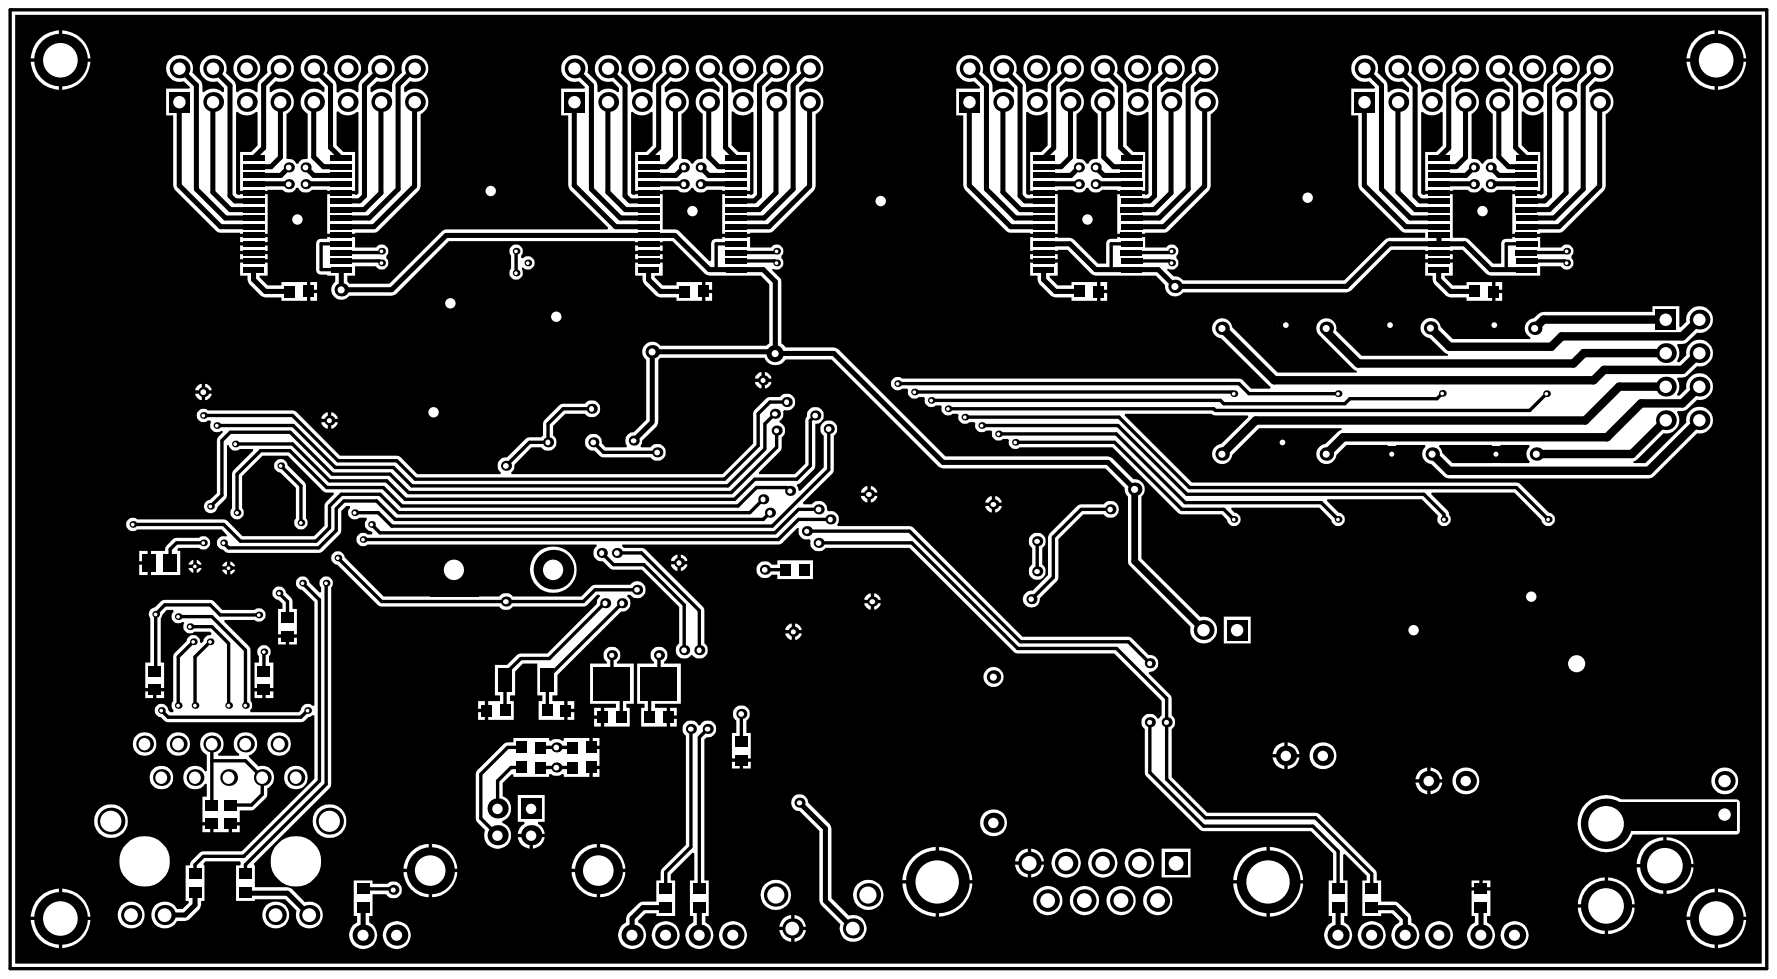
[picture p111: page 1]
