luka1995/LPProjects-LED-Cube-8x8x8/LP_LED_CUBE_8x8x8_LPC176X/3.0.1/LP_LED_CUBE_8x8x8_LPC176X/Net_Config.c

/*----------------------------------------------------------------------------
 *      RL-ARM - TCPnet
 *----------------------------------------------------------------------------
 *      Name:    NET_CONFIG.C
 *      Purpose: Configuration of RL TCPnet by user
 *      Rev.:    V4.72
 *----------------------------------------------------------------------------
 *      This code is part of the RealView Run-Time Library.
 *      Copyright (c) 2004-2013 KEIL - An ARM Company. All rights reserved.
 *---------------------------------------------------------------------------*/

#include <Net_Config.h>

//-------- <<< Use Configuration Wizard in Context Menu >>> -----------------
//
// <h>System Definitions
// =====================
// <i> Global TCPnet System definitions
//   <s.15>Local Host Name
//   <i> This is the name under which embedded host
//   <i> can be accessed on a local area network.
//   <i> Default: "mcb2300"
#define LHOST_NAME     "LED-CUBE-8x8x8"

//   <o>Memory Pool size <1536-262144:4><#/4>
//   <i> This is the size of a memory pool in bytes. Buffers for
//   <i> TCPnet packets are allocated from this memory pool.
//   <i> Default: 8000 bytes
#define MEM_SIZE       2048

//   <o>Tick Timer interval <10=> 10 ms <20=> 20 ms <25=> 25 ms
//                          <40=> 40 ms <50=> 50 ms <100=> 100 ms 
//                          <200=> 200 ms
//   <i> System Tick Timer interval for software timers
//   <i> Default: 100 ms
#define TICK_INTERVAL  100

// </h>
// <e>Ethernet Network Interface
// =============================
// <i> Enable or disable Ethernet Network Interface
#define ETH_ENABLE     1

//   <h>MAC Address
//   ==============
//   <i> Local Ethernet MAC Address
//   <i> Value FF:FF:FF:FF:FF:FF is not allowed.
//   <i> It is an ethernet Broadcast MAC address.
//     <o>Address byte 1 <0x00-0xff:2>
//     <i> LSB is an ethernet Multicast bit.
//     <i> Must be 0 for local MAC address.
//     <i> Default: 0x00
#define _MAC1          0x00

//     <o>Address byte 2 <0x00-0xff>
//     <i> Default: 0x30
#define _MAC2          0x24

//     <o>Address byte 3 <0x00-0xff>
//     <i> Default: 0x6C
#define _MAC3          0x53

//     <o>Address byte 4 <0x00-0xff>
//     <i> Default: 0x00
#define _MAC4          0xA2

//     <o>Address byte 5 <0x00-0xff>
//     <i> Default: 0x00
#define _MAC5          0x45

//     <o>Address byte 6 <0x00-0xff>
//     <i> Default: 0x01
#define _MAC6          0x02

//   </h>
//   <h>IP Address
//   =============
//   <i> Local Static IP Address
//   <i> Value 255.255.255.255 is not allowed.
//   <i> It is a Broadcast IP address.
//     <o>Address byte 1 <0-255>
//     <i> Default: 192
#define _IP1           192

//     <o>Address byte 2 <0-255>
//     <i> Default: 168
#define _IP2           168

//     <o>Address byte 3 <0-255>
//     <i> Default: 0
#define _IP3           123

//     <o>Address byte 4 <0-255>
//     <i> Default: 100
#define _IP4           200

//   </h>
//   <h>Subnet mask
//   ==============
//   <i> Local Subnet mask
//     <o>Mask byte 1 <0-255>
//     <i> Default: 255
#define _MSK1          255

//     <o>Mask byte 2 <0-255>
//     <i> Default: 255
#define _MSK2          255

//     <o>Mask byte 3 <0-255>
//     <i> Default: 255
#define _MSK3          255

//     <o>Mask byte 4 <0-255>
//     <i> Default: 0
#define _MSK4          0

//   </h>
//   <h>Default Gateway
//   ==================
//   <i> Default Gateway IP Address
//     <o>Address byte 1 <0-255>
//     <i> Default: 192
#define _GW1           192

//     <o>Address byte 2 <0-255>
//     <i> Default: 168
#define _GW2           168

//     <o>Address byte 3 <0-255>
//     <i> Default: 0
#define _GW3           3

//     <o>Address byte 4 <0-255>
//     <i> Default: 254
#define _GW4           1

//   </h>
//   <h>Primary DNS Server
//   =====================
//   <i> Primary DNS Server IP Address
//     <o>Address byte 1 <0-255>
//     <i> Default: 194
#define _pDNS1         194

//     <o>Address byte 2 <0-255>
//     <i> Default: 25
#define _pDNS2         25

//     <o>Address byte 3 <0-255>
//     <i> Default: 2
#define _pDNS3         2

//     <o>Address byte 4 <0-255>
//     <i> Default: 129
#define _pDNS4         129

//   </h>
//   <h>Secondary DNS Server
//   =======================
//   <i> Secondary DNS Server IP Address
//     <o>Address byte 1 <0-255>
//     <i> Default: 194
#define _sDNS1         194

//     <o>Address byte 2 <0-255>
//     <i> Default: 25
#define _sDNS2         25

//     <o>Address byte 3 <0-255>
//     <i> Default: 2
#define _sDNS3         2

//     <o>Address byte 4 <0-255>
//     <i> Default: 130
#define _sDNS4         130

//   </h>
//   <h>ARP Definitions
//   ==================
//   <i> Address Resolution Protocol Definitions
//     <o>Cache Table size <5-100>
//     <i> Number of cached hardware/IP addresses
//     <i> Default: 10
#define ARP_TABSIZE    10

//     <o>Cache Timeout in seconds <5-255>
//     <i> A timeout for a cached hardware/IP addresses
//     <i> Default: 150
#define ARP_TIMEOUT    150

//     <o>Number of Retries <0-20>
//     <i> Number of Retries to resolve an IP address
//     <i> before ARP module gives up
//     <i> Default: 4
#define ARP_MAXRETRY   4

//     <o>Resend Timeout in seconds <1-10>
//     <i> A timeout to resend the ARP Request
//     <i> Default: 2
#define ARP_RESEND     2

//     <q>Send Notification on Address changes
//     <i> When this option is enabled, the embedded host
//     <i> will send a Gratuitous ARP notification at startup,
//     <i> or when the device IP address has changed.
//     <i> Default: Disabled
#define ARP_NOTIFY     0

//   </h>
//   <e>IGMP Group Management
//   ========================
//   <i> Enable or disable Internet Group Management Protocol
#define IGMP_ENABLE    0

//     <o>Membership Table size <2-50>
//     <i> Number of Groups this host can join
//     <i> Default: 5
#define IGMP_TABSIZE   5

//   </e>
//   <q>NetBIOS Name Service
//   =======================
//   <i> When this option is enabled, the embedded host can be
//   <i> accessed by his name on the local LAN using NBNS protocol.
#define NBNS_ENABLE    1

//   <e>Dynamic Host Configuration
//   =============================
//   <i> When this option is enabled, local IP address, Net Mask
//   <i> and Default Gateway are obtained automatically from
//   <i> the DHCP Server on local LAN.
#define DHCP_ENABLE    1

//     <s.40>Vendor Class Identifier
//     <i> This value is optional. If specified, it is added
//     <i> to DHCP request message, identifying vendor type.
//     <i> Default: ""
#define DHCP_VCID      "Initra d.o.o."

//     <q>Bootfile Name
//     <i> This value is optional. If enabled, the Bootfile Name
//     <i> (option 67) is also requested from DHCP server.
//     <i> Default: disabled
#define DHCP_BOOTF     0

//     <q>NTP Servers
//     <i> This value is optional. If enabled, a list of NTP Servers
//     <i> (option 42) is also requested from DHCP server.
//     <i> Default: disabled
#define DHCP_NTPSRV    0

//   </e>
// </e>

// <e>PPP Network Interface
// ========================
// <i> Enable or disable PPP Network Interface
#define PPP_ENABLE     0

//   <h>IP Address
//   =============
//   <i> Local Static IP Address
//     <o>Address byte 1 <0-255>
//     <i> Default: 192
#define _IP1P          192

//     <o>Address byte 2 <0-255>
//     <i> Default: 168
#define _IP2P          168

//     <o>Address byte 3 <0-255>
//     <i> Default: 125
#define _IP3P          125

//     <o>Address byte 4 <0-255>
//     <i> Default: 1
#define _IP4P          1

//   </h>
//   <h>Subnet mask
//   ==============
//   <i> Local Subnet mask
//     <o>Mask byte 1 <0-255>
//     <i> Default: 255
#define _MSK1P         255

//     <o>Mask byte 2 <0-255>
//     <i> Default: 255
#define _MSK2P         255

//     <o>Mask byte 3 <0-255>
//     <i> Default: 255
#define _MSK3P         255

//     <o>Mask byte 4 <0-255>
//     <i> Default: 0
#define _MSK4P         0

//   </h>
//   <h>Primary DNS Server
//   =====================
//   <i> Primary DNS Server IP Address
//     <o>Address byte 1 <0-255>
//     <i> Default: 194
#define _pDNS1P        194

//     <o>Address byte 2 <0-255>
//     <i> Default: 25
#define _pDNS2P        25

//     <o>Address byte 3 <0-255>
//     <i> Default: 2
#define _pDNS3P        2

//     <o>Address byte 4 <0-255>
//     <i> Default: 129
#define _pDNS4P        129

//   </h>
//   <h>Secondary DNS Server
//   =======================
//   <i> Secondary DNS Server IP Address
//     <o>Address byte 1 <0-255>
//     <i> Default: 194
#define _sDNS1P        194

//     <o>Address byte 2 <0-255>
//     <i> Default: 25
#define _sDNS2P        25

//     <o>Address byte 3 <0-255>
//     <i> Default: 2
#define _sDNS3P        2

//     <o>Address byte 4 <0-255>
//     <i> Default: 130
#define _sDNS4P        130

//   </h>
//   <e>Logon Authentication
//   =======================
//   <i> Enable or disable user authentication
#define PPP_AUTHEN     1

//     <q>Unsecured password (PAP)
//     <i>Allow or use Password Authentication Protocol.
#define PPP_PAPEN      1

//     <q>Secured password (CHAP-MD5)
//     <i>Request or use Challenge Handshake Authentication
//     <i>Protocol with MD5 digest algorithm.
#define PPP_CHAPEN     1

//   </e>
//   <q>Obtain Client IP address automatically
//   =========================================
//   <i> This option only applies when PPP Dial-up is used to dial
//   <i> to remote PPP Server. If checked, network connection
//   <i> dynamically obtains an IP address from remote PPP Server.
#define PPP_GETIP      1

//   <q>Use Default Gateway on remote Network
//   ========================================
//   <i> This option only applies when both Ethernet and PPP Dial-up
//   <i> are used. If checked, data that cannot be sent to local LAN
//   <i> is forwarded to Dial-up network instead.
#define PPP_DEFGW      1

//   <o>Async Control Character Map <0x0-0xffffffff>
//   <i> A bit-map of control characters 0-31, which are
//   <i> transmitted escaped as a 2 byte sequence.
//   <i> For XON/XOFF set this value to: 0x000A 0000
//   <i> Default: 0x00000000
#define PPP_ACCM       0x00000000

//   <o>LCP Echo Interval in seconds <0-3600>
//   <i> If no frames are received within this interval, PPP sends an
//   <i> Echo Request and expects an Echo Response from the peer.
//   <i> If the response is not received, the link is terminated.
//   <i> A value of 0 disables the LCP Echo test.
//   <i> Default: 30
#define PPP_ECHOTOUT   30

//   <o>Number of Retries <0-20>
//   <i> How many times PPP will try to retransmit data
//   <i> before giving up. Increase this value for links
//   <i> with low baud rates or high latency.
//   <i> Default: 3
#define PPP_MAXRETRY   3

//   <o>Retry Timeout in seconds <1-10>
//   <i> If no response received within this time frame,
//   <i> PPP module will try to resend the data again.
//   <i> Default: 2
#define PPP_RETRYTOUT  2

// </e>
// <e>SLIP Network Interface
// ========================
// <i> Enable or disable SLIP Network Interface
#define SLIP_ENABLE    0

//   <h>IP Address
//   =============
//   <i> Local Static IP Address
//     <o>Address byte 1 <0-255>
//     <i> Default: 192
#define _IP1S          192

//     <o>Address byte 2 <0-255>
//     <i> Default: 168
#define _IP2S          168

//     <o>Address byte 3 <0-255>
//     <i> Default: 225
#define _IP3S          225

//     <o>Address byte 4 <0-255>
//     <i> Default: 1
#define _IP4S          1

//   </h>
//   <h>Subnet mask
//   ==============
//   <i> Local Subnet mask
//     <o>Mask byte 1 <0-255>
//     <i> Default: 255
#define _MSK1S         255

//     <o>Mask byte 2 <0-255>
//     <i> Default: 255
#define _MSK2S         255

//     <o>Mask byte 3 <0-255>
//     <i> Default: 255
#define _MSK3S         255

//     <o>Mask byte 4 <0-255>
//     <i> Default: 0
#define _MSK4S         0

//   </h>
//   <h>Primary DNS Server
//   =====================
//   <i> Primary DNS Server IP Address
//     <o>Address byte 1 <0-255>
//     <i> Default: 194
#define _pDNS1S        194

//     <o>Address byte 2 <0-255>
//     <i> Default: 25
#define _pDNS2S        25

//     <o>Address byte 3 <0-255>
//     <i> Default: 2
#define _pDNS3S        2

//     <o>Address byte 4 <0-255>
//     <i> Default: 129
#define _pDNS4S        129

//   </h>
//   <h>Secondary DNS Server
//   =======================
//   <i> Secondary DNS Server IP Address
//     <o>Address byte 1 <0-255>
//     <i> Default: 194
#define _sDNS1S        194

//     <o>Address byte 2 <0-255>
//     <i> Default: 25
#define _sDNS2S        25

//     <o>Address byte 3 <0-255>
//     <i> Default: 2
#define _sDNS3S        2

//     <o>Address byte 4 <0-255>
//     <i> Default: 130
#define _sDNS4S        130

//   </h>
//   <q>Use Default Gateway on remote Network
//   ========================================
//   <i> This option only applies when both Ethernet and SLIP Dial-up
//   <i> are used. If checked, data that cannot be sent to local LAN
//   <i> is forwarded to Dial-up network instead.
#define SLIP_DEFGW     1

// </e>
// <e>UDP Sockets
// ==============
// <i> Enable or disable UDP Sockets
#define UDP_ENABLE     1

//   <o>Number of UDP Sockets <1-20>
//   <i> Number of available UDP sockets
//   <i> Default: 5
#define UDP_NUMSOCKS   5

// </e>
// <e>TCP Sockets
// ==============
// <i> Enable or disable TCP Sockets
#define TCP_ENABLE     1

//   <o>Number of TCP Sockets <1-20>
//   <i> Number of available TCP sockets
//   <i> Default: 5
#define TCP_NUMSOCKS   20

//   <o>Number of Retries <0-20>
//   <i> How many times TCP module will try to retransmit data
//   <i> before giving up. Increase this value for high-latency
//   <i> and low_throughput networks.
//   <i> Default: 5
#define TCP_MAXRETRY   5

//   <o>Retry Timeout in seconds <1-10>
//   <i> If data frame not acknowledged within this time frame,
//   <i> TCP module will try to resend the data again.
//   <i> Default: 4
#define TCP_RETRYTOUT  4

//   <o>Default Connect Timeout in seconds <1-600>
//   <i> Default TCP Socket Keep Alive timeout. When it expires
//   <i> with no TCP data frame send, TCP Connection is closed.
//   <i> Default: 120
#define TCP_DEFTOUT    600

//   <o>Maximum Segment Size <536-1460>
//   <i> The Maximum Segment Size specifies the maximum
//   <i> number of bytes in the TCP segment's Data field.
//   <i> Default: 1460
#define TCP_MAXSEGSZ   1460

//   <o>Receive Window Size <536-65535>
//   <i> Receive Window Size specifies the size of data, 
//   <i> that the socket is able to buffer in flow-control mode.
//   <i> Default: 4380
#define TCP_RECWINSZ   4380

/* TCP fixed timeouts */
#define TCP_INIT_RETRY_TOUT 1     /* TCP initial Retransmit period in sec.   */
#define TCP_SYN_RETRY_TOUT  2     /* TCP SYN frame retransmit period in sec. */
#define TCP_CONRETRY        7     /* Number of retries to establish a conn.  */

// </e>
// <e>HTTP Server
// ==============
// <i> Enable or disable HTTP Server
#define HTTP_ENABLE    1

//   <o>Number of HTTP Sessions <1-10>
//   <i> Number of simultaneously active HTTP Sessions.
//   <i> Default: 3
#define HTTP_NUMSESS   6

//   <o>Port Number <1-65535>
//   <i> Listening port number.
//   <i> Default: 80
#define HTTP_PORTNUM   80

//   <s.50>Server-Id header
//   <i> This value is optional. If specified, it overrides 
//   <i> the default HTTP Server header from the library.
//   <i> Default: ""
#define HTTP_SRVID     ""

//   <e>Enable User Authentication
//     <i> When enabled, the user will have to authenticate
//     <i> himself by username and password before accessing
//     <i> any page on this Embedded WEB server.
#define HTTP_ENAUTH    1

//     <s.30>Authentication Realm
//     <i> Default: "Embedded WEB Server"
#define HTTP_AUTHREALM "WEB Server"

//     <s.15>Authentication Username
//     <i> Default: "admin"
#define HTTP_AUTHUSER  "manufacturer"

//     <s.15>Authentication Password
//     <i> Default: ""
#define HTTP_AUTHPASSW "manufacturer"

//   </e>
// </e>
// <e>Telnet Server
// ================
// <i> Enable or disable Telnet Server
#define TNET_ENABLE    0

//   <o>Number of Telnet Connections <1-10>
//   <i> Number of simultaneously active Telnet Connections.
//   <i> Default: 1
#define TNET_NUMSESS   2

//   <o>Port Number <1-65535>
//   <i> Listening port number.
//   <i> Default: 23
#define TNET_PORTNUM   23

//   <o>Idle Connection Timeout in seconds <0-3600>
//   <i> When timeout expires, the connection is closed.
//   <i> A value of 0 disables disconnection on timeout.
//   <i> Default: 120
#define TNET_IDLETOUT  120

//   <q>Disable Echo
//   <i> When disabled, the server will not echo
//   <i> characters it receives.
//   <i> Default: Not disabled
#define TNET_NOECHO    0

//   <e>Enable User Authentication
//   <i> When enabled, the user will have to authenticate
//   <i> himself by username and password before access
//   <i> to the system is allowed.
#define TNET_ENAUTH    1

//     <s.15>Authentication Username
//     <i> Default: "admin"
#define TNET_AUTHUSER  "admin"

//     <s.15>Authentication Password
//     <i> Default: ""
#define TNET_AUTHPASSW "admin"

//   </e>
// </e>
// <e>TFTP Server
// ==============
// <i> Enable or disable TFTP Server
#define TFTP_ENABLE    0

//   <o>Number of TFTP Sessions <1-10>
//   <i> Number of simultaneously active TFTP Sessions
//   <i> Default: 1
#define TFTP_NUMSESS   1

//   <o>Port Number <1-65535>
//   <i> Listening port number.
//   <i> Default: 69
#define TFTP_PORTNUM   69

//   <q>Enable Firewall Support
//   <i> Use the same Port Number to receive
//   <i> requests and send answers to clients.
//   <i> Default: Not Enabled
#define TFTP_ENFWALL   0

//   <o>Inactive Session Timeout in seconds <5-120>
//   <i> When timeout expires TFTP Session is closed.
//   <i> Default: 15
#define TFTP_DEFTOUT   15

//   <o>Number of Retries <1-10>
//   <i> How many times TFTP Server will try to
//   <i> retransmit the data before giving up.
//   <i> Default: 4
#define TFTP_MAXRETRY  4

// </e>
// <e>TFTP Client
// ==============
// <i> Enable or disable TFTP Client
#define TFTPC_ENABLE   0

//   <o>Block Size <128=>128   <256=>256   <512=>512
//                 <1024=>1024 <1428=>1428
//   <i> Size of transfer block in bytes.
//   <i> Default: 512
#define TFTPC_BLOCKSZ  512

//   <o>Number of Retries <1-10>
//   <i> How many times TFTP Client will try to
//   <i> retransmit the data before giving up.
//   <i> Default: 4
#define TFTPC_MAXRETRY 4

//   <o>Retry Timeout <2=>200 ms <5=>500 ms <10=>1 sec
//                    <20=>2 sec <50=>5 sec <100=>10 sec
//   <i> If data frame not acknowledged within this time frame,
//   <i> TFTP Client will try to resend the data again.
//   <i> Default: 500 ms
#define TFTPC_RETRYTO  5

// </e>
// <e>FTP Server
// ==============
// <i> Enable or disable FTP Server
#define FTP_ENABLE     1

//   <o>Number of FTP Sessions <1-10>
//   <i> Number of simultaneously active FTP Sessions
//   <i> Default: 1
#define FTP_NUMSESS    2

//   <o>Port Number <1-65535>
//   <i> Listening port number.
//   <i> Default: 21
#define FTP_PORTNUM    21

//   <s.50>Welcome Message
//   <i> This value is optional. If specified,
//   <i> it overrides the default welcome message.
//   <i> Default: ""
#define FTP_WELMSG     "FTP Server"

//   <o>Idle Session Timeout in seconds <0-3600>
//   <i> When timeout expires, the connection is closed.
//   <i> A value of 0 disables disconnection on timeout.
//   <i> Default: 120
#define FTP_IDLETOUT   120

//   <e>Enable User Authentication
//   <i> When enabled, the user will have to authenticate
//   <i> himself by username and password before access
//   <i> to the system is allowed.
#define FTP_ENAUTH     1

//     <s.15>Authentication Username
//     <i> Default: "admin"
#define FTP_AUTHUSER   "manufacturer"

//     <s.15>Authentication Password
//     <i> Default: ""
#define FTP_AUTHPASSW  "manufacturer"

//   </e>
// </e>
// <e>FTP Client
// =============
// <i> Enable or disable FTP Client
#define FTPC_ENABLE    0

//     <o>Response Timeout in seconds <1-120>
//     <i> This is a time for FTP Client to wait for a response from
//     <i> the Server. If timeout expires, Client aborts operation.
//     <i> Default: 10
#define FTPC_DEFTOUT   10

//     <q>Passive mode (PASV)
//     <i> The client initiates a data connection to the server.
//     <i> Default: Not passive (Active)
#define FTPC_PASVMODE  0

// </e>
// <e>DNS Client
// =============
// <i> Enable or disable DNS Client
#define DNS_ENABLE     0

//     <o>Cache Table size <5-100>
//     <i> Number of cached DNS host names/IP addresses
//     <i> Default: 20
#define DNS_TABSIZE    20

// </e>
// <e>SMTP Client
// ==============
// <i> Enable or disable SMTP Client
#define SMTP_ENABLE    0

//     <o>Response Timeout in seconds <5-120>
//     <i> This is a time for SMTP Client to wait for a response from
//     <i> SMTP Server. If timeout expires, Client aborts operation.
//     <i> Default: 20
#define SMTP_DEFTOUT   20

// </e>
// <e>SNMP Agent
// =============
// <i> Enable or disable SNMP Agent
#define SNMP_ENABLE    0

//   <s.15>Community Name
//   <i> Defines where an SNMP message is destined for.
//   <i> Default: "public"
#define SNMP_COMMUNITY "public"

//   <o>Port Number <1-65535>
//   <i> Listening port number.
//   <i> Default: 161
#define SNMP_PORTNUM   161

//   <o>Trap Port Number <1-65535>
//   <i> Port number for Trap operations.
//   <i> Default: 162
#define SNMP_TRAPPORT  162

//   <h>Trap Server
//   ==============
//   <i> Trap Server IP Address
//   <o>Address byte 1 <0-255>
//   <i> Default: 192
#define SNMP_TRAPIP1   192

//   <o>Address byte 2 <0-255>
//   <i> Default: 168
#define SNMP_TRAPIP2   168

//   <o>Address byte 3 <0-255>
//   <i> Default: 0
#define SNMP_TRAPIP3   0

//   <o>Address byte 4 <0-255>
//   <i> Default: 100
#define SNMP_TRAPIP4   1

//   </h>
// </e>
// <e>SNTP Client
// ==============
// <i> Enable or disable SNTP Client
#define SNTP_ENABLE    1

//   <q>Broadcast Mode
//   =================
//   <i> Enable this option, if you have NTP/SNTP server
//   <i> on LAN, which is broadcasting NTP time messages.
//   <i> Disable this option to access public NTP server.
//   <i> Default: disabled
#define SNTP_BCMODE    0

//   <h>NTP Server
//   =============
//   <i> Server IP Address
//   <o>Address byte 1 <0-255>
//   <i> Default: 217
#define SNTP_SRVIP1    217

//   <o>Address byte 2 <0-255>
//   <i> Default: 79
#define SNTP_SRVIP2    79

//   <o>Address byte 3 <0-255>
//   <i> Default: 179
#define SNTP_SRVIP3    179

//   <o>Address byte 4 <0-255>
//   <i> Default: 106
#define SNTP_SRVIP4    106

//   </h>
// </e>
// <e>BSD Socket Interface
// =======================
// <i> Enable or disable Berkeley Socket Programming Interface
#define BSD_ENABLE     0

//   <o>Number of BSD Sockets <1-20>
//   <i> Number of available Berkeley Sockets
//   <i> Default: 2
#define BSD_NUMSOCKS   2

//   <o>Number of Streaming Server Sockets <0-20>
//   <i> Defines a number of Streaming (TCP) Server sockets,
//   <i> that listen for an incoming connection from the client.
//   <i> Default: 1
#define BSD_SRVSOCKS   1

//   <o>Receive Timeout in seconds <0-600>
//   <i> A timeout for socket receive in blocking mode.
//   <i> Timeout value of 0 means indefinite timeout.
//   <i> Default: 20
#define BSD_RCVTOUT    20

//   <q>Hostname Resolver
//   <i> Enable or disable Berkeley style hostname resolver.
#define BSD_GETHOSTEN  0

// </e>
//------------- <<< end of configuration section >>> -----------------------

/*----------------------------------------------------------------------------
 *      Fatal Error Handler
 *---------------------------------------------------------------------------*/

void sys_error (ERROR_CODE code) {
  /* This function is called when a fatal error is encountered. The normal */
  /* program execution is not possible anymore. Add your crytical error   .*/
  /* handler code here.                                                    */

  switch (code) {
    case ERR_MEM_ALLOC:
      /* Out of memory. */
      break;

    case ERR_MEM_FREE:
      /* Trying to release non existing memory block. */
      break;

    case ERR_MEM_CORRUPT:
      /* Memory Link pointer is Corrupted. */
      /* More data written than the size of allocated mem block. */
      break;

    case ERR_MEM_LOCK:
      /* Locked Memory management function (alloc/free) re-entered. */
      /* RTX multithread protection malfunctioning, not implemented */
      /* or interrupt disable is not functioning correctly. */
      break;

    case ERR_UDP_ALLOC:
      /* Out of UDP Sockets. */
      break;

    case ERR_TCP_ALLOC:
      /* Out of TCP Sockets. */
      break;

    case ERR_TCP_STATE:
      /* TCP State machine in undefined state. */
      break;
  }

  /* End-less loop */
  while (1);
}

/*----------------------------------------------------------------------------
 *      TCPnet Config Functions
 *---------------------------------------------------------------------------*/

#define  __NET_CONFIG__

#include <Net_lib.c>

/*----------------------------------------------------------------------------
 * end of file
 *---------------------------------------------------------------------------*/
