luka1995/LPProjects-LED-Cube-8x8x8/LP_LED_CUBE_8x8x8_LPC176X/3.0.1/LPC1700 Secondary USB bootloader/usb/usbdesc.c

/*----------------------------------------------------------------------------
 *      U S B  -  K e r n e l
 *----------------------------------------------------------------------------
 *      Name:    USBDESC.C
 *      Purpose: USB Descriptors
 *      Version: V1.10
 *----------------------------------------------------------------------------
 *      This file is part of the uVision/ARM development tools.
 *      This software may only be used under the terms of a valid, current,
 *      end user licence from KEIL for a compatible version of KEIL software
 *      development tools. Nothing else gives you the right to use it.
 *
 *      Copyright (c) 2005-2007 Keil Software.
 *---------------------------------------------------------------------------*/

#include "type.h"

#include "usb.h"
#include "msc.h"
#include "usbcfg.h"
#include "usbdesc.h"


/* USB Standard Device Descriptor */
const uint8_t USB_DeviceDescriptor[] = {
  USB_DEVICE_DESC_SIZE,              /* bLength */
  USB_DEVICE_DESCRIPTOR_TYPE,        /* bDescriptorType */
  WBVAL(0x0110), /* 1.10 */          /* bcdUSB */
  0x00,                              /* bDeviceClass */
  0x00,                              /* bDeviceSubClass */
  0x00,                              /* bDeviceProtocol */
  USB_MAX_PACKET0,                   /* bMaxPacketSize0 */
  WBVAL(0xC251),                     /* idVendor */
  WBVAL(0x1303),                     /* idProduct */
  WBVAL(0x0100), /* 1.00 */          /* bcdDevice */
  0x04,                              /* iManufacturer */
  0x20,                              /* iProduct */
  0x48,                              /* iSerialNumber */
  0x01                               /* bNumConfigurations */
};

/* USB Configuration Descriptor */
/*   All Descriptors (Configuration, Interface, Endpoint, Class, Vendor */
const uint8_t USB_ConfigDescriptor[] = {
/* Configuration 1 */
  USB_CONFIGUARTION_DESC_SIZE,       /* bLength */
  USB_CONFIGURATION_DESCRIPTOR_TYPE, /* bDescriptorType */
  WBVAL(                             /* wTotalLength */
    1*USB_CONFIGUARTION_DESC_SIZE +
    1*USB_INTERFACE_DESC_SIZE     +
    2*USB_ENDPOINT_DESC_SIZE
  ),
  0x01,                              /* bNumInterfaces */
  0x01,                              /* bConfigurationValue */
  0x00,                              /* iConfiguration */
  USB_CONFIG_BUS_POWERED /*|*/       /* bmAttributes */
/*USB_CONFIG_REMOTE_WAKEUP*/,
  USB_CONFIG_POWER_MA(100),          /* bMaxPower */
/* Interface 0, Alternate Setting 0, MSC Class */
  USB_INTERFACE_DESC_SIZE,           /* bLength */
  USB_INTERFACE_DESCRIPTOR_TYPE,     /* bDescriptorType */
  0x00,                              /* bInterfaceNumber */
  0x00,                              /* bAlternateSetting */
  0x02,                              /* bNumEndpoints */
  USB_DEVICE_CLASS_STORAGE,          /* bInterfaceClass */
  MSC_SUBCLASS_SCSI,                 /* bInterfaceSubClass */
  MSC_PROTOCOL_BULK_ONLY,            /* bInterfaceProtocol */
  0x62,                              /* iInterface */
/* Bulk In Endpoint */
  USB_ENDPOINT_DESC_SIZE,            /* bLength */
  USB_ENDPOINT_DESCRIPTOR_TYPE,      /* bDescriptorType */
  USB_ENDPOINT_IN(2),                /* bEndpointAddress */
  USB_ENDPOINT_TYPE_BULK,            /* bmAttributes */
  WBVAL(0x0040),                     /* wMaxPacketSize */
  0,                                 /* bInterval */
/* Bulk Out Endpoint */
  USB_ENDPOINT_DESC_SIZE,            /* bLength */
  USB_ENDPOINT_DESCRIPTOR_TYPE,      /* bDescriptorType */
  USB_ENDPOINT_OUT(2),               /* bEndpointAddress */
  USB_ENDPOINT_TYPE_BULK,            /* bmAttributes */
  WBVAL(0x0040),                     /* wMaxPacketSize */
  0,                                 /* bInterval */
/* Terminator */
  0                                  /* bLength */
};

/* USB String Descriptor (optional) */
const uint8_t USB_StringDescriptor[] = {
/* Index 0x00: LANGID Codes */
  0x04,                              /* bLength */
  USB_STRING_DESCRIPTOR_TYPE,        /* bDescriptorType */
  WBVAL(0x0409), /* US English */    /* wLANGID */
/* Index 0x04: Manufacturer */
  0x1C,                              /* bLength */
  USB_STRING_DESCRIPTOR_TYPE,        /* bDescriptorType */
  'N',0,
  'X',0,
  'P',0,
  ' ',0,
  'S',0,
  'e',0,
  'm',0,
  'i',0,
  'c',0,
  'o',0,
  'n',0,
  'd',0,
  ' ',0,
/* Index 0x20: Product */
  0x28,                              /* bLength */
  USB_STRING_DESCRIPTOR_TYPE,        /* bDescriptorType */
  'N',0,
  'X',0,
  'P',0,
  ' ',0,
  'L',0,
  'P',0,
  'C',0,
  '1',0,
  '7',0,
  'x',0,
  'x',0,
  ' ',0,
  'M',0,
  'e',0,
  'm',0,
  'o',0,
  'r',0,
  'y',0,
  ' ',0,
/* Index 0x48: Serial Number */
  0x1A,                              /* bLength */
  USB_STRING_DESCRIPTOR_TYPE,        /* bDescriptorType */
  'D',0,
  'E',0,
  'M',0,
  'O',0,
  '0',0,
  '0',0,
  '0',0,
  '0',0,
  '0',0,
  '0',0,
  '0',0,
  '0',0,
/* Index 0x62: Interface 0, Alternate Setting 0 */
  0x0E,                              /* bLength */
  USB_STRING_DESCRIPTOR_TYPE,        /* bDescriptorType */
  'M',0,
  'e',0,
  'm',0,
  'o',0,
  'r',0,
  'y',0,
};
